aTanguay/Enssemble.io/GM_VOICINGS.md

# SAM2695 GM Voicing Reference
### All 128 General MIDI Programs + MT-32 Bank

Use Program Change (PC) messages to select voices. Send CC 0 = 0 for GM bank, CC 0 = 127 for MT-32 bank, followed by PC message.

---

## Bank 0 — General MIDI

### 🎹 Piano (PC 0–7)
| PC | Name |
|----|---|
| 0 | Acoustic Grand Piano |
| 1 | Bright Acoustic Piano |
| 2 | Electric Grand Piano |
| 3 | Honky-Tonk Piano |
| 4 | Electric Piano 1 |
| 5 | Electric Piano 2 |
| 6 | Harpsichord |
| 7 | Clavi |

### 🔔 Chromatic Percussion (PC 8–15)
| PC | Name |
|----|---|
| 8 | Celesta |
| 9 | Glockenspiel |
| 10 | Music Box |
| 11 | Vibraphone |
| 12 | Marimba |
| 13 | Xylophone |
| 14 | Tubular Bells |
| 15 | Santur |

### 🎹 Organ (PC 16–23)
| PC | Name |
|----|---|
| 16 | Drawbar Organ |
| 17 | Percussive Organ |
| 18 | Rock Organ |
| 19 | Church Organ |
| 20 | Reed Organ |
| 21 | Accordion |
| 22 | Harmonica |
| 23 | Tango Accordion |

### 🎸 Guitar (PC 24–31)
| PC | Name |
|----|---|
| 24 | Nylon Guitar |
| 25 | Steel Guitar |
| 26 | Jazz Guitar |
| 27 | Clean Guitar |
| 28 | Muted Guitar |
| 29 | Overdrive Guitar |
| 30 | Distortion Guitar |
| 31 | Guitar Harmonics |

### 🎸 Bass (PC 32–39)
| PC | Name |
|----|---|
| 32 | Acoustic Bass |
| 33 | Finger Bass |
| 34 | Pick Bass |
| 35 | Fretless Bass |
| 36 | Slap Bass 1 |
| 37 | Slap Bass 2 |
| 38 | Synth Bass 1 |
| 39 | Synth Bass 2 |

### 🎻 Strings (PC 40–47)
| PC | Name |
|----|---|
| 40 | Violin |
| 41 | Viola |
| 42 | Cello |
| 43 | Contrabass |
| 44 | Tremolo Strings |
| 45 | Pizzicato Strings |
| 46 | Orchestral Harp |
| 47 | Timpani |

### 🎻 Ensemble (PC 48–55)
| PC | Name |
|----|---|
| 48 | String Ensemble 1 |
| 49 | String Ensemble 2 |
| 50 | Synth Strings 1 |
| 51 | Synth Strings 2 |
| 52 | Choir Aahs |
| 53 | Voice Oohs |
| 54 | Synth Voice |
| 55 | Orchestra Hit |

### 🎺 Brass (PC 56–63)
| PC | Name |
|----|---|
| 56 | Trumpet |
| 57 | Trombone |
| 58 | Tuba |
| 59 | Muted Trumpet |
| 60 | French Horn |
| 61 | Brass Section |
| 62 | Synth Brass 1 |
| 63 | Synth Brass 2 |

### 🎷 Reed (PC 64–71)
| PC | Name |
|----|---|
| 64 | Soprano Sax |
| 65 | Alto Sax |
| 66 | Tenor Sax |
| 67 | Baritone Sax |
| 68 | Oboe |
| 69 | English Horn |
| 70 | Bassoon |
| 71 | Clarinet |

### 🪈 Pipe (PC 72–79)
| PC | Name |
|----|---|
| 72 | Piccolo |
| 73 | Flute |
| 74 | Recorder |
| 75 | Pan Flute |
| 76 | Blown Bottle |
| 77 | Shakuhachi |
| 78 | Whistle |
| 79 | Ocarina |

### 🎛️ Synth Lead (PC 80–87)
| PC | Name | Character |
|----|---|---|
| 80 | Lead 1 — Square | Hollow, buzzy |
| 81 | Lead 2 — Sawtooth | Bright, cutting |
| 82 | Lead 3 — Calliope | Soft, flute-like |
| 83 | Lead 4 — Chiff | Nasal, reedy |
| 84 | Lead 5 — Charang | Guitar-synth hybrid |
| 85 | Lead 6 — Voice | Vocal formant |
| 86 | Lead 7 — Fifths | Parallel 5ths drone |
| 87 | Lead 8 — Bass + Lead | Fat dual-layer |

### 🌊 Synth Pad (PC 88–95)
| PC | Name | Character |
|----|---|---|
| 88 | Pad 1 — Fantasia | Choir + strings wash |
| 89 | Pad 2 — Warm | Soft, pillowy |
| 90 | Pad 3 — Polysynth | Classic poly synth |
| 91 | Pad 4 — Choir | Choral wash |
| 92 | Pad 5 — Bowed | Glass harmonica |
| 93 | Pad 6 — Metallic | Bright, shimmery |
| 94 | Pad 7 — Halo | Ethereal, airy |
| 95 | Pad 8 — Sweep | Filter sweep swell |

### 🌀 Synth FX (PC 96–103)
| PC | Name | Character |
|----|---|---|
| 96 | FX 1 — Rain | Tinkly, percussive |
| 97 | FX 2 — Soundtrack | Cinematic swell |
| 98 | FX 3 — Crystal | Bell-like, glassy |
| 99 | FX 4 — Atmosphere | Ambient texture |
| 100 | FX 5 — Brightness | Bright shimmer |
| 101 | FX 6 — Goblins | Dark, eerie |
| 102 | FX 7 — Echoes | Delayed, spacey |
| 103 | FX 8 — Sci-fi | Electronic, alien |

### 🌍 Ethnic (PC 104–111)
| PC | Name |
|----|---|
| 104 | Sitar |
| 105 | Banjo |
| 106 | Shamisen |
| 107 | Koto |
| 108 | Kalimba |
| 109 | Bag Pipe |
| 110 | Fiddle |
| 111 | Shanai |

### 🥁 Percussive (PC 112–119)
| PC | Name |
|----|---|
| 112 | Tinkle Bell |
| 113 | Agogo |
| 114 | Steel Drums |
| 115 | Woodblock |
| 116 | Taiko Drum |
| 117 | Melodic Tom |
| 118 | Synth Drum |
| 119 | Reverse Cymbal |

### 🔊 Sound FX (PC 120–127)
| PC | Name |
|----|---|
| 120 | Guitar Fret Noise |
| 121 | Breath Noise |
| 122 | Seashore |
| 123 | Bird Tweet |
| 124 | Telephone Ring |
| 125 | Helicopter |
| 126 | Applause |
| 127 | Gunshot |

---

## Bank 127 — MT-32
*Access via CC 0 = 127, then Program Change*

The MT-32 bank provides Roland MT-32 compatible sounds — a different character
from GM. More vintage, more '80s/'90s electronic. Great for leads and textures.
Notable differences from GM: different piano voicing, distinctive synth leads,
and unique atmospheric pads not in the GM set.

*Note: Program numbers map to the same slots 0–127 but with different timbres.*

---

## Suggested Presets Per Band Role

### 🎹 Keys / Piano *(spare voicings — no dedicated member in the current roster)*
```
PC 0   Acoustic Grand Piano   ← default
PC 4   Electric Piano 1
PC 5   Electric Piano 2
PC 6   Harpsichord
PC 16  Drawbar Organ
PC 18  Rock Organ
PC 19  Church Organ
PC 88  Pad 1 Fantasia
```

### ⚡ Prynz — Lead Synth
```
PC 80  Lead 1 Square          ← default
PC 81  Lead 2 Sawtooth
PC 82  Lead 3 Calliope
PC 84  Lead 5 Charang
PC 85  Lead 6 Voice
PC 86  Lead 7 Fifths
PC 64  Soprano Sax
PC 73  Flute
```

### 🎸 Botsee — Bass
```
PC 32  Acoustic Bass          ← default
PC 33  Finger Bass
PC 35  Fretless Bass
PC 36  Slap Bass 1
PC 38  Synth Bass 1
PC 39  Synth Bass 2
PC 43  Contrabass
PC 34  Pick Bass
```

### 🌊 Eenoo — Pads / Atmosphere
```
PC 88  Pad 1 Fantasia         ← default
PC 89  Pad 2 Warm
PC 90  Pad 3 Polysynth
PC 91  Pad 4 Choir
PC 94  Pad 7 Halo
PC 95  Pad 8 Sweep
PC 99  FX 4 Atmosphere
PC 102 FX 7 Echoes
```

### 🎻 Strings / Ensemble *(spare voicings — no dedicated member in the current roster)*
```
PC 48  String Ensemble 1      ← default
PC 49  String Ensemble 2
PC 40  Violin
PC 44  Tremolo Strings
PC 45  Pizzicato Strings
PC 50  Synth Strings 1
PC 52  Choir Aahs
PC 55  Orchestra Hit
```

---

## Drums — MIDI Channel 10

Per GM spec, **channel 10 is always drums** on the SAM2695.
Note numbers map to individual drum sounds — no program change needed.

| Note | Sound | | Note | Sound |
|---|---|-|---|---|
| 35 | Acoustic Bass Drum | | 51 | Ride Cymbal 1 |
| 36 | Bass Drum 1 | | 52 | Chinese Cymbal |
| 37 | Side Stick | | 53 | Ride Bell |
| 38 | Acoustic Snare | | 54 | Tambourine |
| 39 | Hand Clap | | 55 | Splash Cymbal |
| 40 | Electric Snare | | 56 | Cowbell |
| 41 | Low Floor Tom | | 57 | Crash Cymbal 2 |
| 42 | Closed Hi-Hat | | 58 | Vibraslap |
| 43 | High Floor Tom | | 59 | Ride Cymbal 2 |
| 44 | Pedal Hi-Hat | | 60 | High Bongo |
| 45 | Low Tom | | 61 | Low Bongo |
| 46 | Open Hi-Hat | | 62 | Mute Hi Conga |
| 47 | Low-Mid Tom | | 63 | Open Hi Conga |
| 48 | Hi-Mid Tom | | 64 | Low Conga |
| 49 | Crash Cymbal 1 | | 65 | High Timbale |
| 50 | High Tom | | 66 | Low Timbale |

---

## Quick Reference — Button Navigation

```
[0] short  →  Next curated preset for this unit's role
[1] short  →  Previous curated preset
[2] short  →  Next GM instrument (+1 fine)
[3] short  →  Previous GM instrument (-1 fine)
[0] long   →  Next GM category (+8 jump)
[1] long   →  Previous GM category (-8 jump)
[2] long   →  Volume up
[3] long   →  Volume down
```

*Changing voice plays a short audition note so you always know what you're hearing.*
