aTanguay/Enssemble.io/Docs/AmyBoard/amy-main/docs/3d-envelopes.png

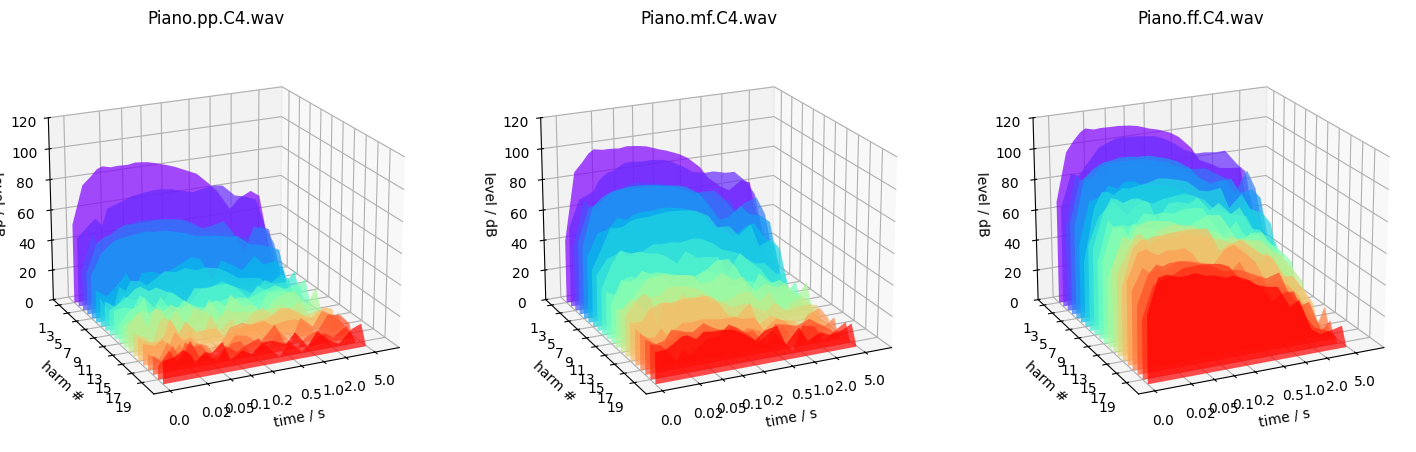
Docs/AmyBoard/amy-main/docs/3d-envelopes.png
