aTanguay/Enssemble.io/Docs/AmyBoard/amy-main/docs/AMY-Arduino-ESP32S3_bb.png

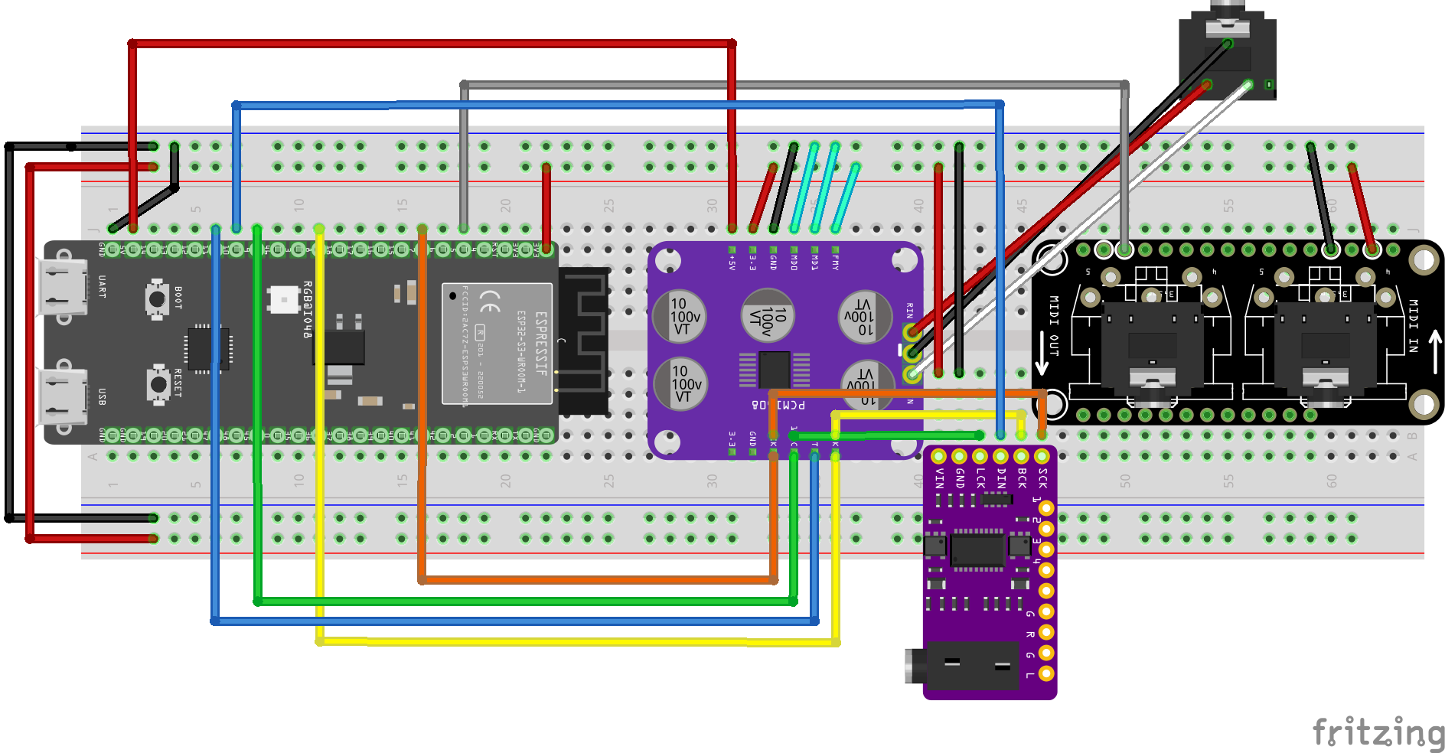
Docs/AmyBoard/amy-main/docs/AMY-Arduino-ESP32S3_bb.png
