aTanguay/Enssemble.io/Docs/AmyBoard/amy-main/docs/amy_dark.png

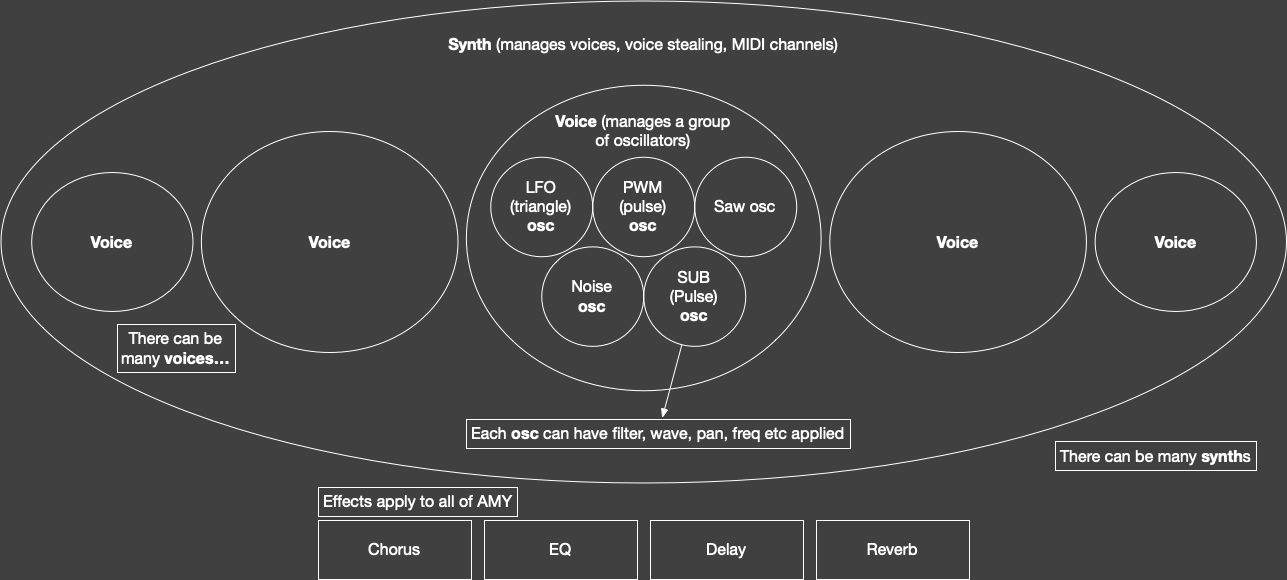
Docs/AmyBoard/amy-main/docs/amy_dark.png
