aTanguay/Enssemble.io/Docs/AmyBoard/amy-main/docs/amy_light.png

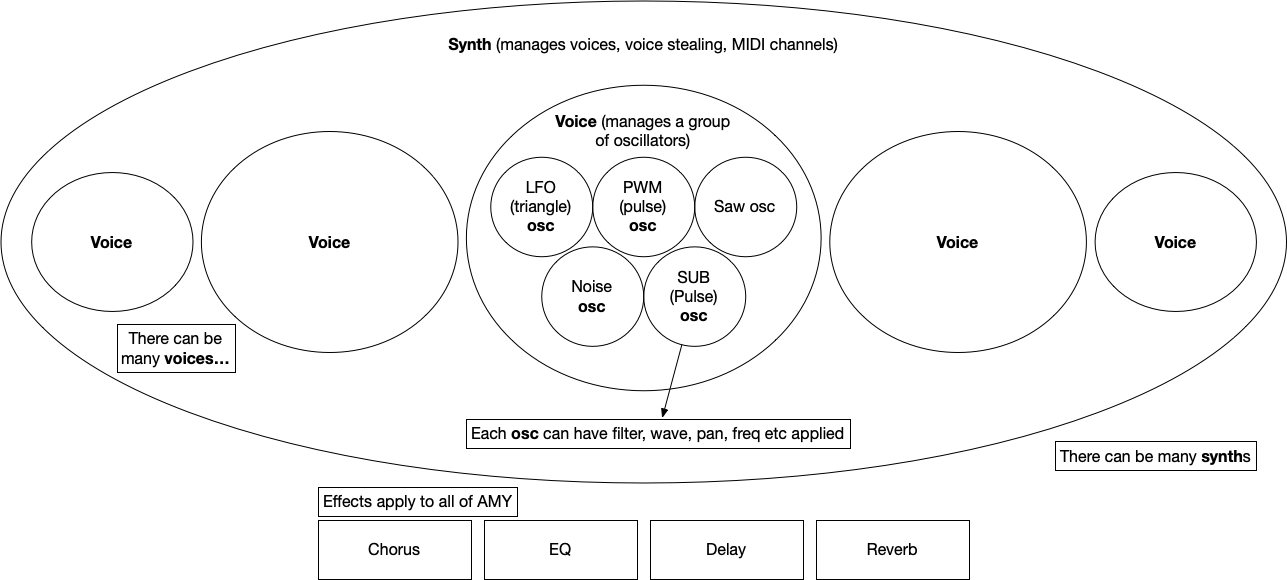
Docs/AmyBoard/amy-main/docs/amy_light.png
