aTanguay/Enssemble.io/Docs/AmyBoard/amy-main/docs/arduino1.png

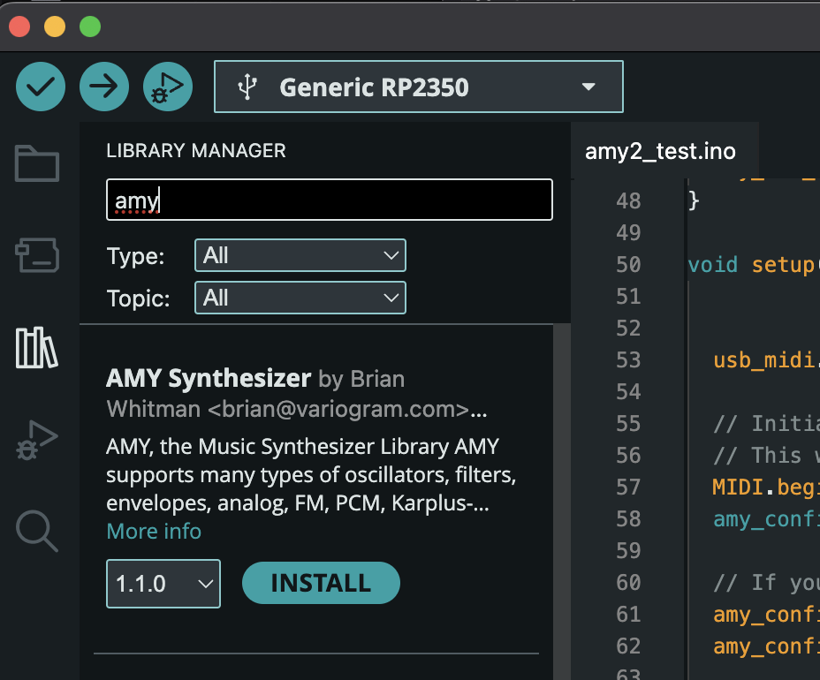
Docs/AmyBoard/amy-main/docs/arduino1.png
