aTanguay/Enssemble.io/Docs/AmyBoard/amy-main/docs/d4ff.png

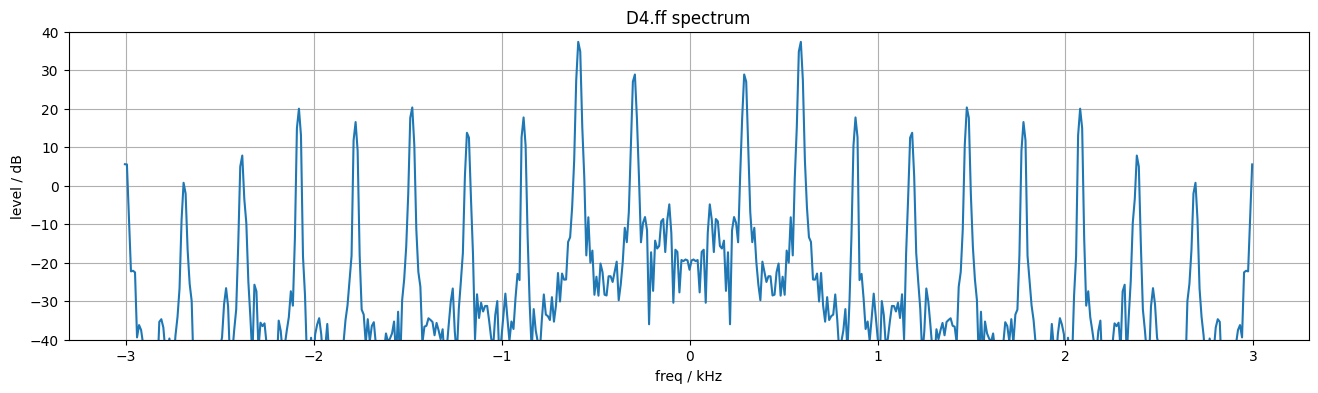
Docs/AmyBoard/amy-main/docs/d4ff.png
