aTanguay/Enssemble.io/Docs/AmyBoard/amy-main/docs/d4harm.png

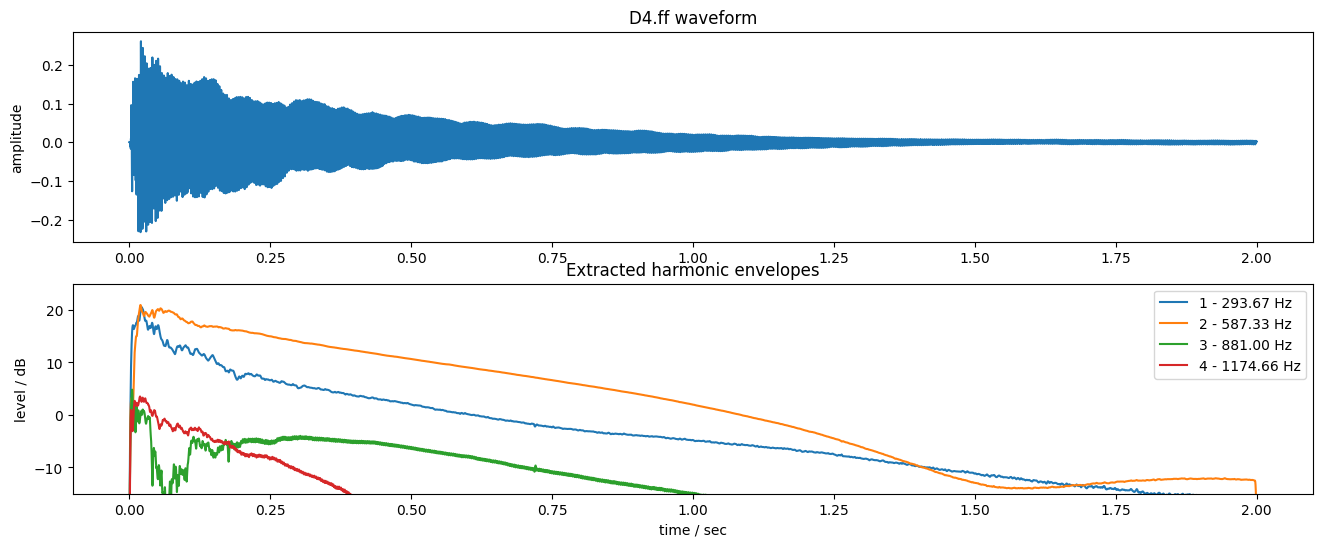
Docs/AmyBoard/amy-main/docs/d4harm.png
