aTanguay/Enssemble.io/Docs/AmyBoard/amy-main/docs/drum.png

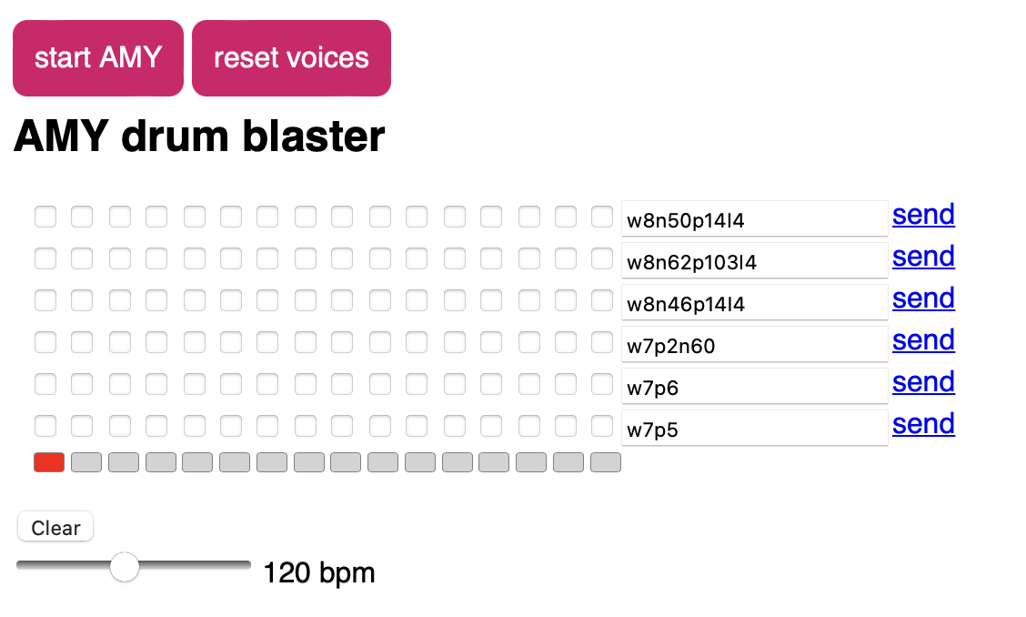
Docs/AmyBoard/amy-main/docs/drum.png
