aTanguay/Enssemble.io/Docs/AmyBoard/amy-main/docs/dx7.png

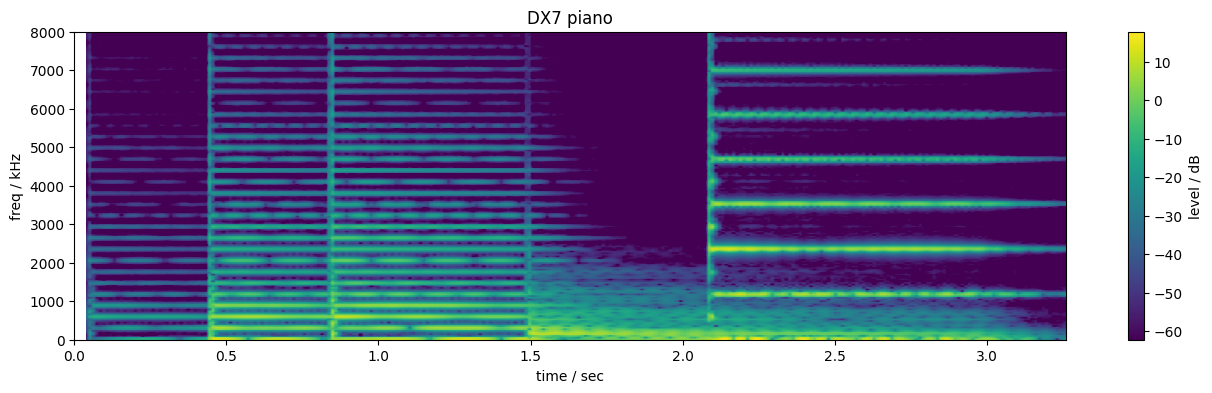
Docs/AmyBoard/amy-main/docs/dx7.png
