aTanguay/Enssemble.io/Docs/AmyBoard/amy-main/docs/env1.gif

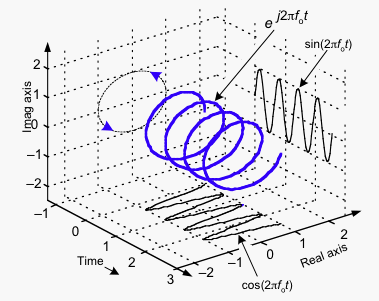
Docs/AmyBoard/amy-main/docs/env1.gif
