aTanguay/Enssemble.io/Docs/AmyBoard/amy-main/docs/envelope.png

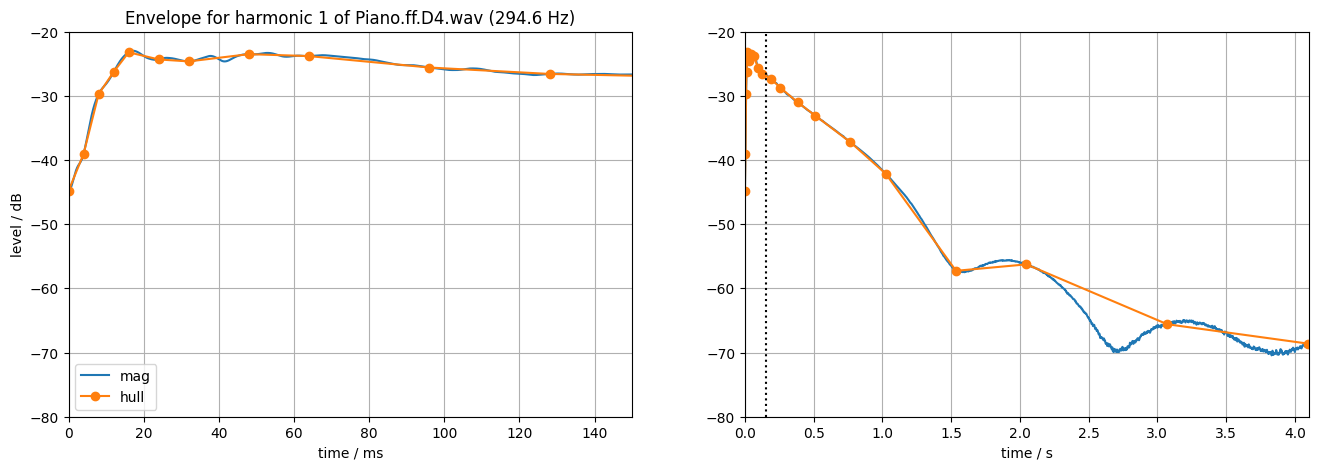
Docs/AmyBoard/amy-main/docs/envelope.png
