aTanguay/Enssemble.io/Docs/AmyBoard/amy-main/docs/fixed.png

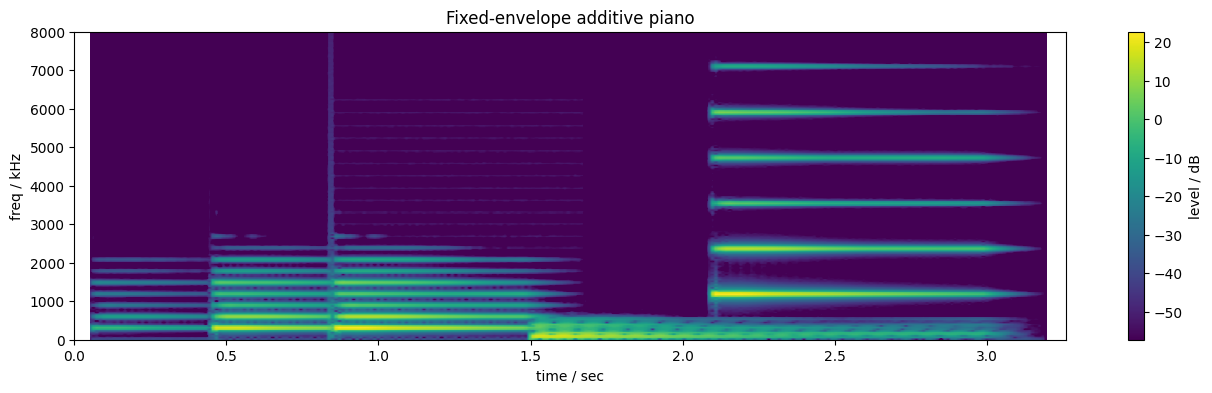
Docs/AmyBoard/amy-main/docs/fixed.png
