aTanguay/Enssemble.io/Docs/AmyBoard/amy-main/docs/fundamental.png

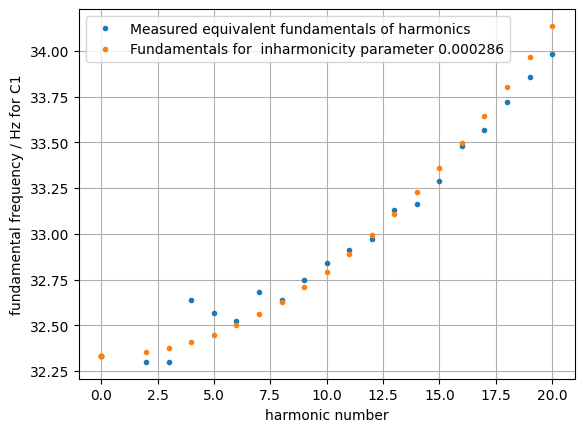
Docs/AmyBoard/amy-main/docs/fundamental.png
