aTanguay/Enssemble.io/Docs/AmyBoard/amy-main/docs/sh101.png

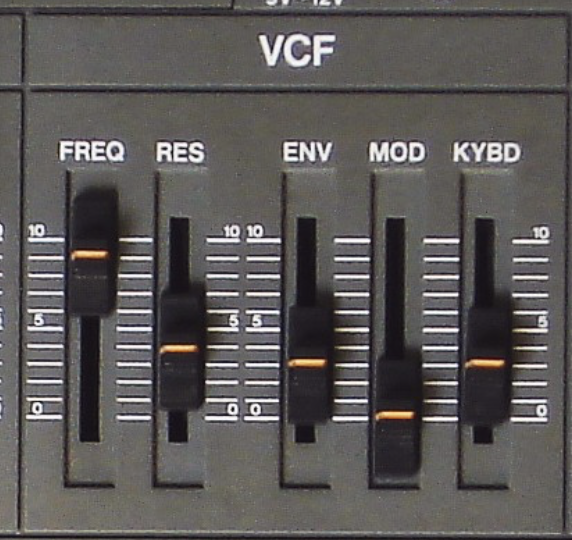
Docs/AmyBoard/amy-main/docs/sh101.png
