aTanguay/Enssemble.io/Docs/Amyboard/Arduino_Modulino-main/docs/images/modulino-buttons.jpeg

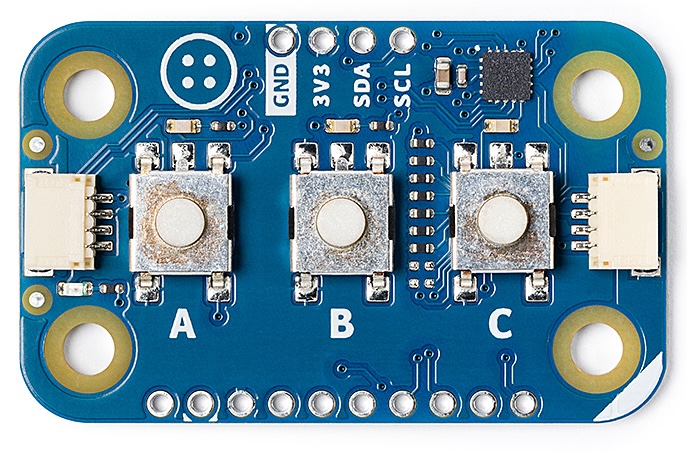
Docs/Amyboard/Arduino_Modulino-main/docs/images/modulino-buttons.jpeg
