aTanguay/Enssemble.io/Docs/Amyboard/Arduino_Modulino-main/docs/images/modulino-buzzer.jpg

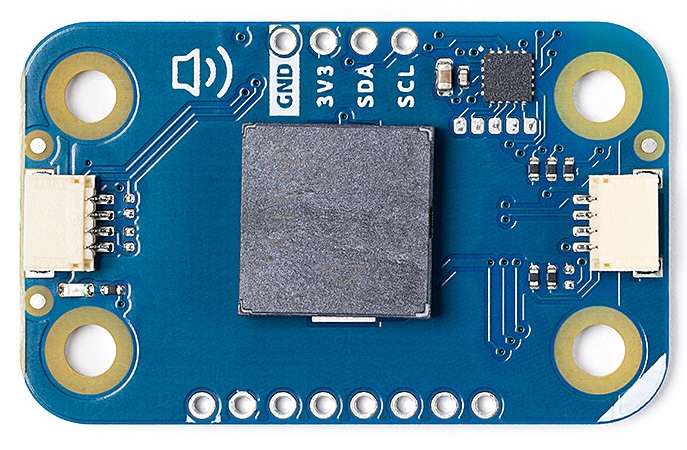
Docs/Amyboard/Arduino_Modulino-main/docs/images/modulino-buzzer.jpg
