aTanguay/Enssemble.io/Docs/Amyboard/Arduino_Modulino-main/docs/images/modulino-distance.jpg

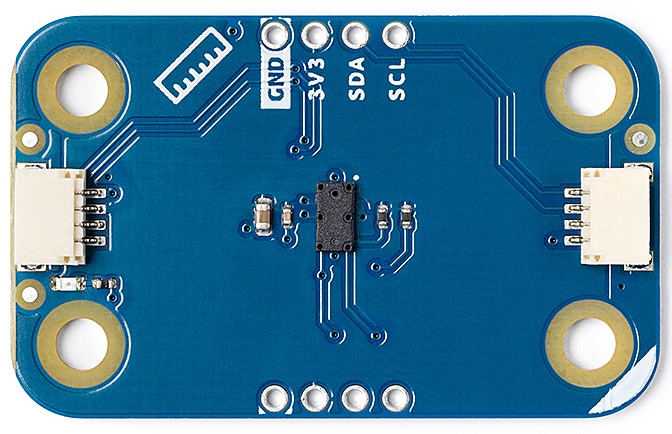
Docs/Amyboard/Arduino_Modulino-main/docs/images/modulino-distance.jpg
