aTanguay/Enssemble.io/Docs/Amyboard/Arduino_Modulino-main/docs/images/modulino-joystick.jpg

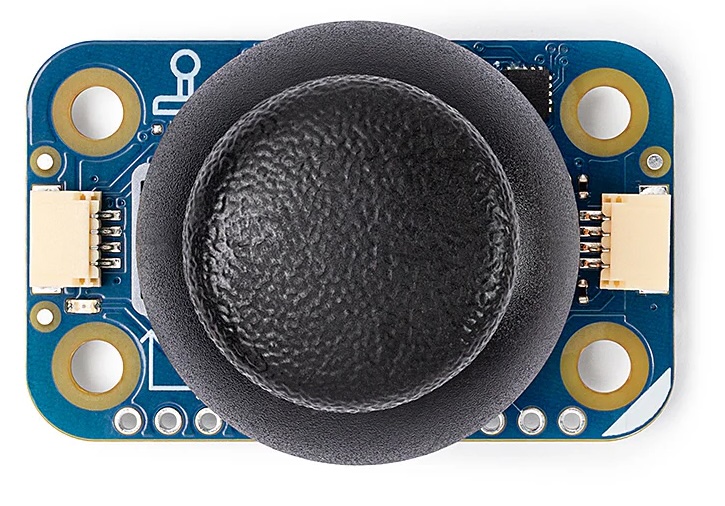
Docs/Amyboard/Arduino_Modulino-main/docs/images/modulino-joystick.jpg
