aTanguay/Enssemble.io/Docs/Amyboard/Arduino_Modulino-main/docs/images/modulino-knob.jpg

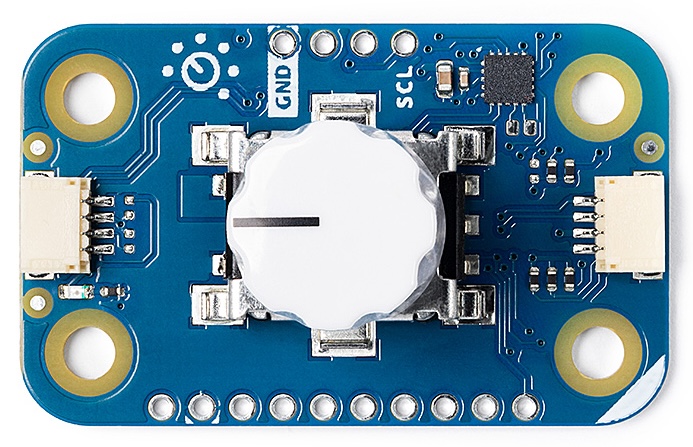
Docs/Amyboard/Arduino_Modulino-main/docs/images/modulino-knob.jpg
