aTanguay/Enssemble.io/Docs/Amyboard/Arduino_Modulino-main/docs/images/modulino-latch-relay.jpg

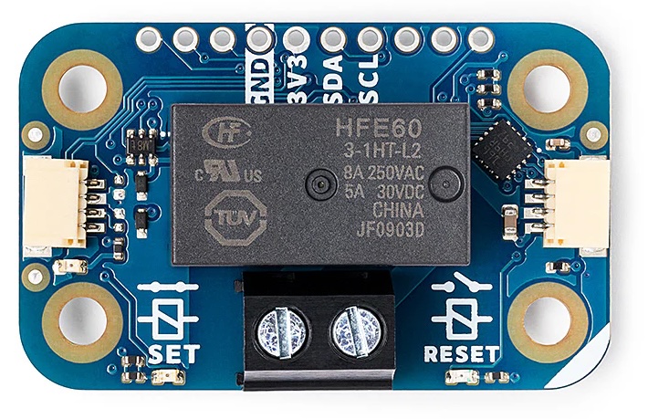
Docs/Amyboard/Arduino_Modulino-main/docs/images/modulino-latch-relay.jpg
