aTanguay/Enssemble.io/Docs/Amyboard/Arduino_Modulino-main/docs/images/modulino-led-matrix.jpg

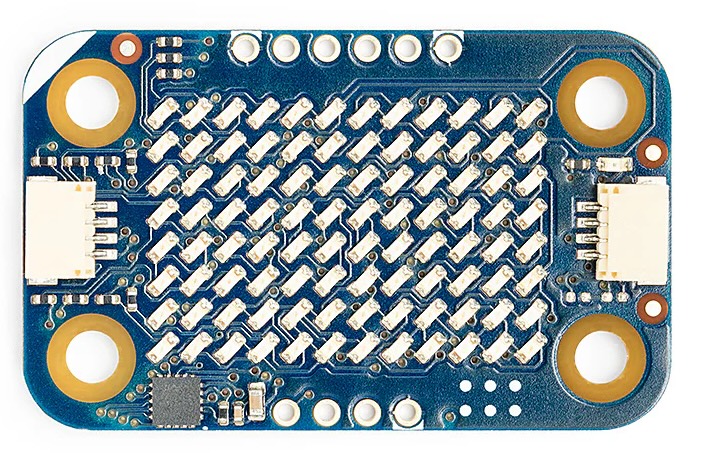
Docs/Amyboard/Arduino_Modulino-main/docs/images/modulino-led-matrix.jpg
