aTanguay/Enssemble.io/Docs/Amyboard/Arduino_Modulino-main/docs/images/modulino-light.jpg

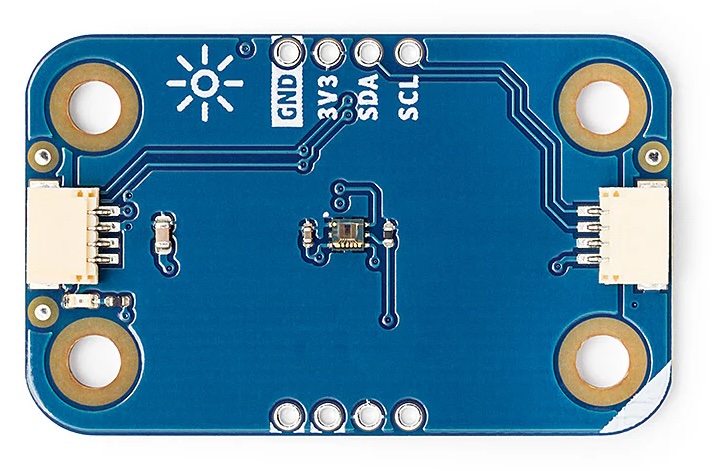
Docs/Amyboard/Arduino_Modulino-main/docs/images/modulino-light.jpg
