aTanguay/Enssemble.io/Docs/Amyboard/Arduino_Modulino-main/docs/images/modulino-pixels.jpg

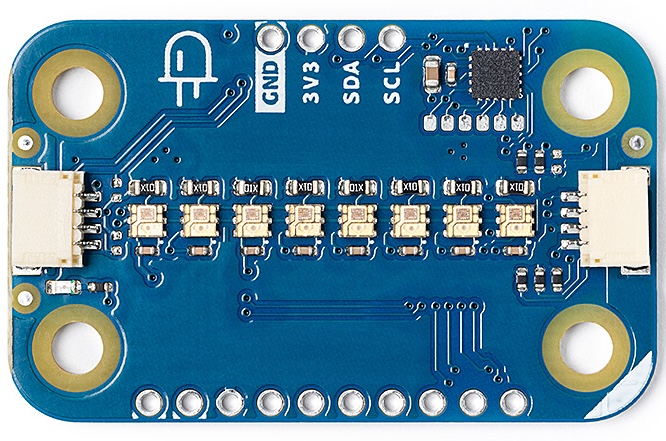
Docs/Amyboard/Arduino_Modulino-main/docs/images/modulino-pixels.jpg
