aTanguay/Enssemble.io/Docs/Amyboard/Arduino_Modulino-main/docs/images/modulino-thermo.jpg

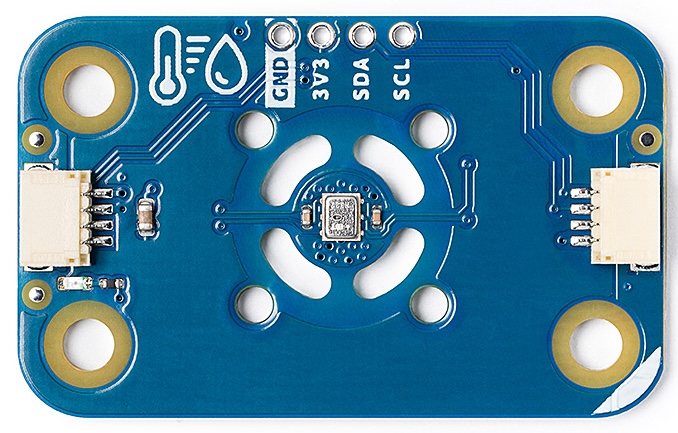
Docs/Amyboard/Arduino_Modulino-main/docs/images/modulino-thermo.jpg
