aTanguay/Enssemble.io/Docs/Amyboard/Arduino_Modulino-main/docs/images/modulino-vibro.jpg

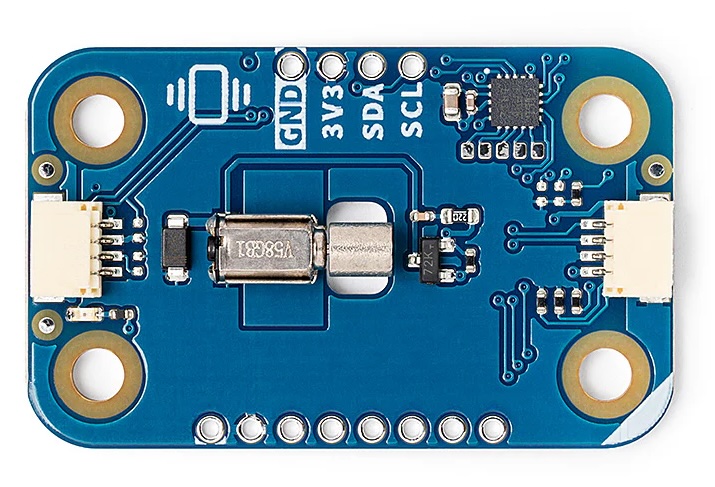
Docs/Amyboard/Arduino_Modulino-main/docs/images/modulino-vibro.jpg
