aTanguay/Enssemble.io/Docs/Amyboard/tulipcc-main/assets/img/amyboard-1.jpg

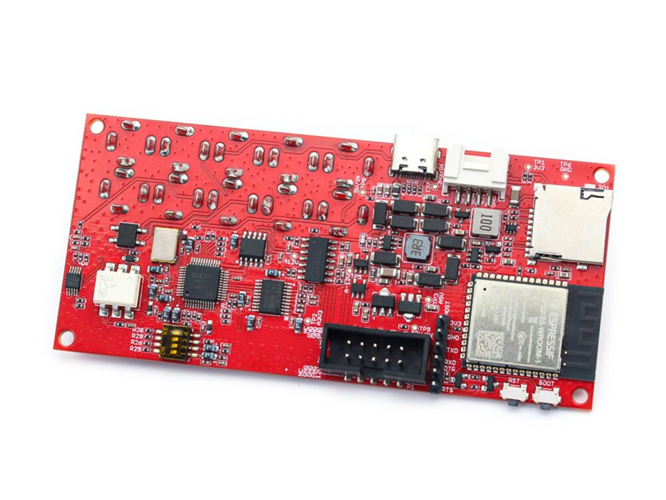
Docs/Amyboard/tulipcc-main/assets/img/amyboard-1.jpg
