aTanguay/Enssemble.io/Docs/Amyboard/tulipcc-main/assets/img/amyboard-2.jpg

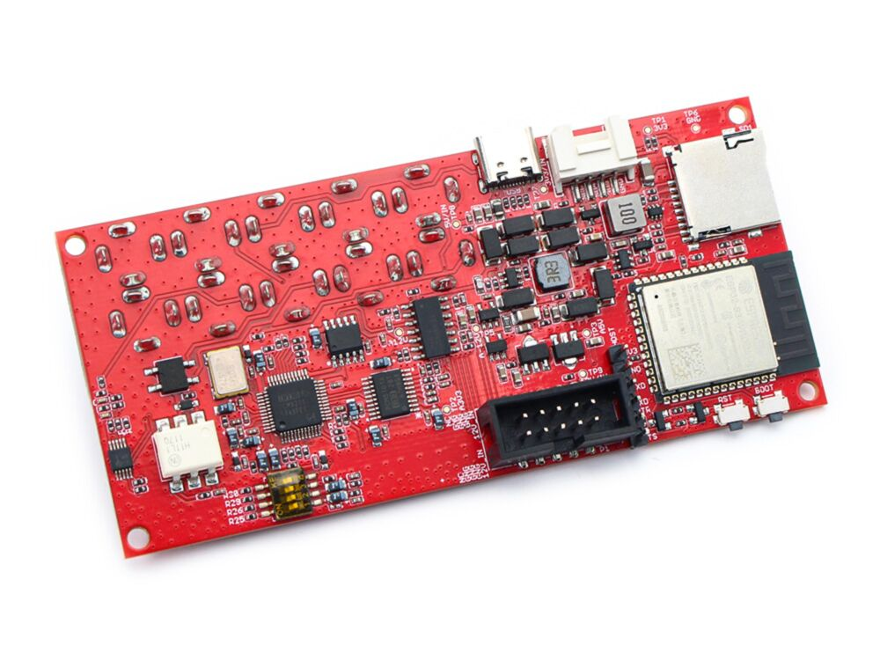
Docs/Amyboard/tulipcc-main/assets/img/amyboard-2.jpg
