aTanguay/Enssemble.io/Docs/Amyboard/tulipcc-main/assets/img/amyboard-3.jpg

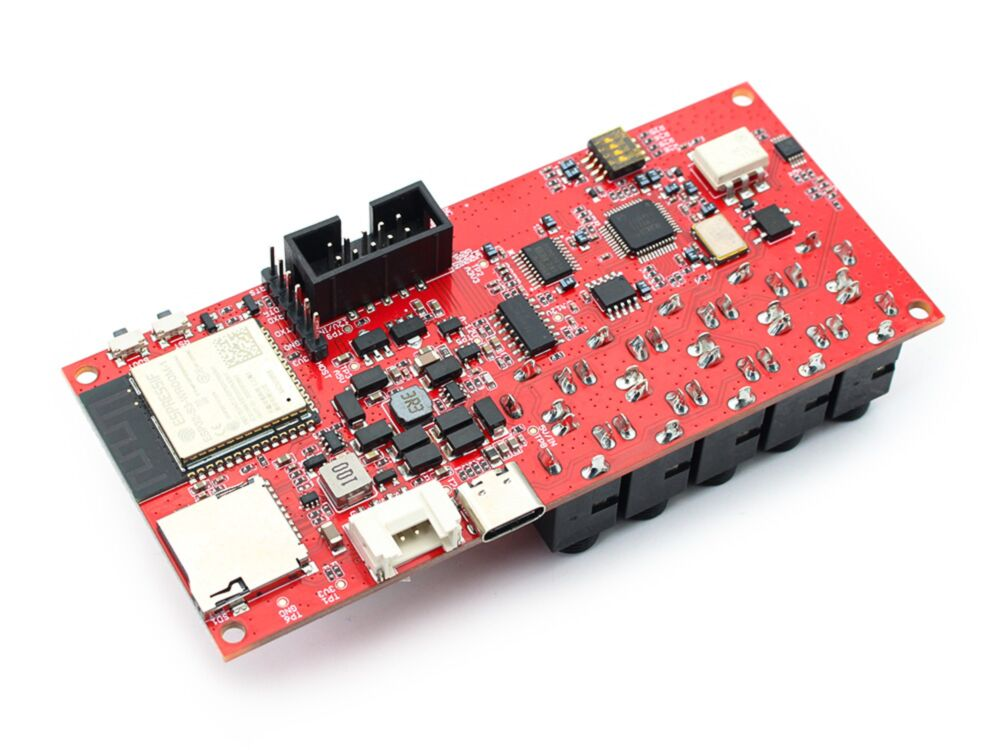
Docs/Amyboard/tulipcc-main/assets/img/amyboard-3.jpg
