aTanguay/Enssemble.io/Docs/Amyboard/tulipcc-main/assets/img/amyboard-5.jpg

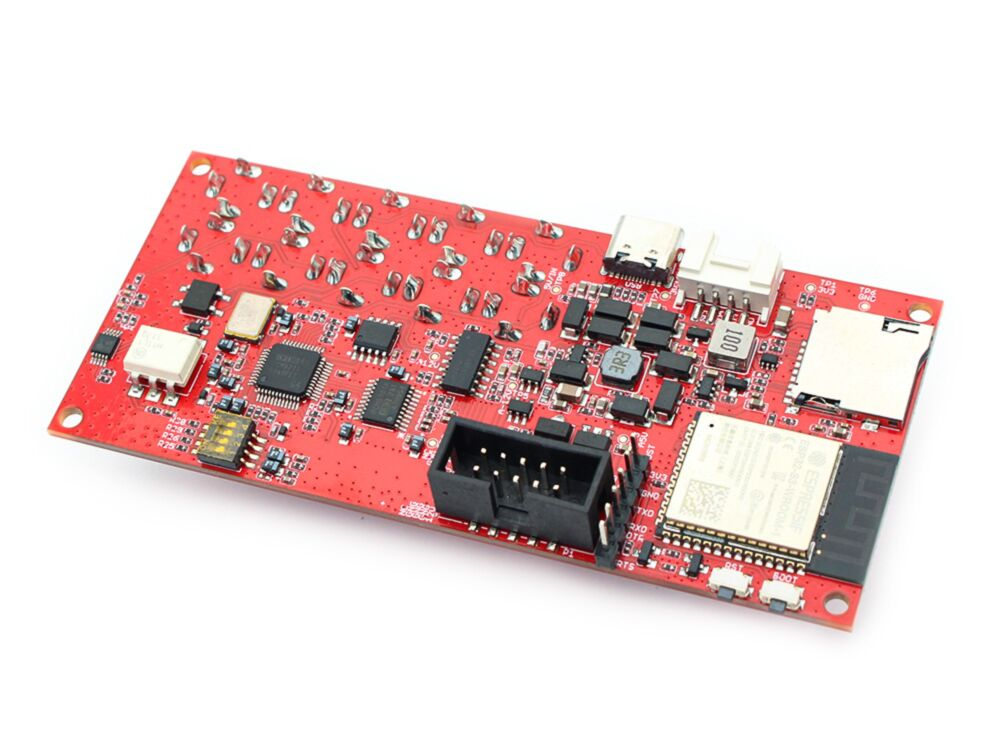
Docs/Amyboard/tulipcc-main/assets/img/amyboard-5.jpg
