aTanguay/Enssemble.io/Docs/Amyboard/tulipcc-main/assets/img/amyboard-8.jpg

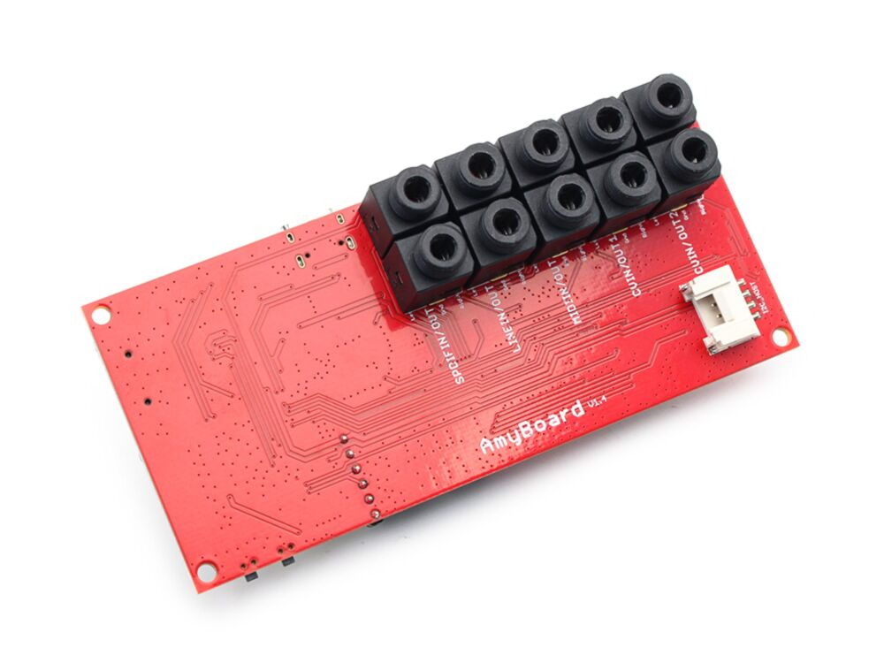
Docs/Amyboard/tulipcc-main/assets/img/amyboard-8.jpg
