aTanguay/Enssemble.io/Docs/Amyboard/tulipcc-main/assets/img/amyboard-9.jpg

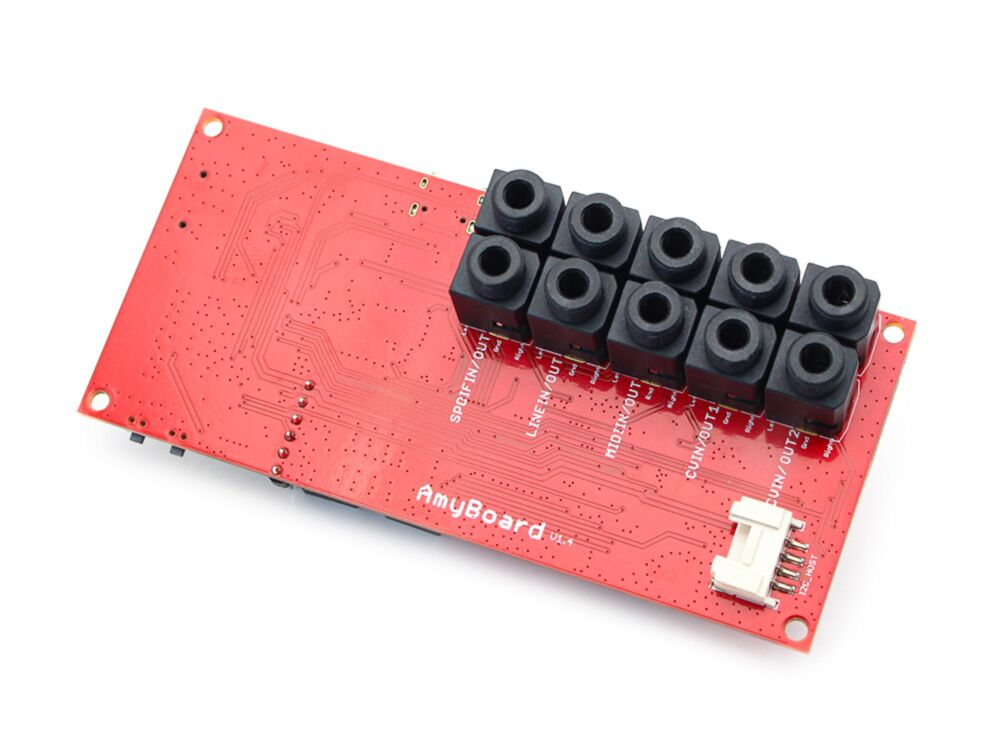
Docs/Amyboard/tulipcc-main/assets/img/amyboard-9.jpg
