aTanguay/Enssemble.io/Docs/Amyboard/tulipcc-main/assets/img/amyboard.jpg

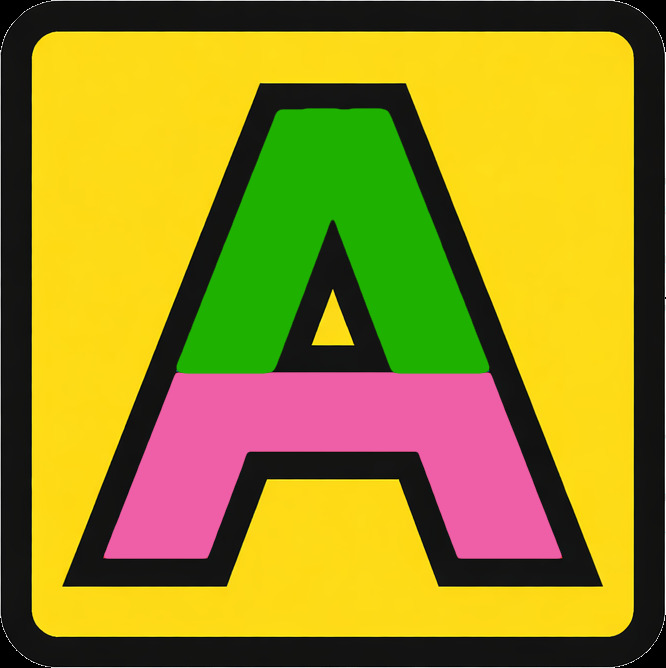
Docs/Amyboard/tulipcc-main/assets/img/amyboard.jpg
