aTanguay/Enssemble.io/Docs/Amyboard/tulipcc-main/assets/img/amyboard.png

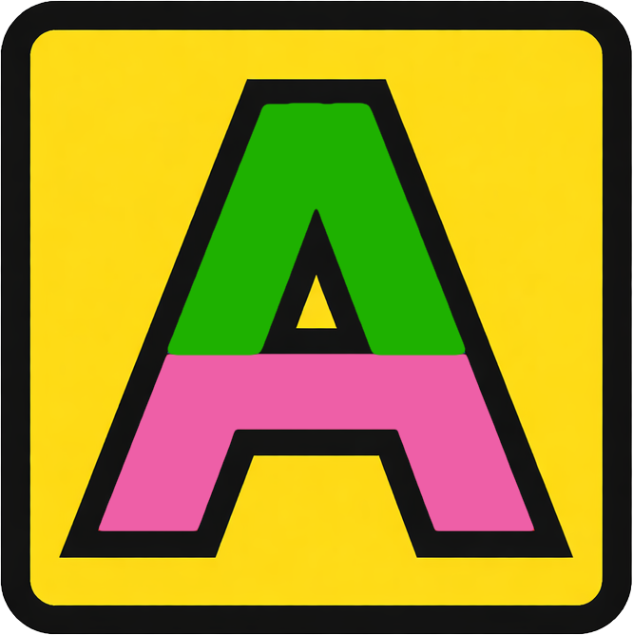
Docs/Amyboard/tulipcc-main/assets/img/amyboard.png
