aTanguay/Enssemble.io/Docs/Amyboard/tulipcc-main/assets/img/amyboard_accessories_back.jpg

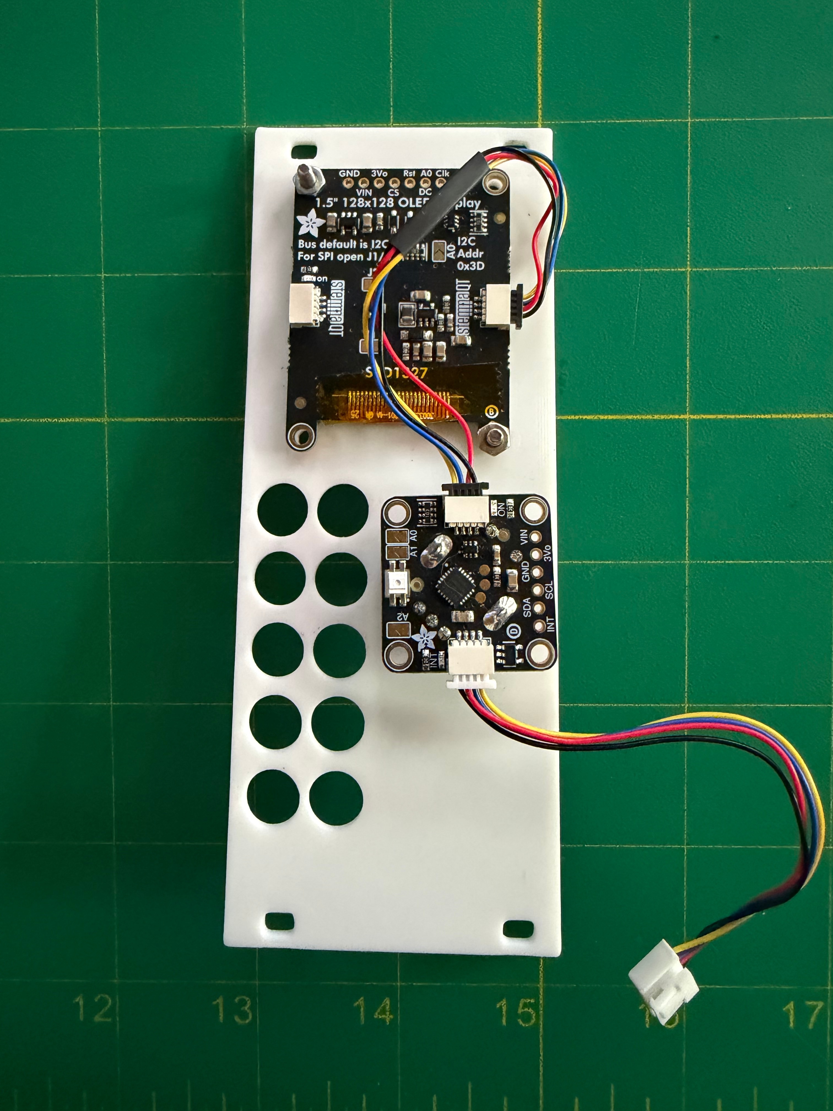
Docs/Amyboard/tulipcc-main/assets/img/amyboard_accessories_back.jpg
