aTanguay/Enssemble.io/Docs/Amyboard/tulipcc-main/assets/img/amyboard_back_desk.jpg

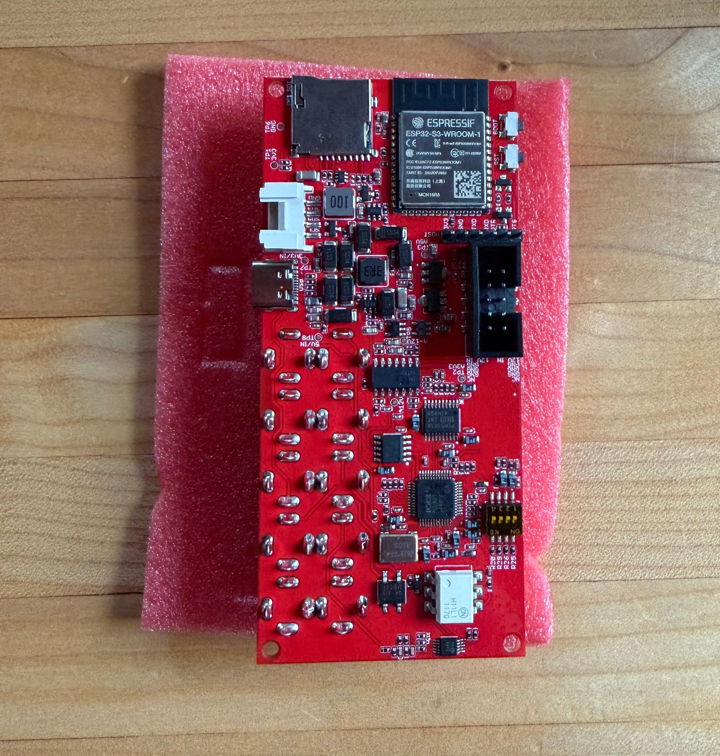
Docs/Amyboard/tulipcc-main/assets/img/amyboard_back_desk.jpg
