aTanguay/Enssemble.io/Docs/Amyboard/tulipcc-main/assets/img/amyboard_back_moss.jpg

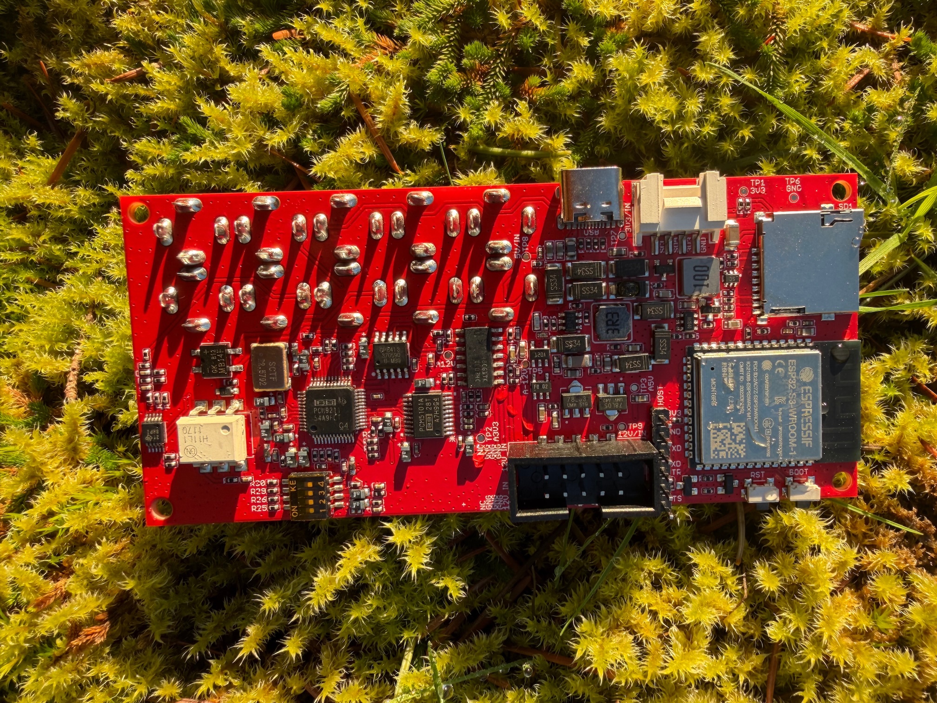
Docs/Amyboard/tulipcc-main/assets/img/amyboard_back_moss.jpg
