aTanguay/Enssemble.io/Docs/Amyboard/tulipcc-main/assets/img/amyboard_back_panel_annotated.jpg

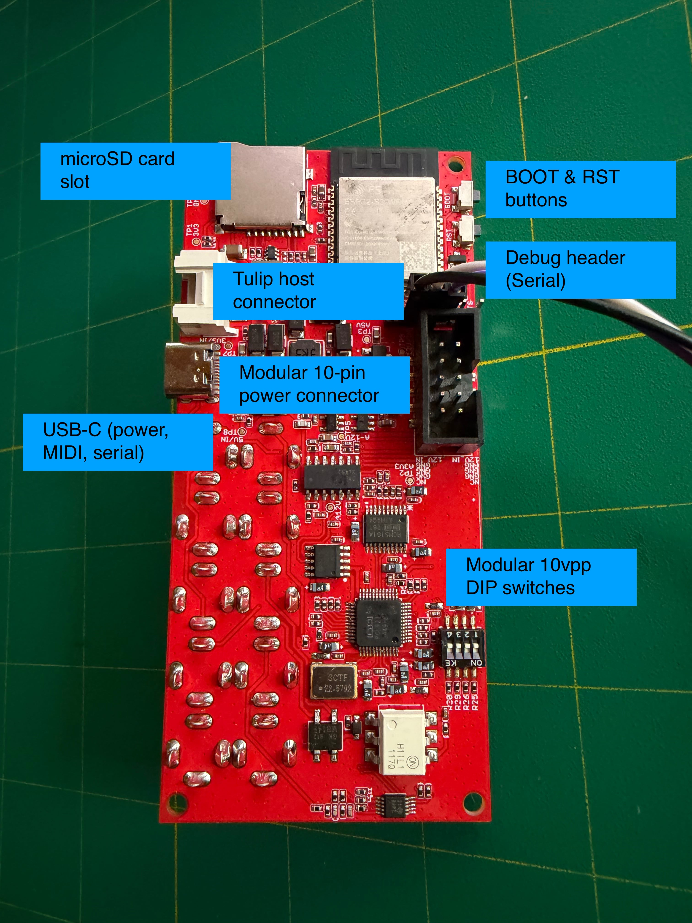
Docs/Amyboard/tulipcc-main/assets/img/amyboard_back_panel_annotated.jpg
