aTanguay/Enssemble.io/Docs/Amyboard/tulipcc-main/assets/img/amyboard_bambu.png

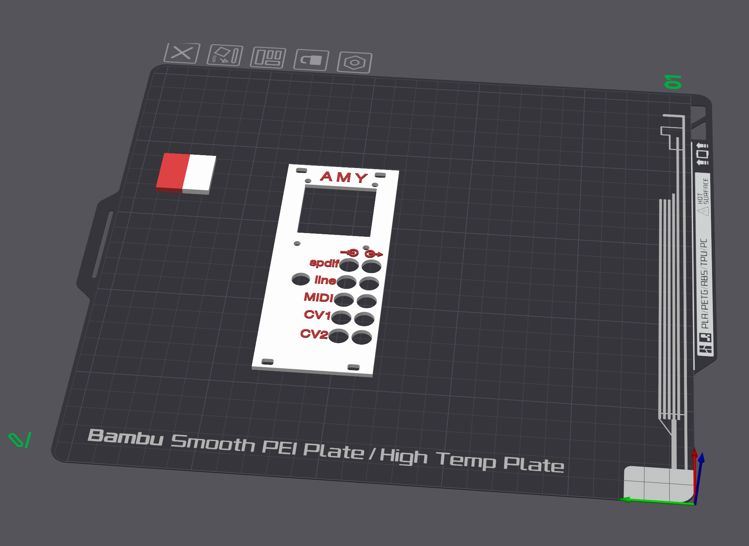
Docs/Amyboard/tulipcc-main/assets/img/amyboard_bambu.png
