aTanguay/Enssemble.io/Docs/Amyboard/tulipcc-main/assets/img/amyboard_box.jpg

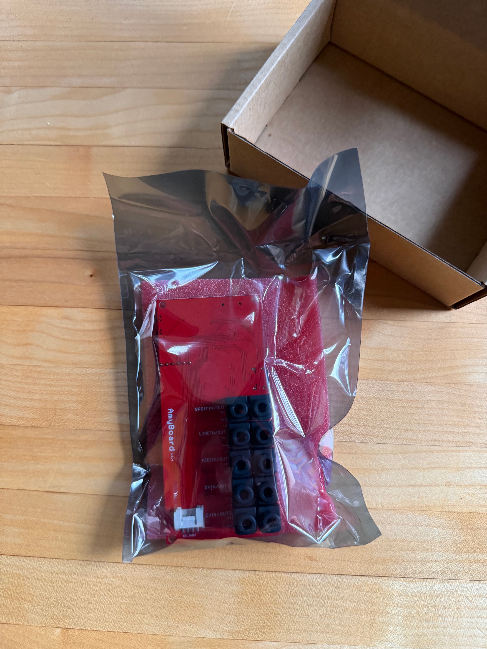
Docs/Amyboard/tulipcc-main/assets/img/amyboard_box.jpg
