aTanguay/Enssemble.io/Docs/Amyboard/tulipcc-main/assets/img/amyboard_editor_preview.png

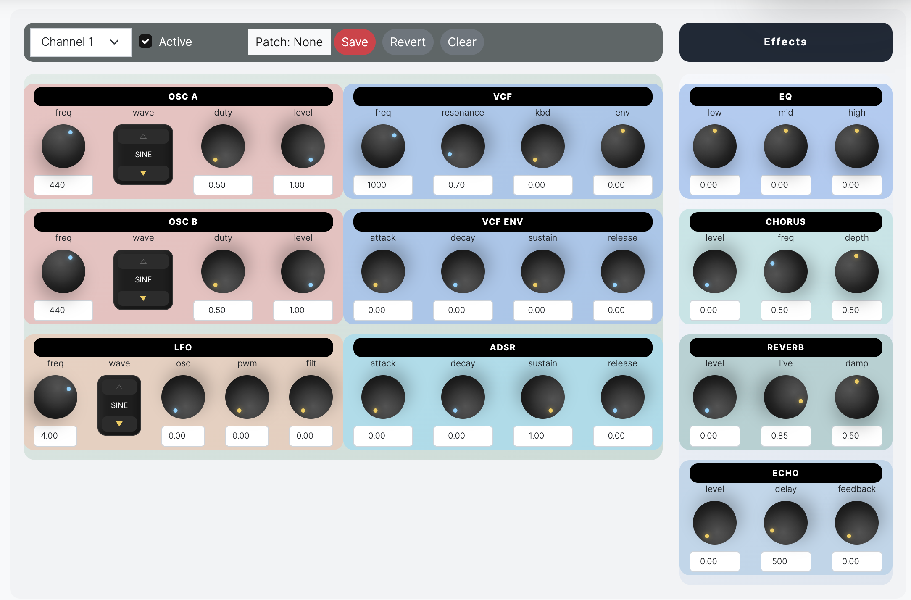
Docs/Amyboard/tulipcc-main/assets/img/amyboard_editor_preview.png
