aTanguay/Enssemble.io/Docs/Amyboard/tulipcc-main/assets/img/amyboard_front_desk.jpg

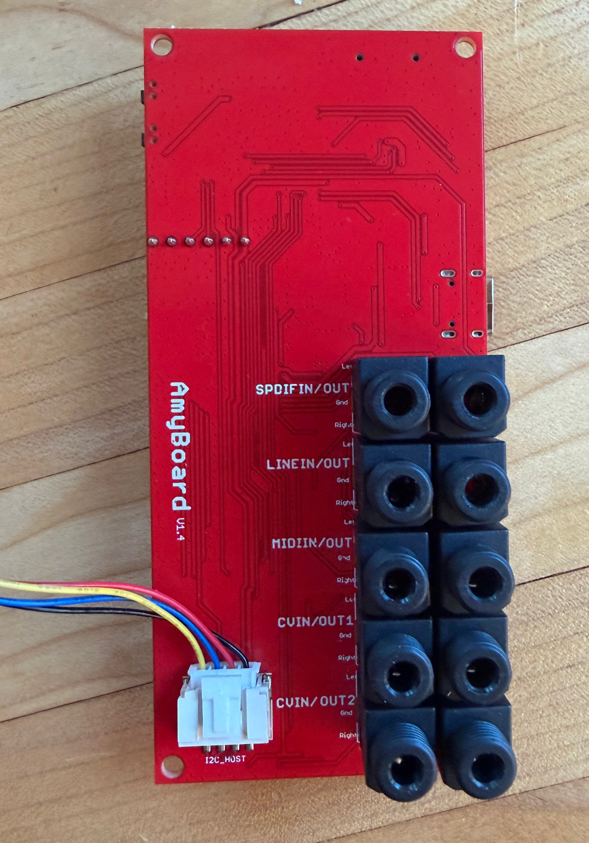
Docs/Amyboard/tulipcc-main/assets/img/amyboard_front_desk.jpg
