aTanguay/Enssemble.io/Docs/Amyboard/tulipcc-main/assets/img/amyboard_front_moss.jpg

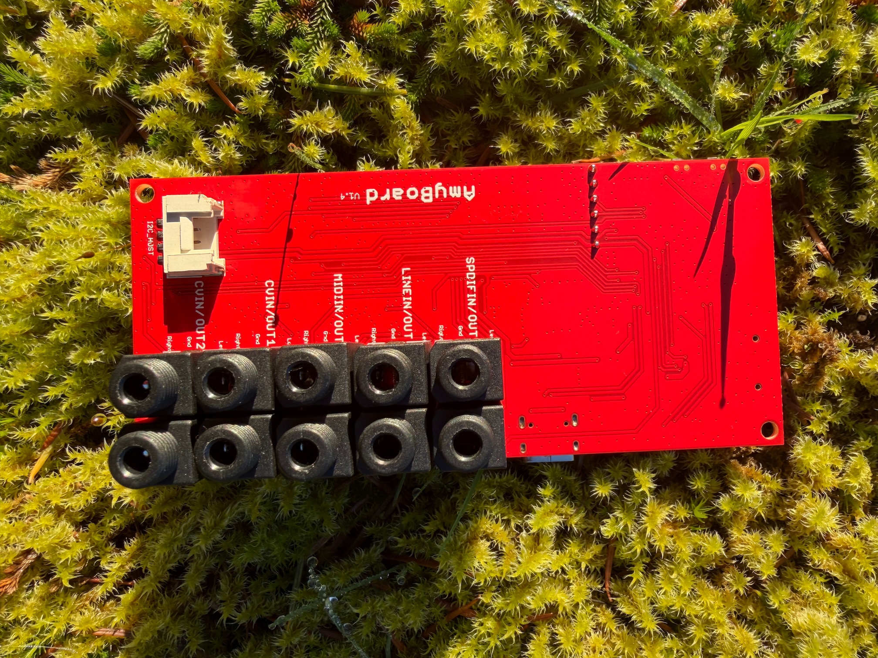
Docs/Amyboard/tulipcc-main/assets/img/amyboard_front_moss.jpg
