aTanguay/Enssemble.io/Docs/Amyboard/tulipcc-main/assets/img/amyboard_hero.png

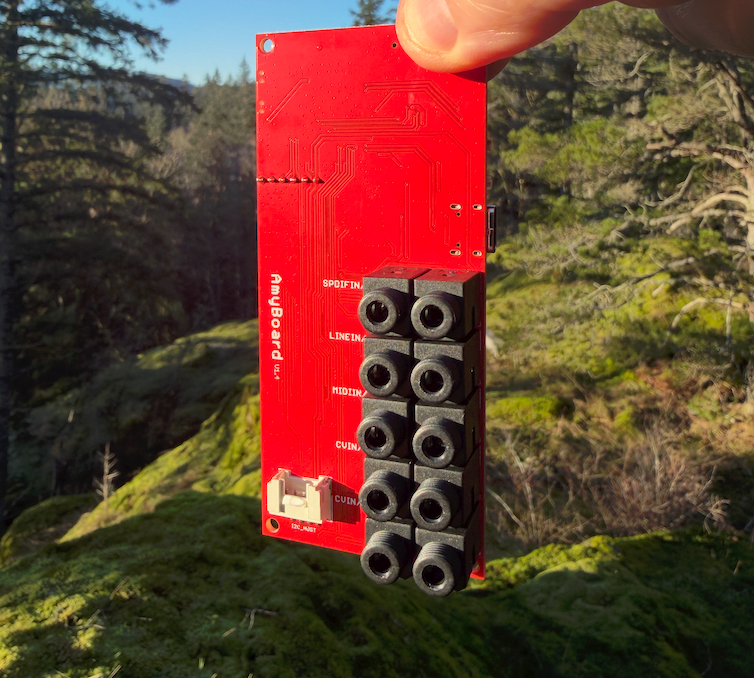
Docs/Amyboard/tulipcc-main/assets/img/amyboard_hero.png
