aTanguay/Enssemble.io/Docs/Amyboard/tulipcc-main/assets/img/amyboard_modular.jpg

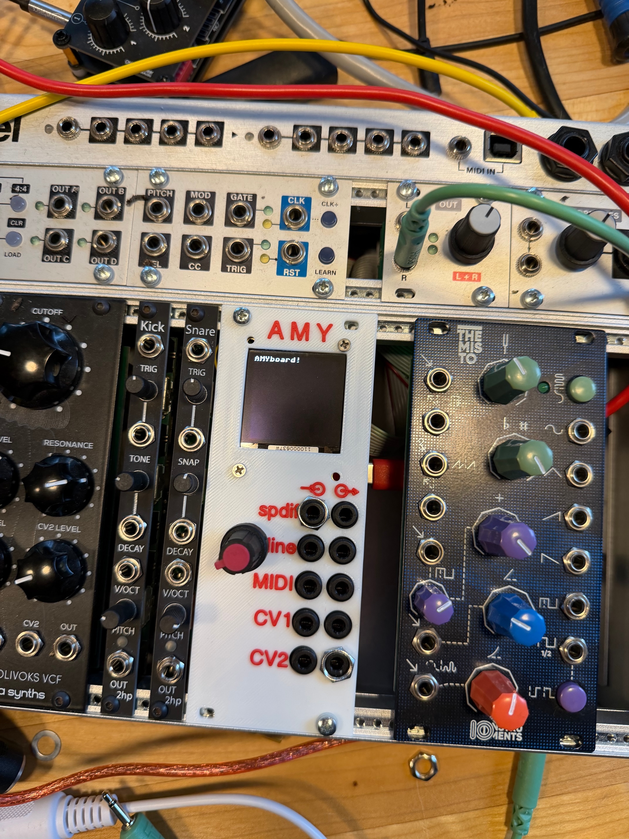
Docs/Amyboard/tulipcc-main/assets/img/amyboard_modular.jpg
