aTanguay/Enssemble.io/Docs/Amyboard/tulipcc-main/assets/img/amyboard_moss.jpg

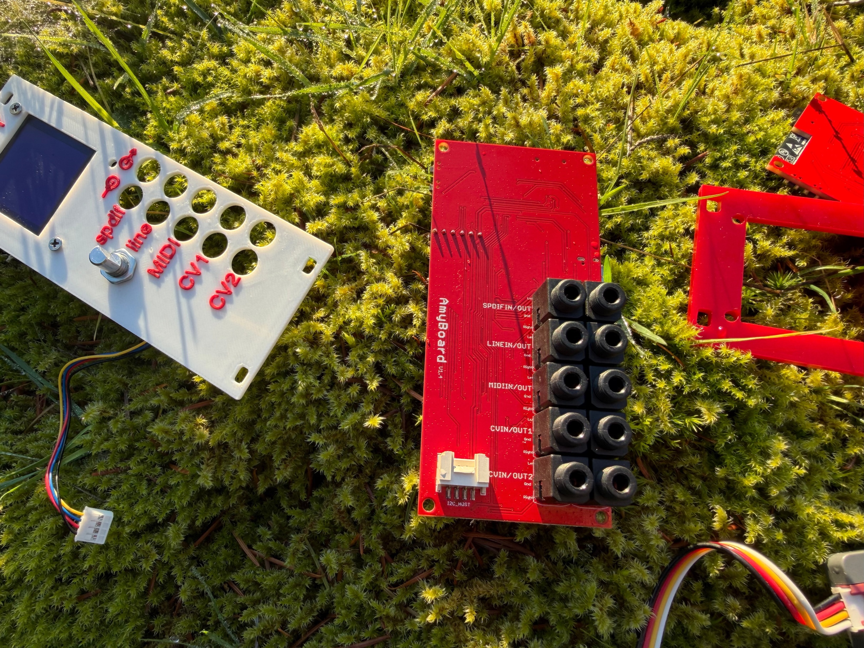
Docs/Amyboard/tulipcc-main/assets/img/amyboard_moss.jpg
