aTanguay/Enssemble.io/Docs/Amyboard/tulipcc-main/assets/img/amyboard_online.png

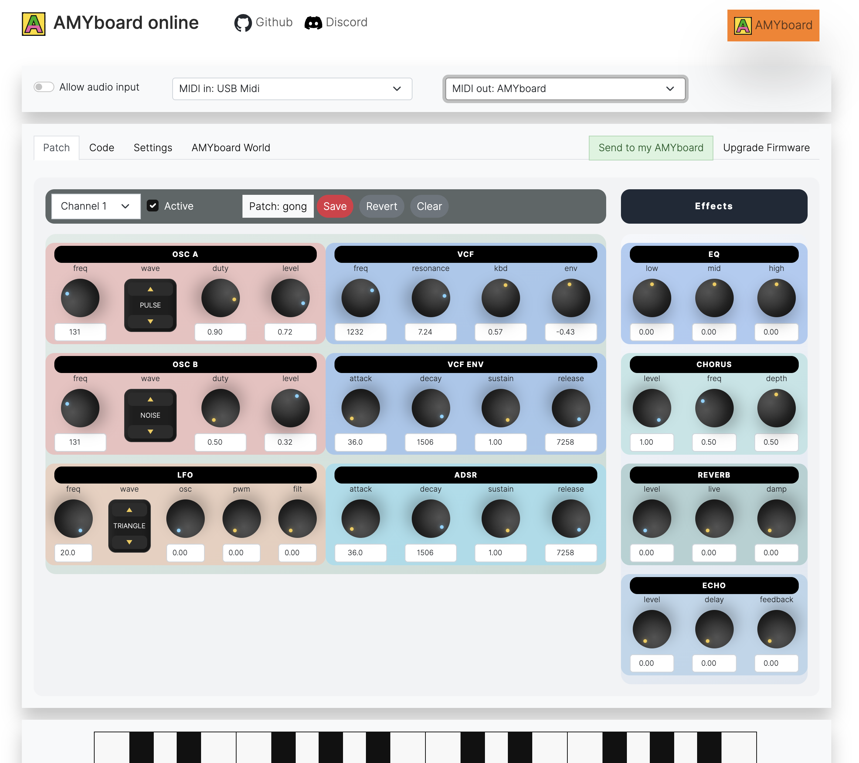
Docs/Amyboard/tulipcc-main/assets/img/amyboard_online.png
