aTanguay/Enssemble.io/Docs/Amyboard/tulipcc-main/assets/img/amyboard_online_code.png

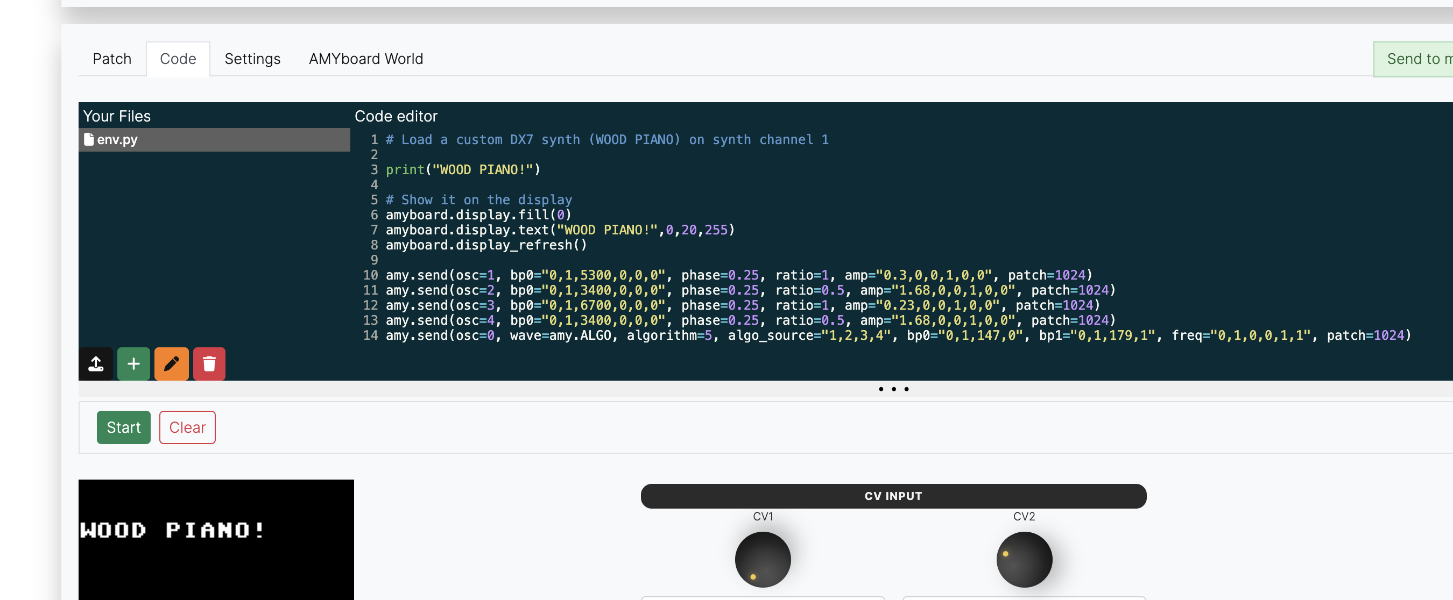
Docs/Amyboard/tulipcc-main/assets/img/amyboard_online_code.png
