aTanguay/Enssemble.io/Docs/Amyboard/tulipcc-main/assets/img/amyboard_outside.jpg

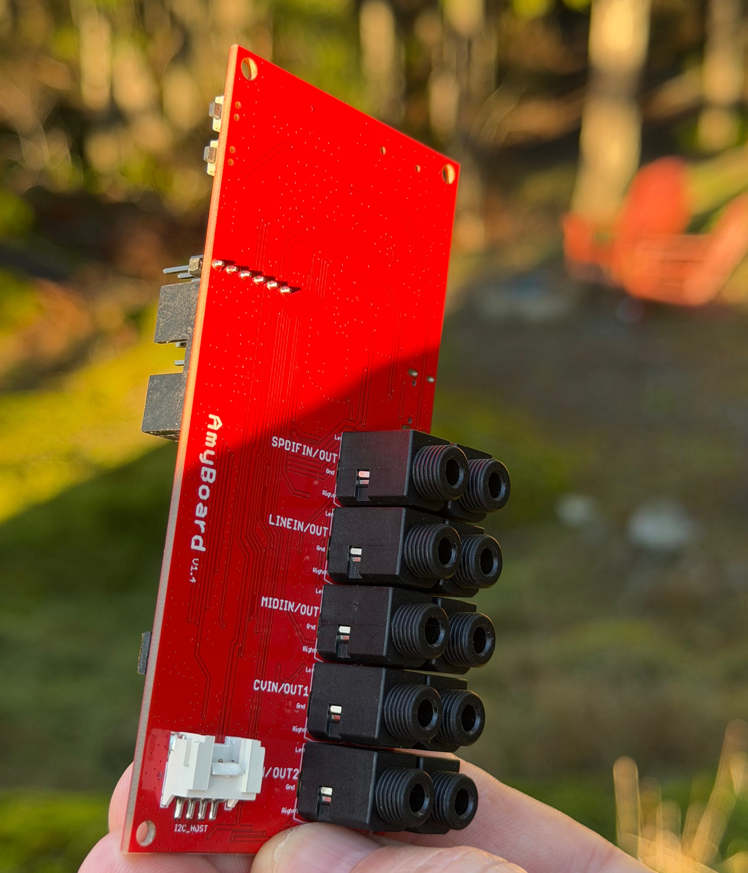
Docs/Amyboard/tulipcc-main/assets/img/amyboard_outside.jpg
