aTanguay/Enssemble.io/Docs/Amyboard/tulipcc-main/assets/img/amyboard_panels.jpg

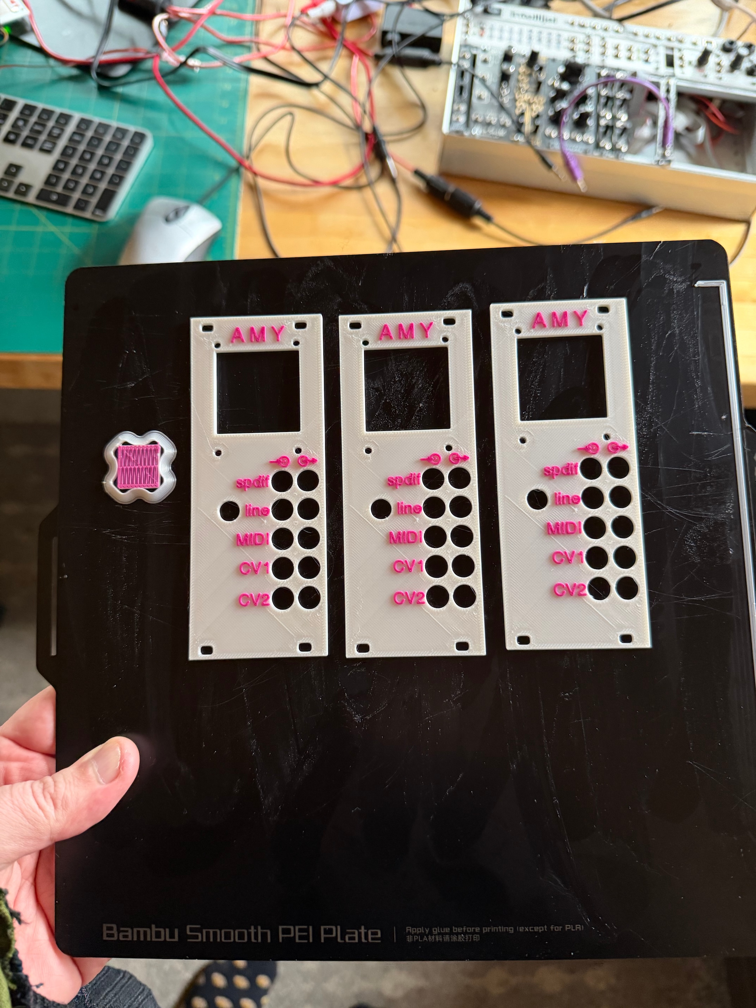
Docs/Amyboard/tulipcc-main/assets/img/amyboard_panels.jpg
