aTanguay/Enssemble.io/Docs/Amyboard/tulipcc-main/assets/img/amyboard_plexi.jpeg

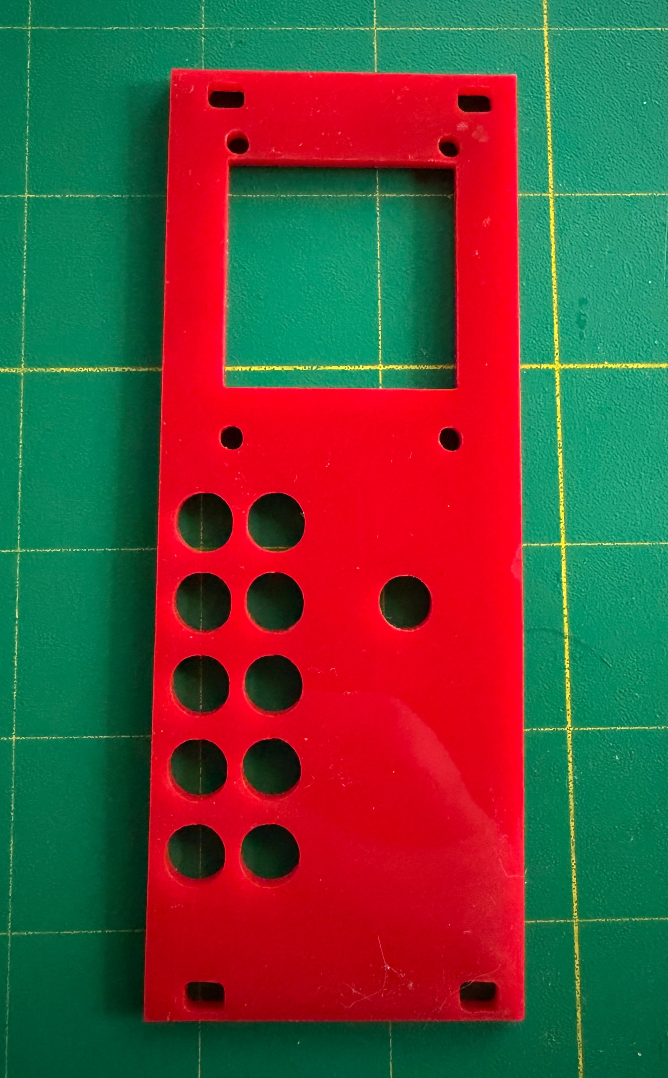
Docs/Amyboard/tulipcc-main/assets/img/amyboard_plexi.jpeg
