aTanguay/Enssemble.io/Docs/Amyboard/tulipcc-main/assets/img/amyboard_preview.jpg

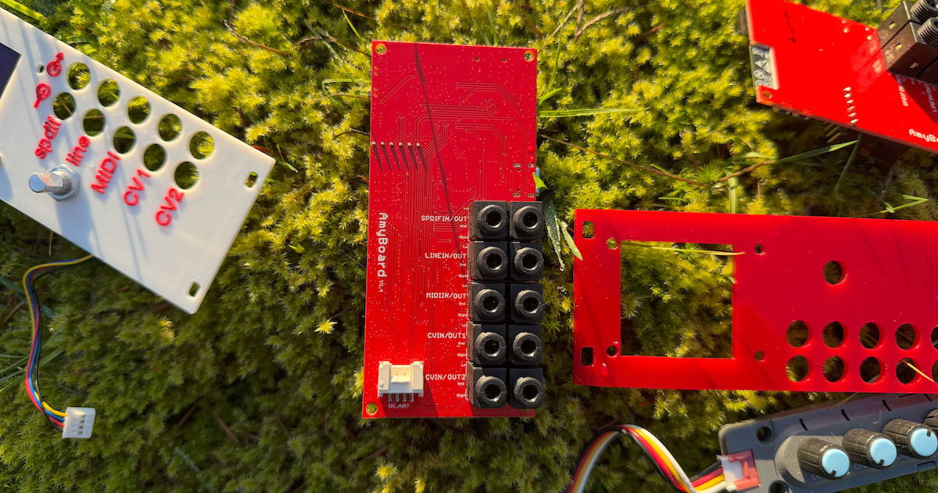
Docs/Amyboard/tulipcc-main/assets/img/amyboard_preview.jpg
