aTanguay/Enssemble.io/Docs/Amyboard/tulipcc-main/assets/img/boot_rst.jpg

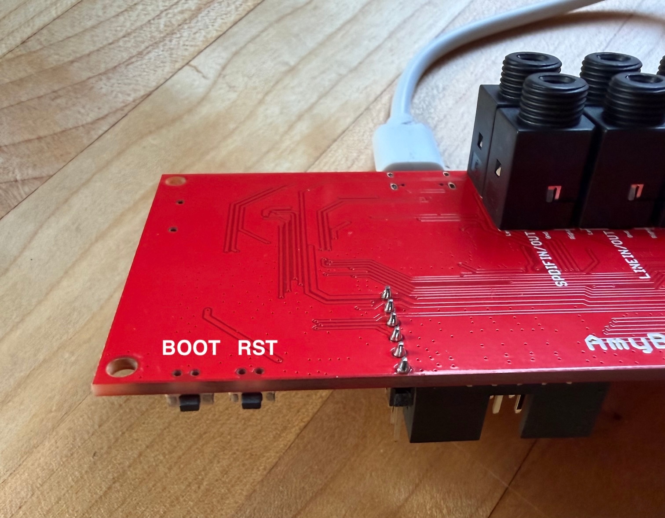
Docs/Amyboard/tulipcc-main/assets/img/boot_rst.jpg
