aTanguay/Enssemble.io/Docs/Amyboard/tulipcc-main/assets/img/dip_switches.png

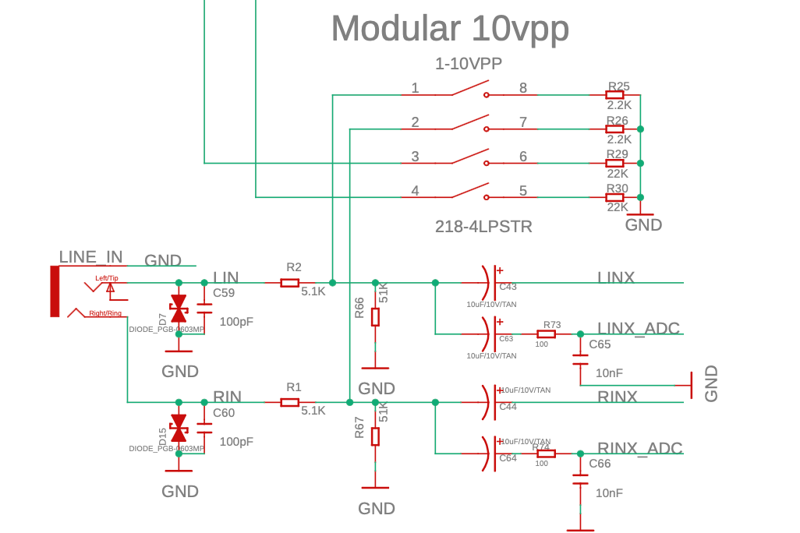
Docs/Amyboard/tulipcc-main/assets/img/dip_switches.png
