aTanguay/Enssemble.io/Docs/Amyboard/tulipcc-main/assets/img/mabee-dac.jpg

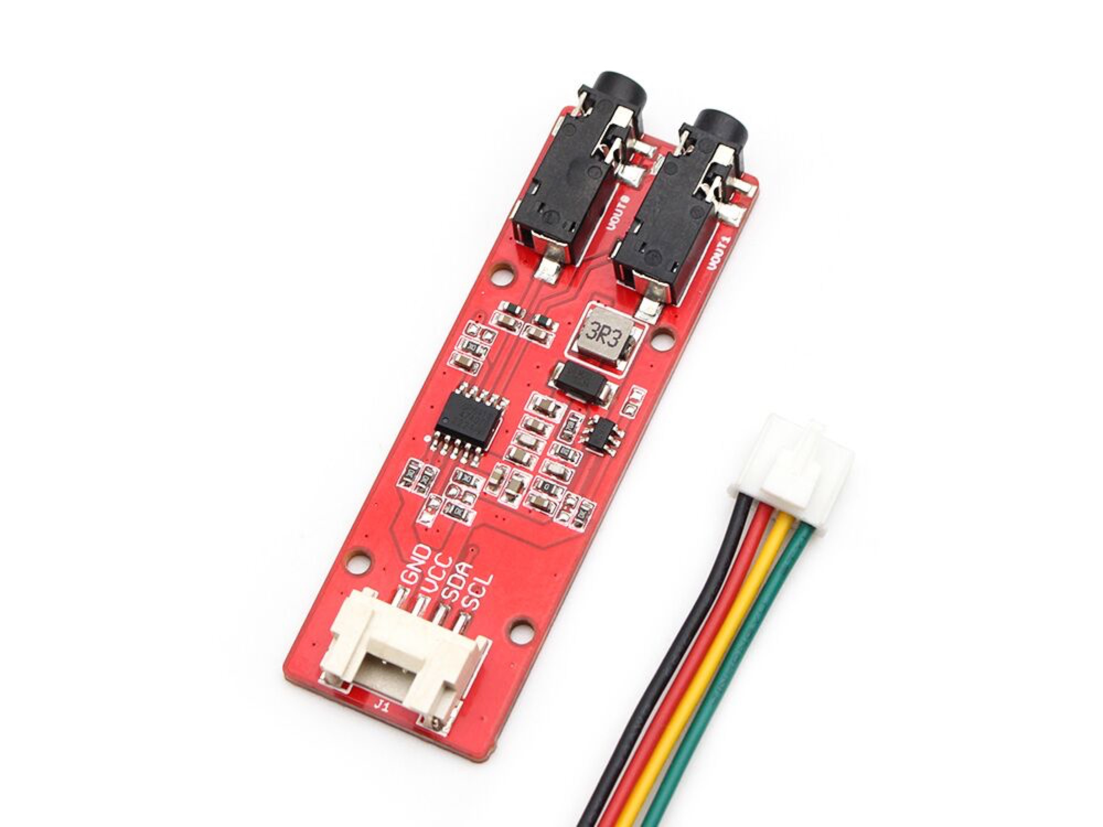
Docs/Amyboard/tulipcc-main/assets/img/mabee-dac.jpg
