aTanguay/Enssemble.io/Docs/Amyboard/tulipcc-main/assets/img/tulip-shop-1.jpg

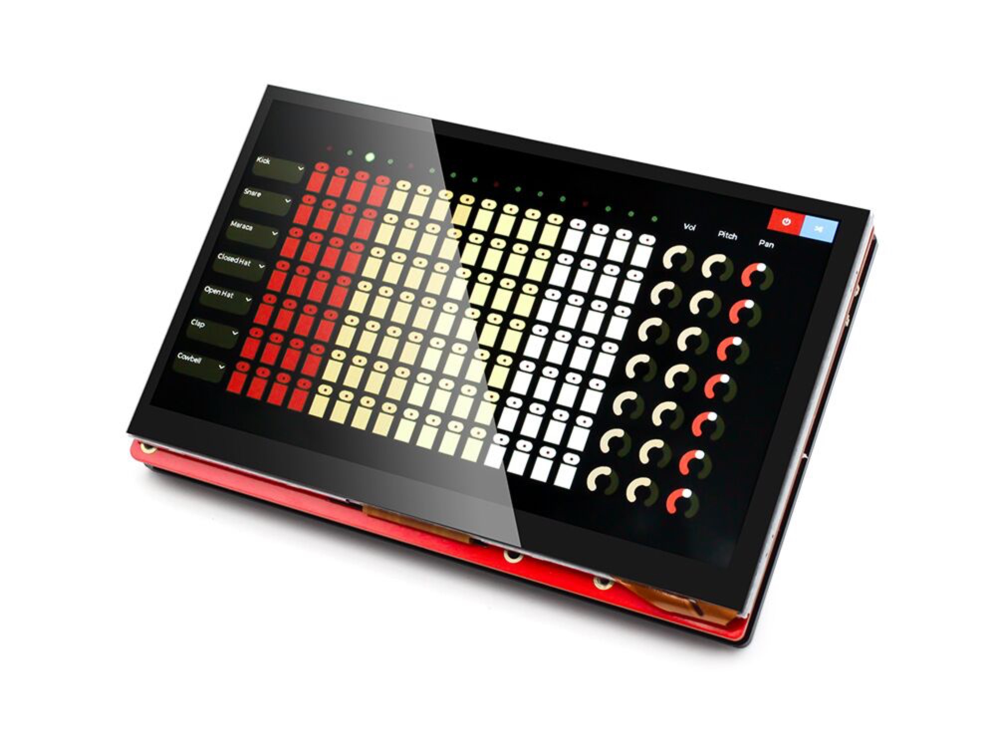
Docs/Amyboard/tulipcc-main/assets/img/tulip-shop-1.jpg
