aTanguay/Enssemble.io/Docs/Amyboard/tulipcc-main/assets/img/tulip-shop-2.jpg

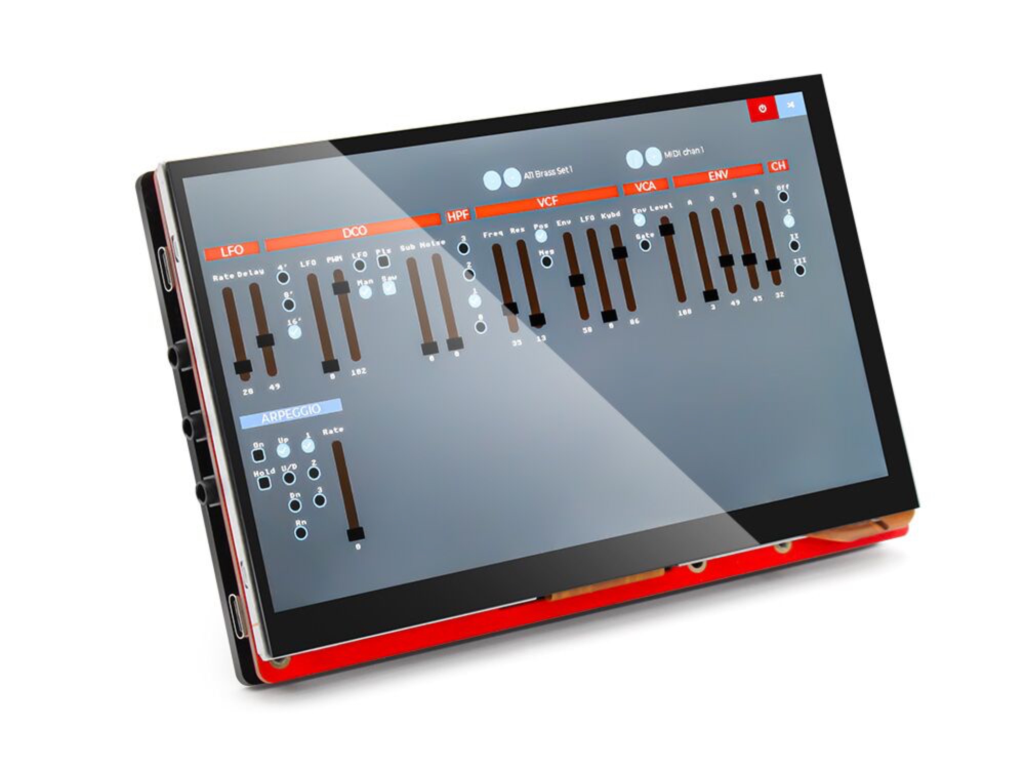
Docs/Amyboard/tulipcc-main/assets/img/tulip-shop-2.jpg
