aTanguay/Enssemble.io/Docs/Amyboard/tulipcc-main/assets/img/tulip-shop-3.jpg

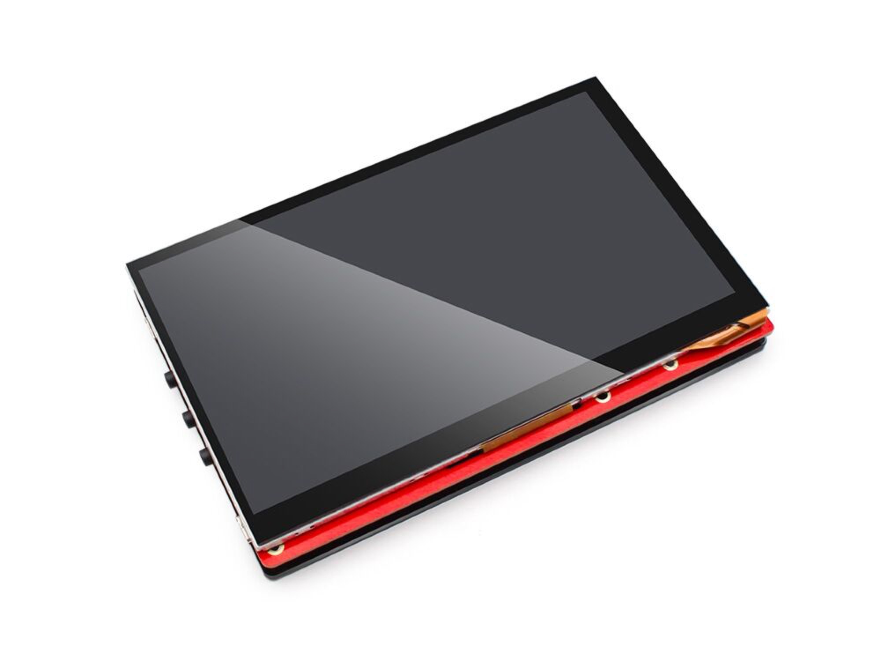
Docs/Amyboard/tulipcc-main/assets/img/tulip-shop-3.jpg
