aTanguay/Enssemble.io/Docs/Amyboard/tulipcc-main/assets/img/tulip-shop-4.jpg

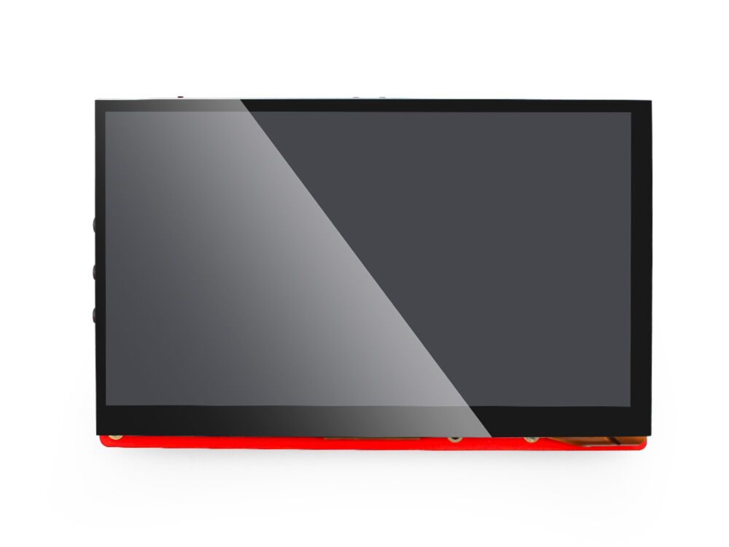
Docs/Amyboard/tulipcc-main/assets/img/tulip-shop-4.jpg
