aTanguay/Enssemble.io/Docs/Amyboard/tulipcc-main/assets/img/tulip-shop-5.jpg

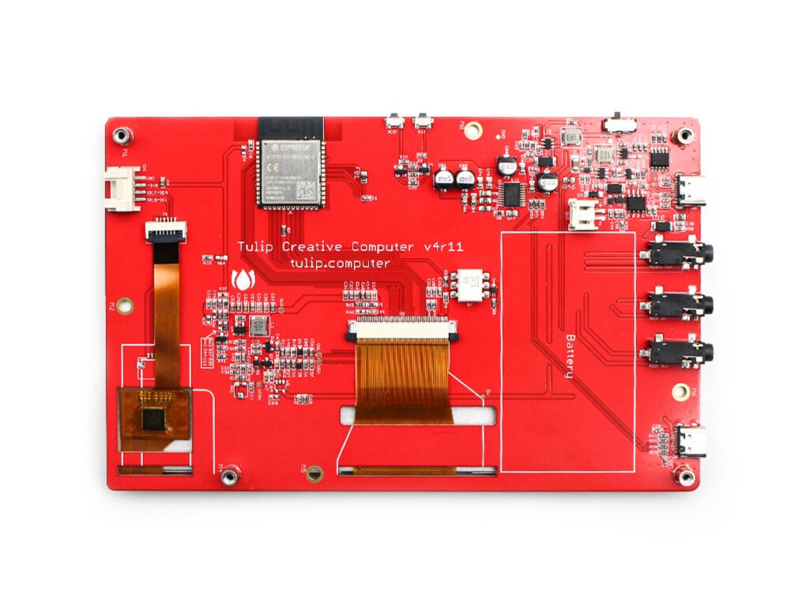
Docs/Amyboard/tulipcc-main/assets/img/tulip-shop-5.jpg
