aTanguay/Enssemble.io/Docs/Amyboard/tulipcc-main/assets/img/tulip-shop-6.jpg

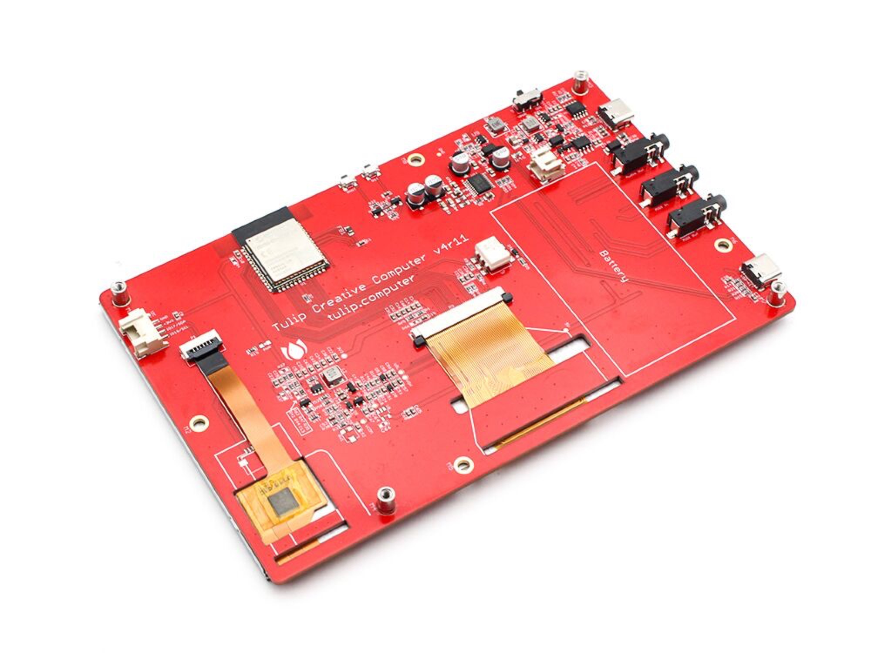
Docs/Amyboard/tulipcc-main/assets/img/tulip-shop-6.jpg
