aTanguay/Enssemble.io/Docs/Amyboard/tulipcc-main/assets/img/tulip_amyboard.jpg

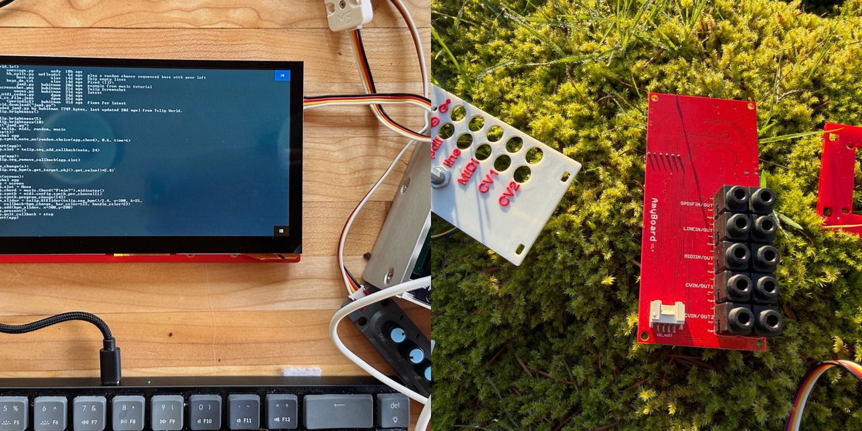
Docs/Amyboard/tulipcc-main/assets/img/tulip_amyboard.jpg
