aTanguay/Enssemble.io/Docs/Amyboard/tulipcc-main/assets/img/tulip_hero.jpg

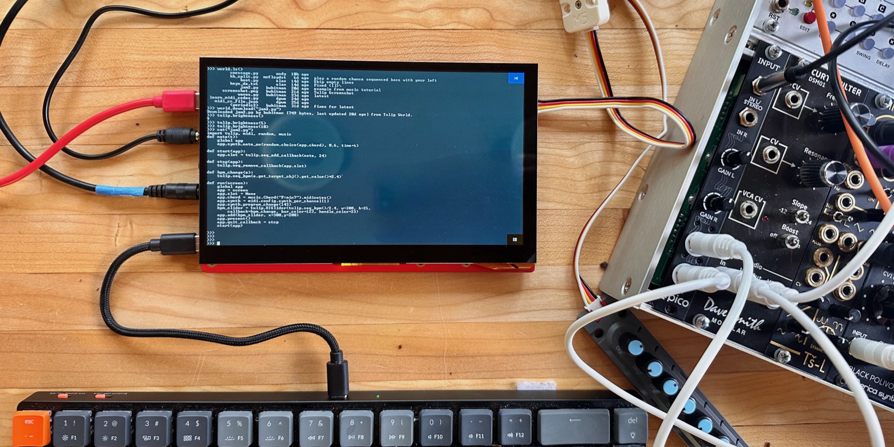
Docs/Amyboard/tulipcc-main/assets/img/tulip_hero.jpg
