aTanguay/Enssemble.io/Docs/Amyboard/tulipcc-main/assets/img/tulipcc-boards.jpeg

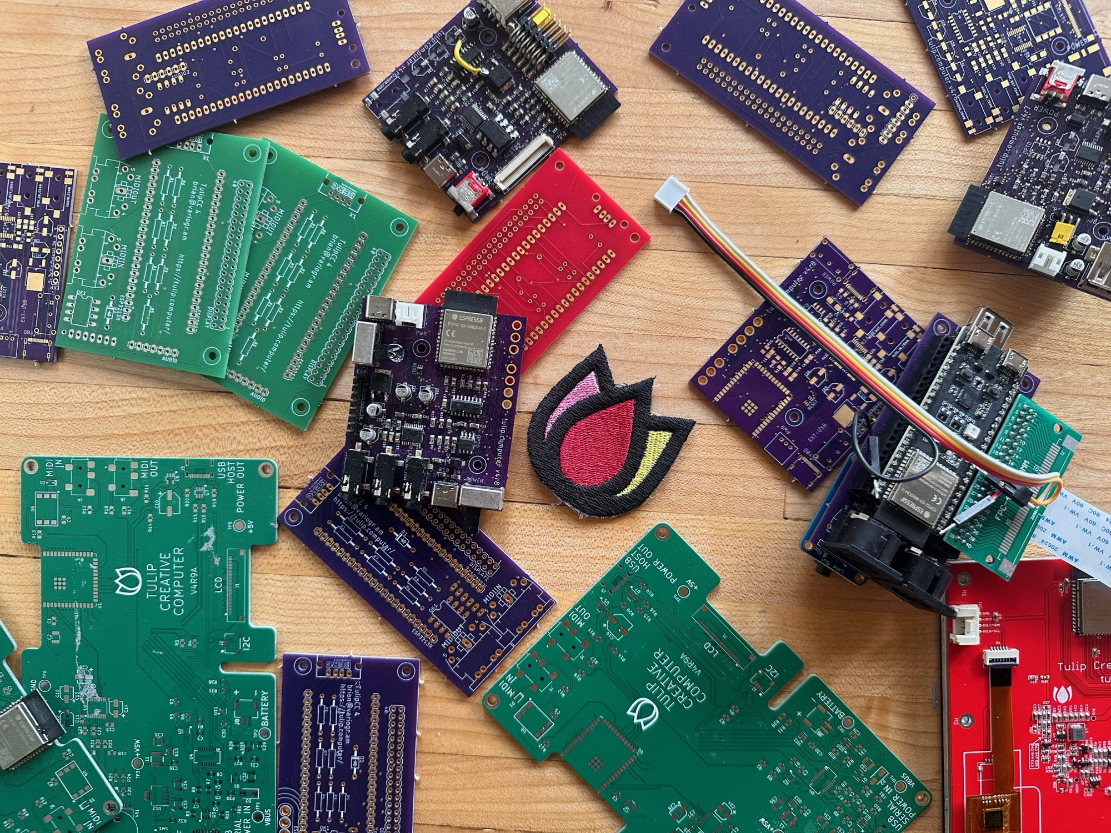
Docs/Amyboard/tulipcc-main/assets/img/tulipcc-boards.jpeg
