aTanguay/Enssemble.io/Docs/Amyboard/tulipcc-main/assets/img/tulipcc-digitakt.jpeg

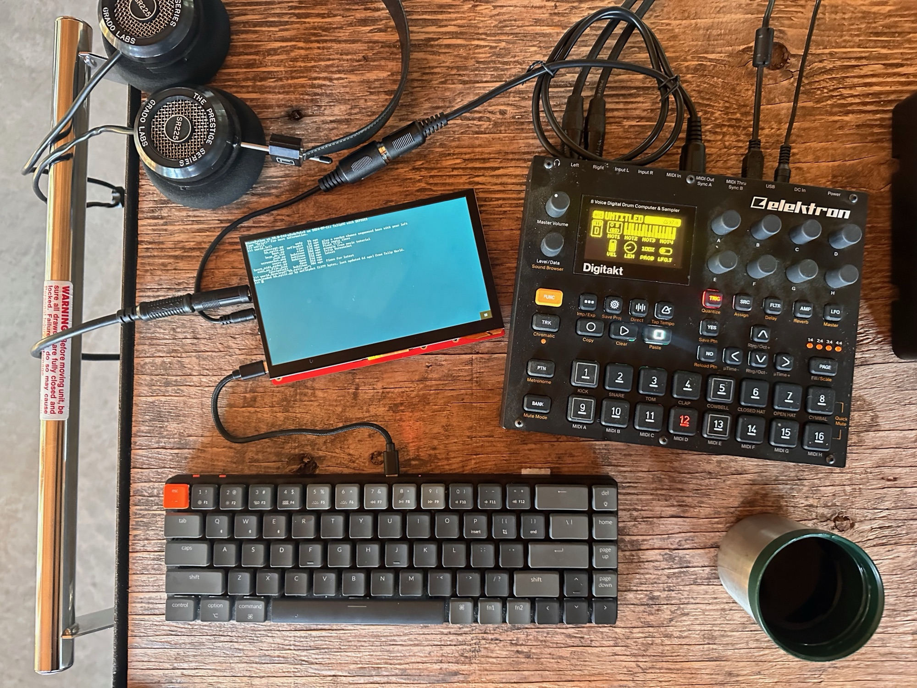
Docs/Amyboard/tulipcc-main/assets/img/tulipcc-digitakt.jpeg
