aTanguay/Enssemble.io/Docs/Amyboard/tulipcc-main/assets/img/tulipcc-editor.jpeg

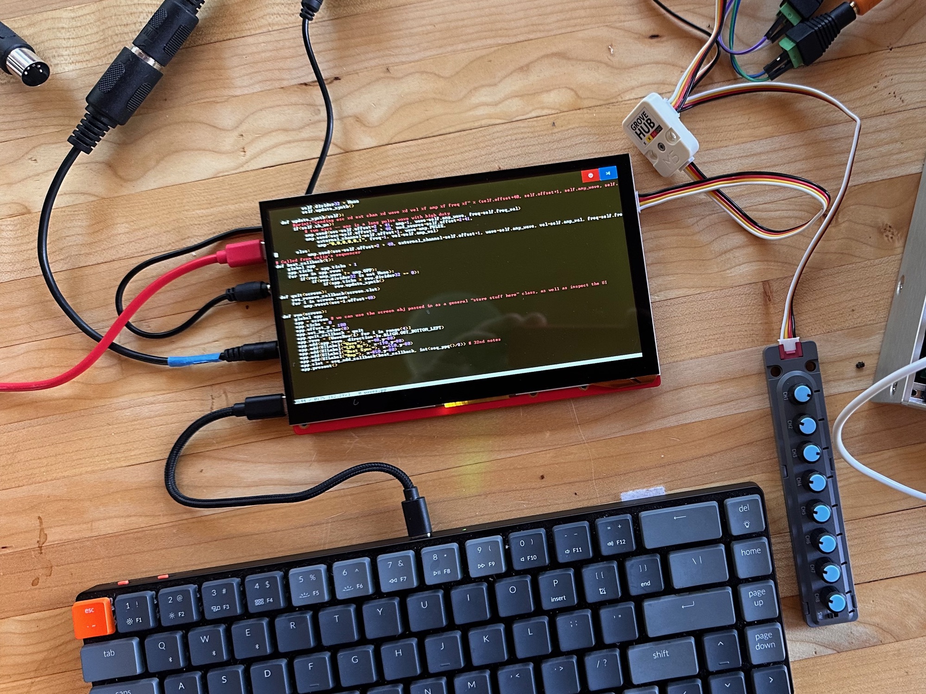
Docs/Amyboard/tulipcc-main/assets/img/tulipcc-editor.jpeg
