aTanguay/Enssemble.io/Docs/Amyboard/tulipcc-main/assets/img/tulipcc-generations.jpeg

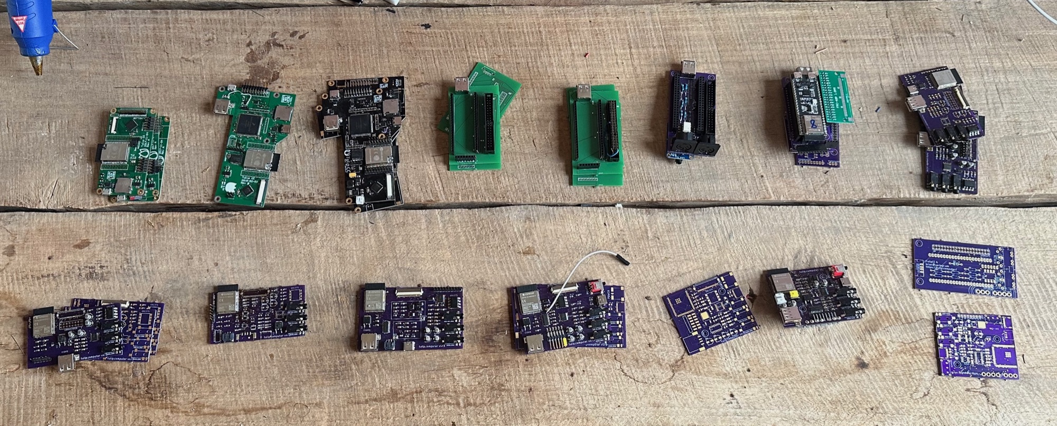
Docs/Amyboard/tulipcc-main/assets/img/tulipcc-generations.jpeg
