aTanguay/Enssemble.io/Docs/Amyboard/tulipcc-main/assets/img/tulipcc-repl.jpeg

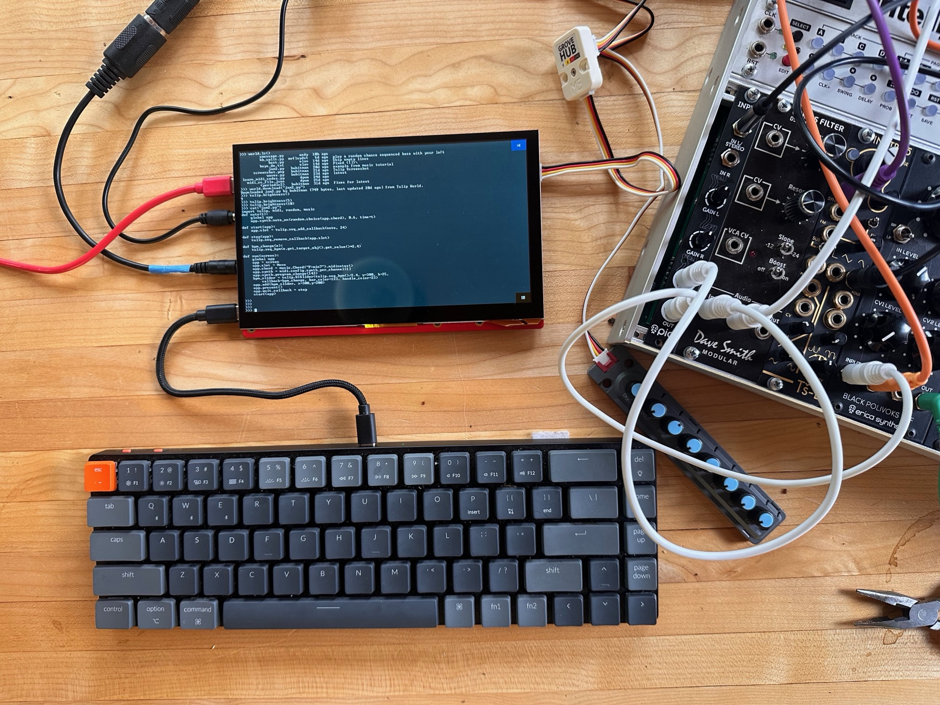
Docs/Amyboard/tulipcc-main/assets/img/tulipcc-repl.jpeg
