aTanguay/Enssemble.io/Docs/Amyboard/tulipcc-main/assets/img/tulipcc-voices.jpeg

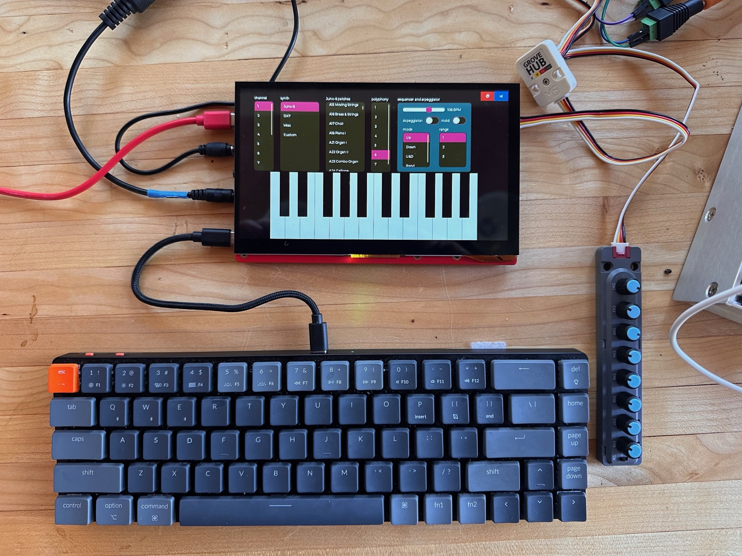
Docs/Amyboard/tulipcc-main/assets/img/tulipcc-voices.jpeg
