aTanguay/Enssemble.io/Docs/Amyboard/tulipcc-main/assets/img/tulipcc-writing.jpeg

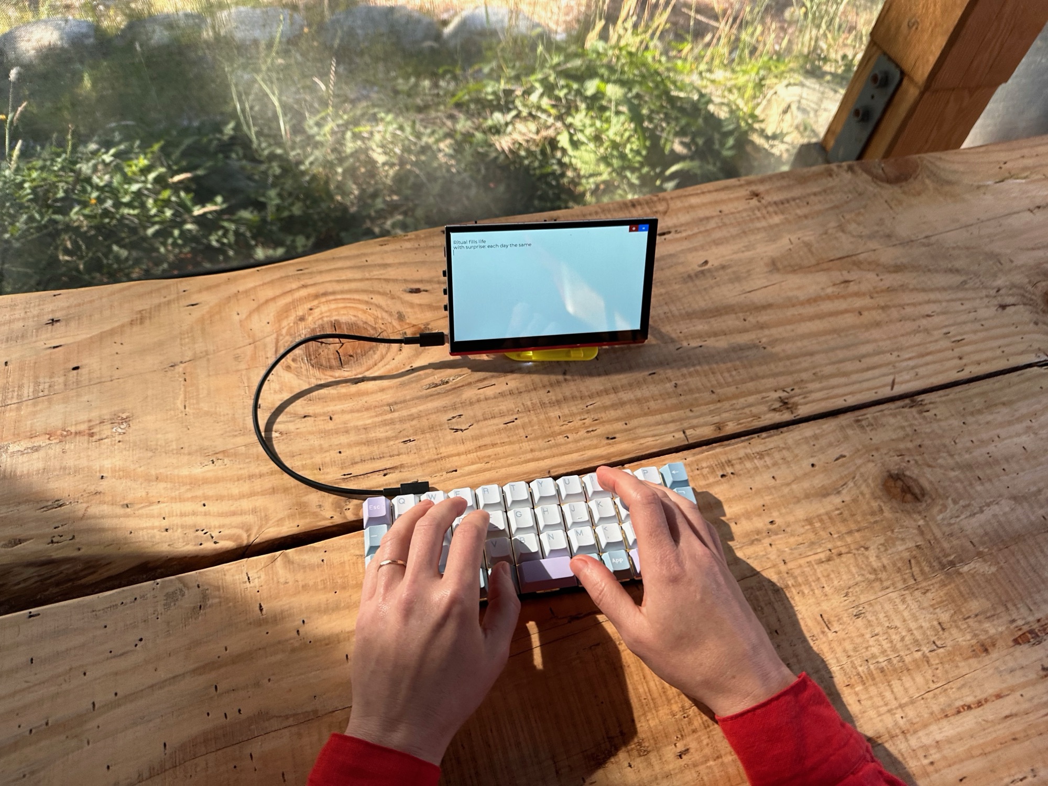
Docs/Amyboard/tulipcc-main/assets/img/tulipcc-writing.jpeg
