aTanguay/Enssemble.io/Docs/Amyboard/tulipcc-main/assets/img/two_amyboards.jpg

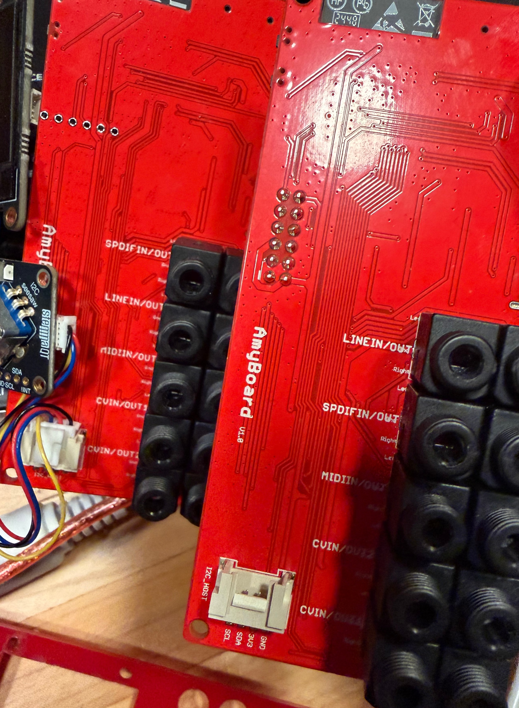
Docs/Amyboard/tulipcc-main/assets/img/two_amyboards.jpg
