aTanguay/Enssemble.io/Docs/Amyboard/tulipcc-main/docs/amyboard/img/accessory_adafruit_oled.jpg

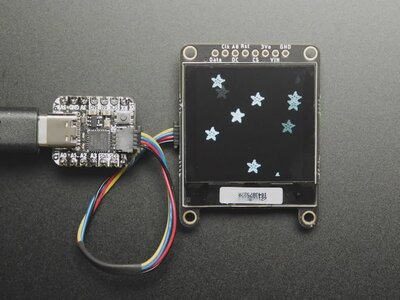
Docs/Amyboard/tulipcc-main/docs/amyboard/img/accessory_adafruit_oled.jpg
