aTanguay/Enssemble.io/Docs/Amyboard/tulipcc-main/docs/amyboard/img/accessory_m5_8angle.jpg

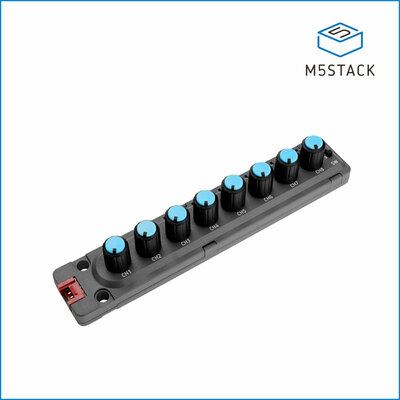
Docs/Amyboard/tulipcc-main/docs/amyboard/img/accessory_m5_8angle.jpg
