aTanguay/Enssemble.io/Docs/Amyboard/tulipcc-main/docs/amyboard/img/accessory_m5_dac.jpg

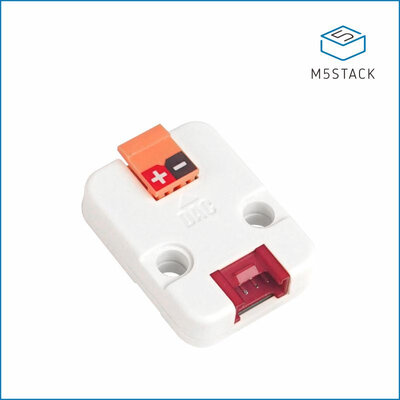
Docs/Amyboard/tulipcc-main/docs/amyboard/img/accessory_m5_dac.jpg
