aTanguay/Enssemble.io/Docs/Amyboard/tulipcc-main/docs/amyboard/img/accessory_m5_extend.jpg

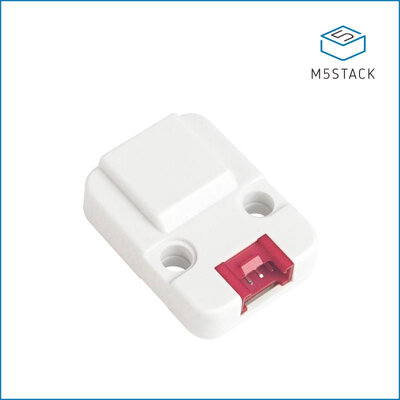
Docs/Amyboard/tulipcc-main/docs/amyboard/img/accessory_m5_extend.jpg
