aTanguay/Enssemble.io/Docs/Amyboard/tulipcc-main/docs/amyboard/img/accessory_mabee_dac.jpg

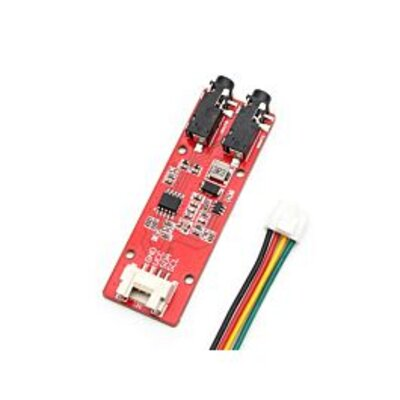
Docs/Amyboard/tulipcc-main/docs/amyboard/img/accessory_mabee_dac.jpg
