aTanguay/Enssemble.io/Docs/Amyboard/tulipcc-main/docs/amyboard/img/amyboard_world_environments.png

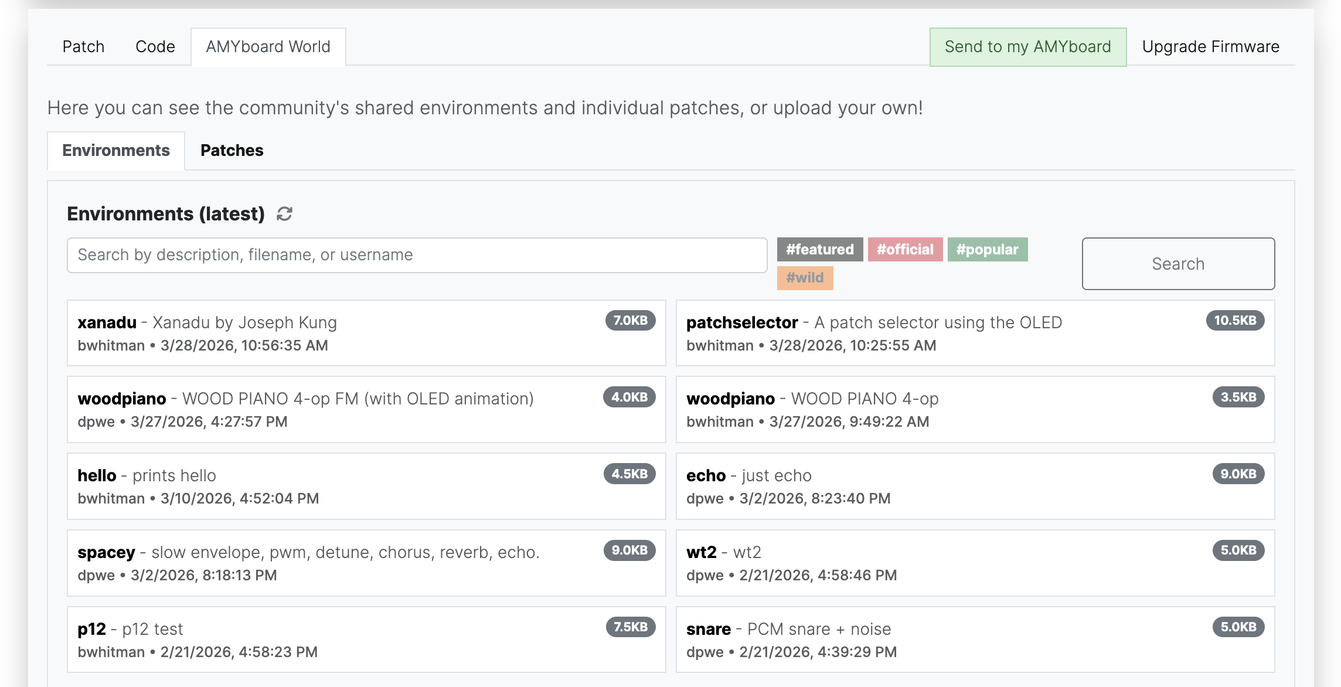
Docs/Amyboard/tulipcc-main/docs/amyboard/img/amyboard_world_environments.png
