aTanguay/Enssemble.io/Docs/Amyboard/tulipcc-main/docs/amyboard/img/amyboard_world_patches.png

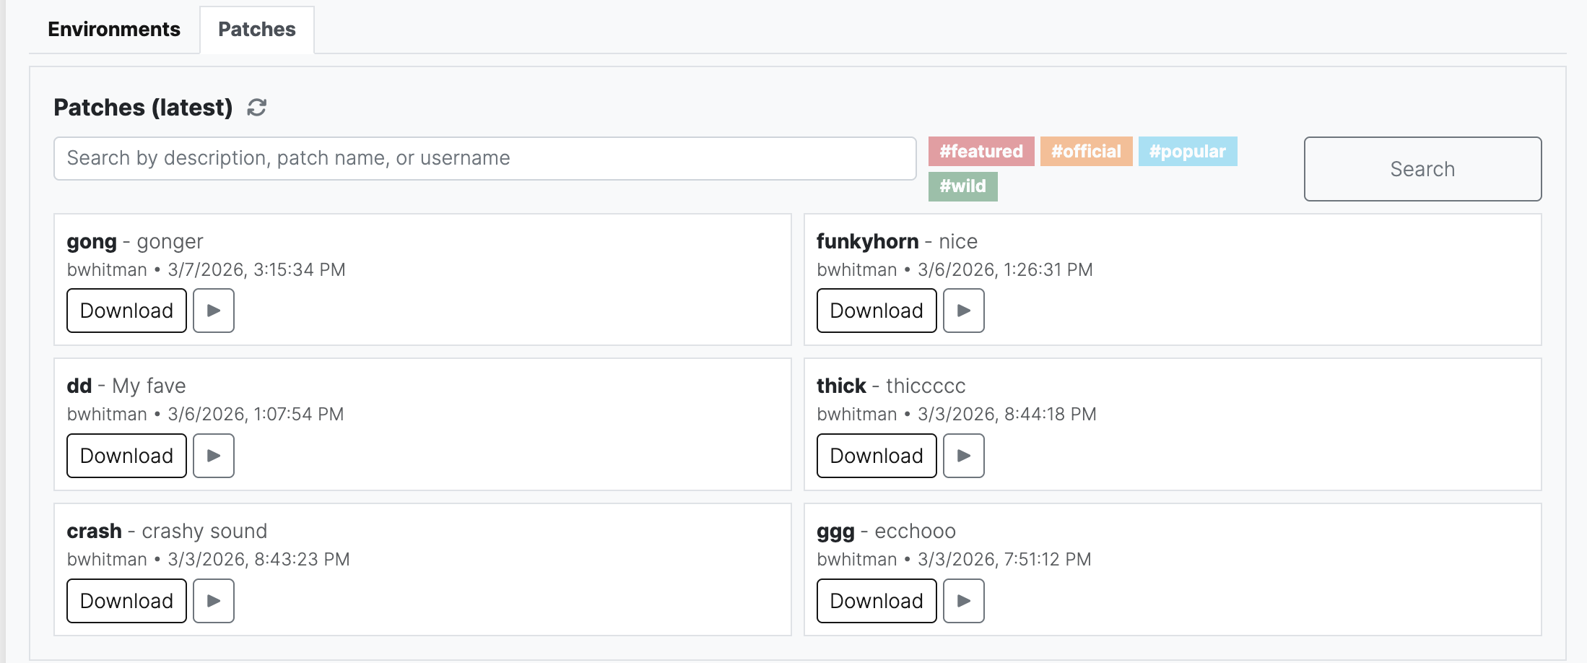
Docs/Amyboard/tulipcc-main/docs/amyboard/img/amyboard_world_patches.png
