aTanguay/Enssemble.io/Docs/Amyboard/tulipcc-main/docs/amyboard/img/choose_serial_port.png

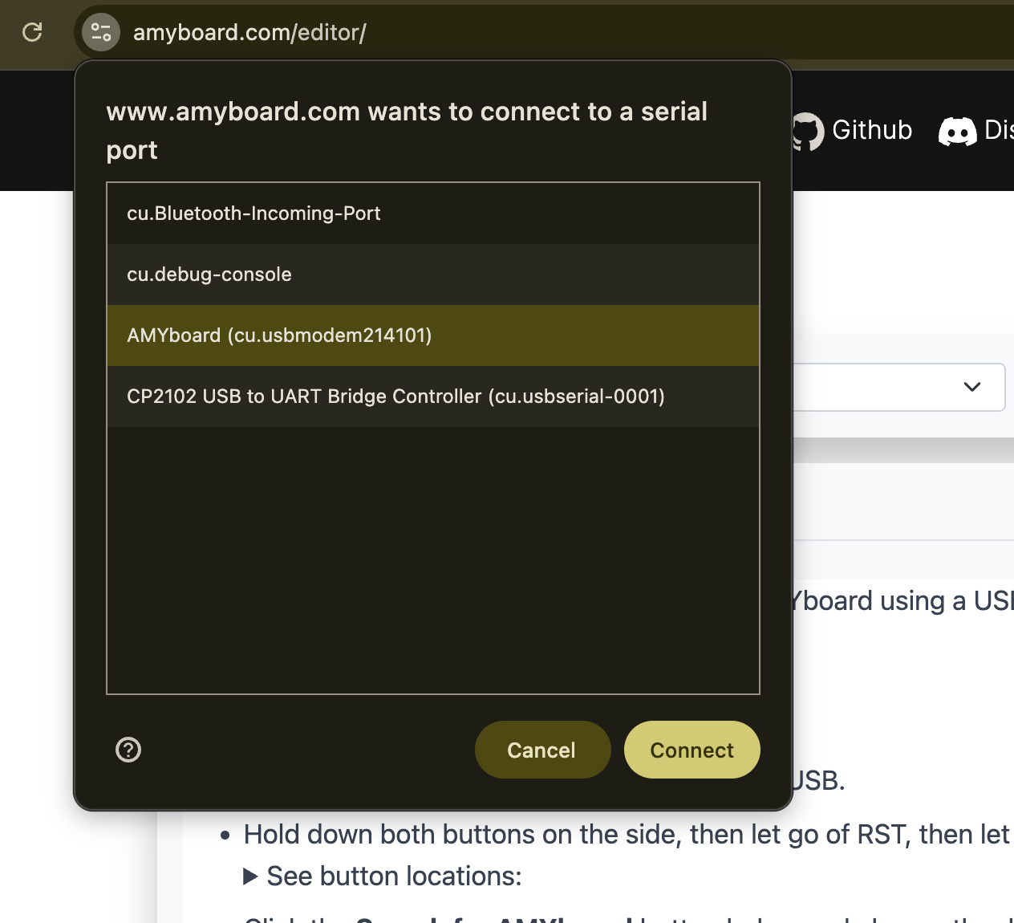
Docs/Amyboard/tulipcc-main/docs/amyboard/img/choose_serial_port.png
