aTanguay/Enssemble.io/Docs/Amyboard/tulipcc-main/docs/amyboard/img/code.png

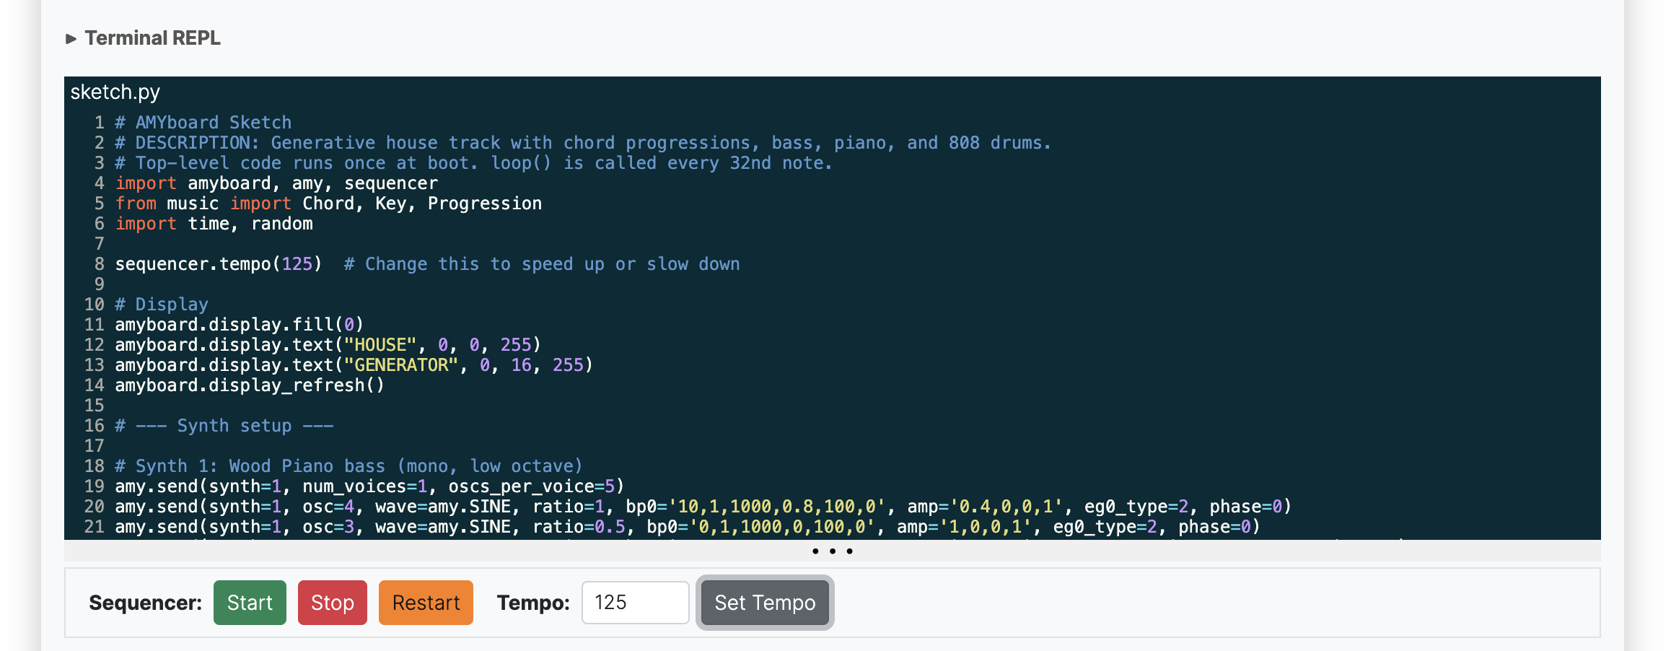
Docs/Amyboard/tulipcc-main/docs/amyboard/img/code.png
