aTanguay/Enssemble.io/Docs/Amyboard/tulipcc-main/docs/amyboard/img/code_editor.png

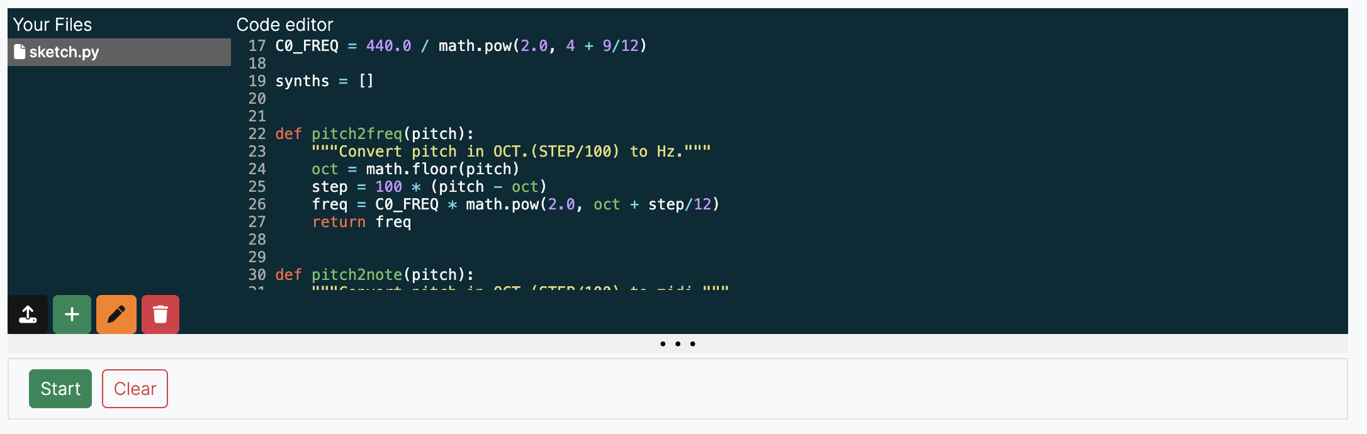
Docs/Amyboard/tulipcc-main/docs/amyboard/img/code_editor.png
