aTanguay/Enssemble.io/Docs/Amyboard/tulipcc-main/docs/amyboard/img/control.png

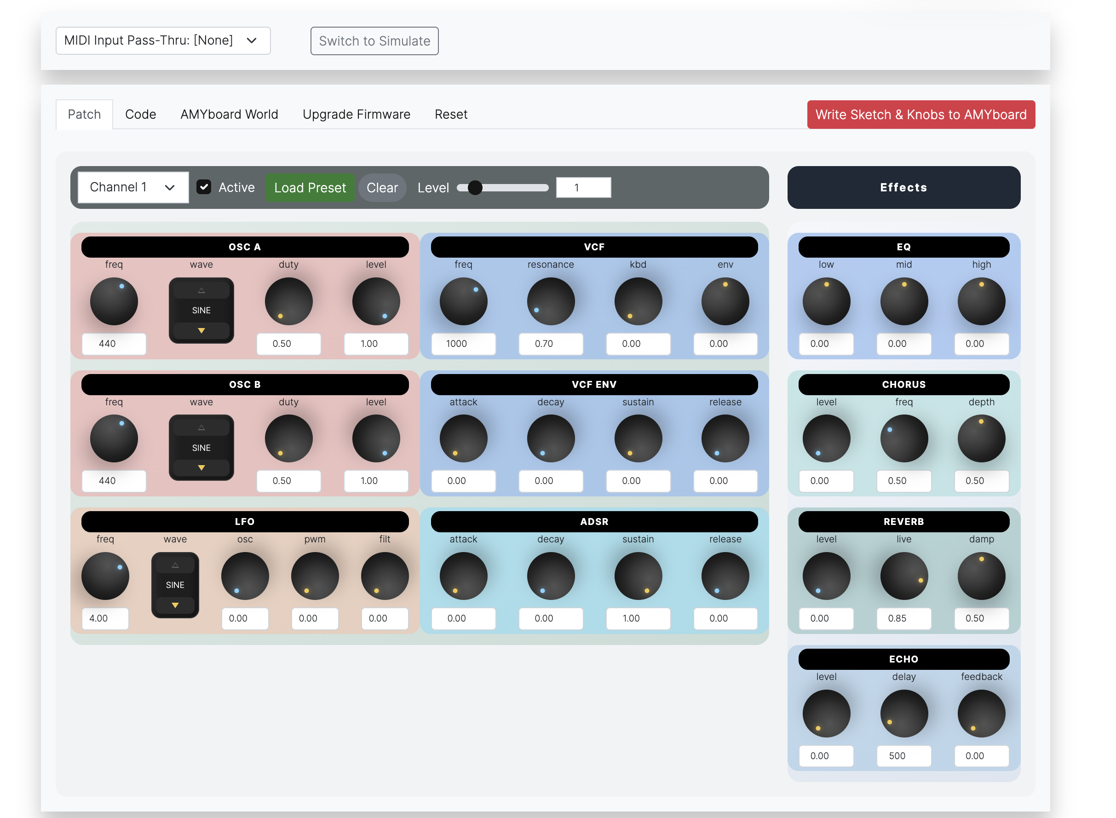
Docs/Amyboard/tulipcc-main/docs/amyboard/img/control.png
