aTanguay/Enssemble.io/Docs/Amyboard/tulipcc-main/docs/amyboard/img/control_top.png

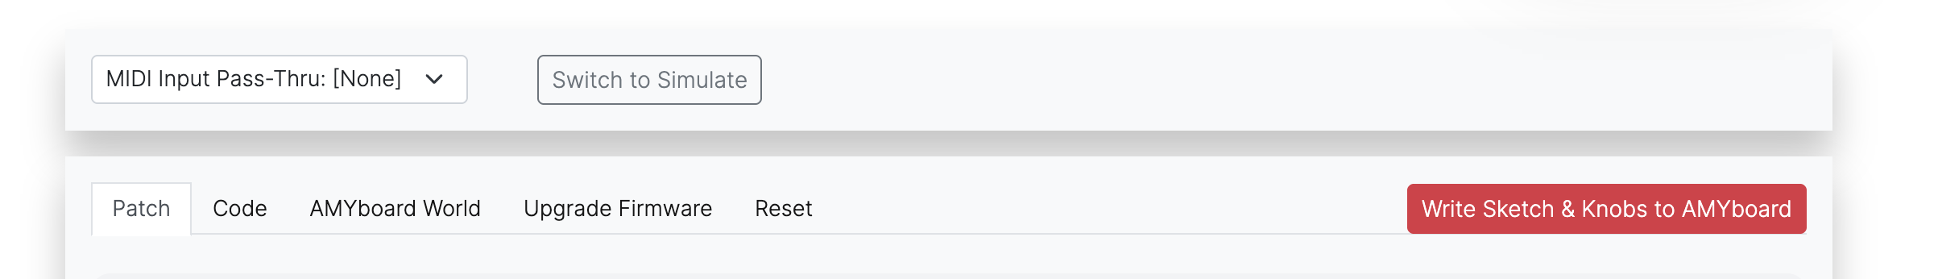
Docs/Amyboard/tulipcc-main/docs/amyboard/img/control_top.png
