aTanguay/Enssemble.io/Docs/Amyboard/tulipcc-main/docs/amyboard/img/knob_modal.png

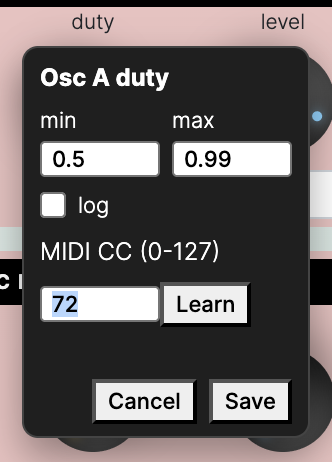
Docs/Amyboard/tulipcc-main/docs/amyboard/img/knob_modal.png
