aTanguay/Enssemble.io/Docs/Amyboard/tulipcc-main/docs/amyboard/img/oled_rotary_cv.png

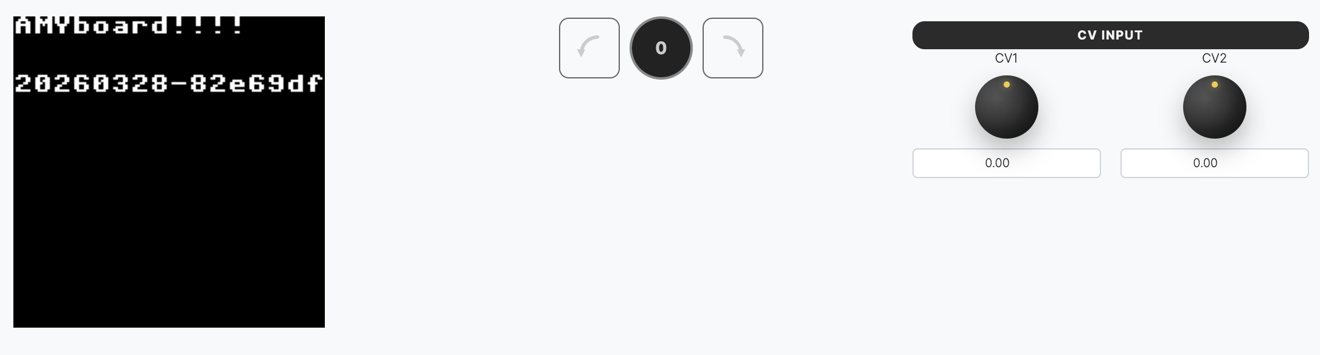
Docs/Amyboard/tulipcc-main/docs/amyboard/img/oled_rotary_cv.png
