aTanguay/Enssemble.io/Docs/Amyboard/tulipcc-main/docs/amyboard/img/patch_knobs.png

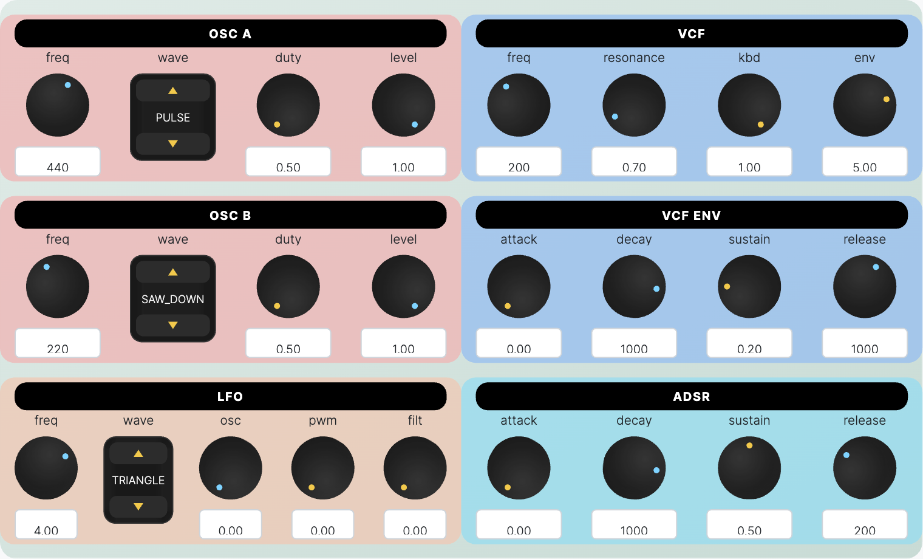
Docs/Amyboard/tulipcc-main/docs/amyboard/img/patch_knobs.png
