aTanguay/Enssemble.io/Docs/Amyboard/tulipcc-main/docs/amyboard/img/presets.png

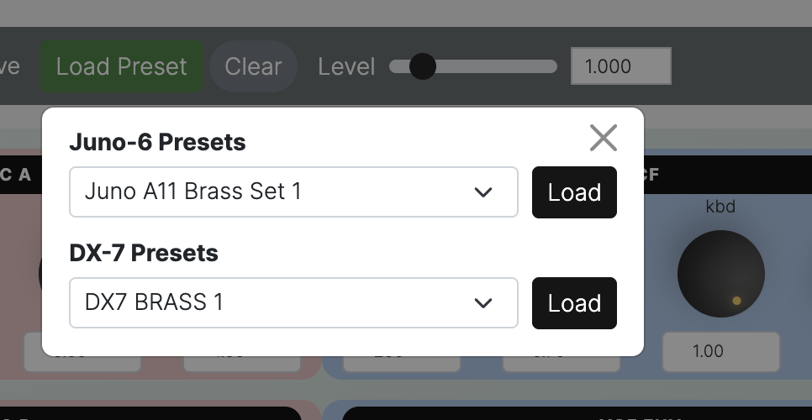
Docs/Amyboard/tulipcc-main/docs/amyboard/img/presets.png
