aTanguay/Enssemble.io/Docs/Amyboard/tulipcc-main/docs/amyboard/img/pulling.png

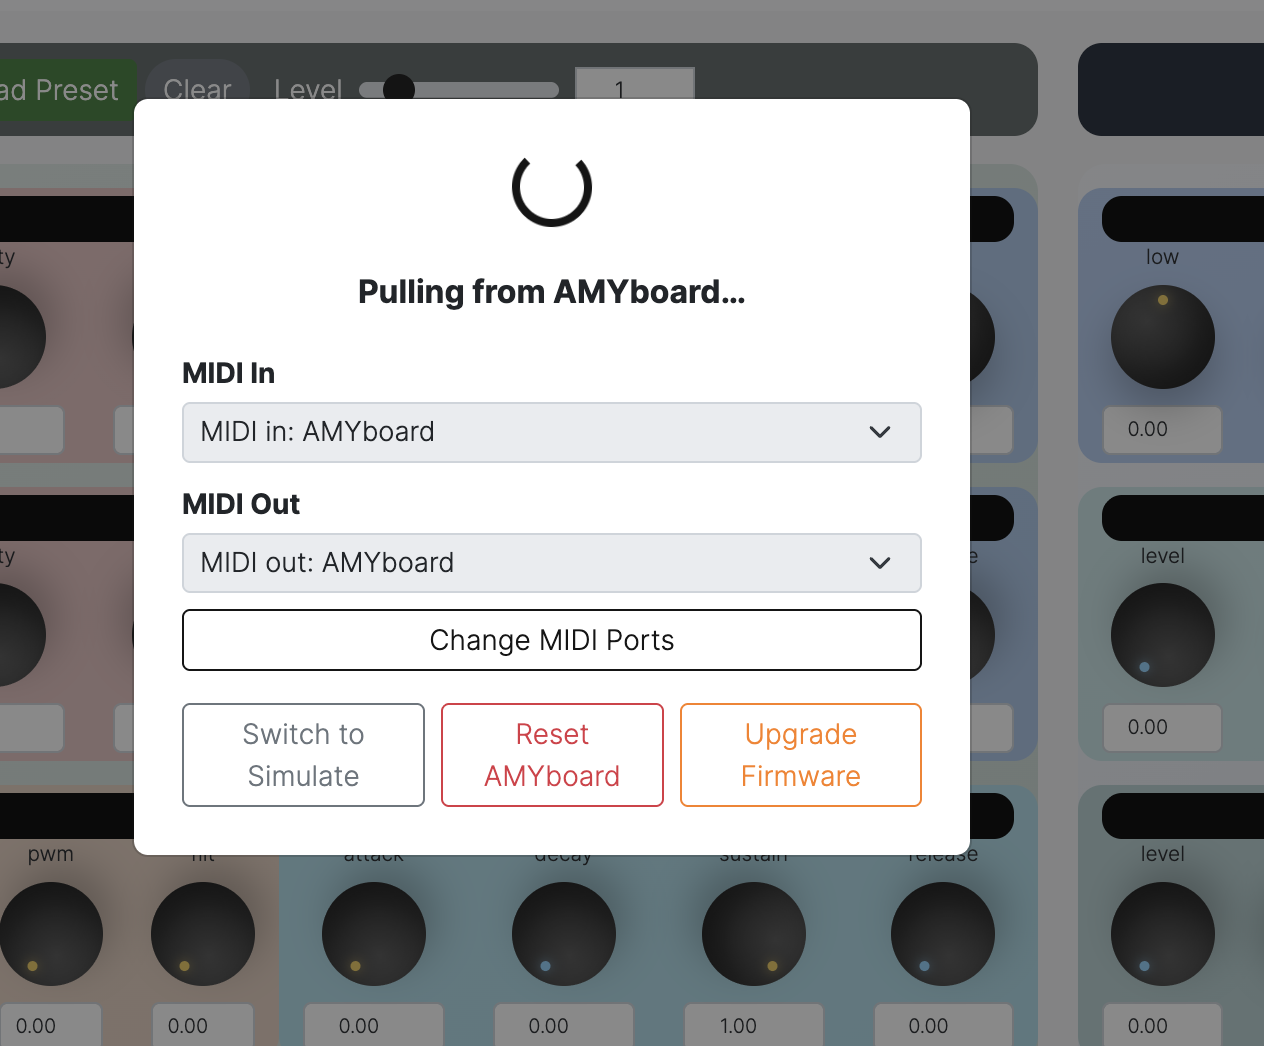
Docs/Amyboard/tulipcc-main/docs/amyboard/img/pulling.png
