aTanguay/Enssemble.io/Docs/Amyboard/tulipcc-main/docs/amyboard/img/reset.png

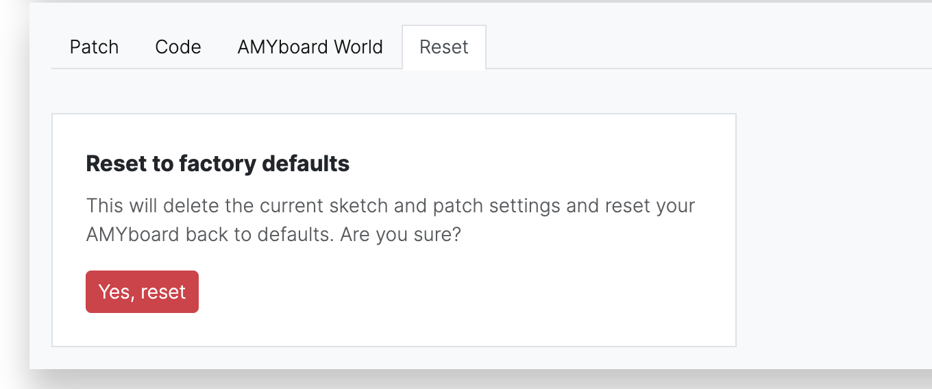
Docs/Amyboard/tulipcc-main/docs/amyboard/img/reset.png
