aTanguay/Enssemble.io/Docs/Amyboard/tulipcc-main/docs/amyboard/img/send_to_amyboard.png

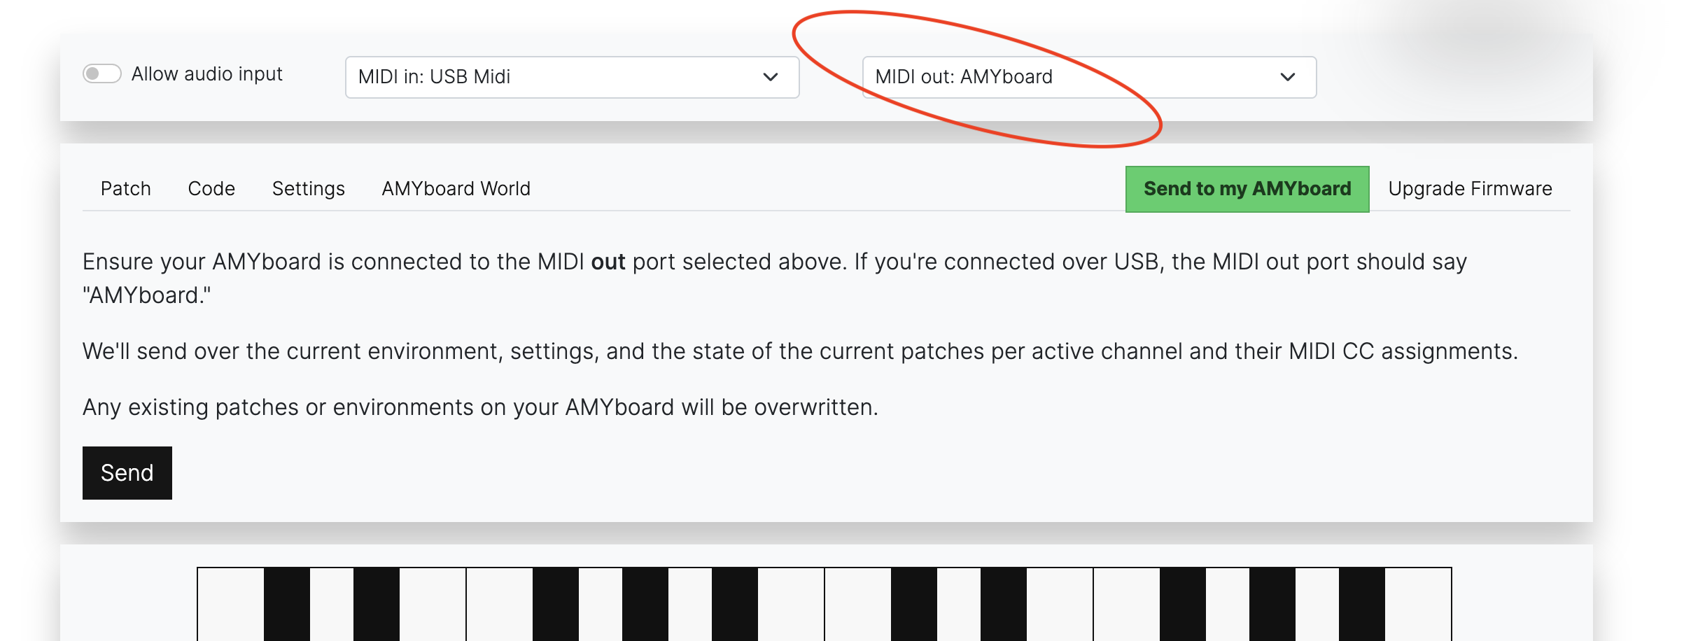
Docs/Amyboard/tulipcc-main/docs/amyboard/img/send_to_amyboard.png
