aTanguay/Enssemble.io/Docs/Amyboard/tulipcc-main/docs/amyboard/img/serial_ports.png

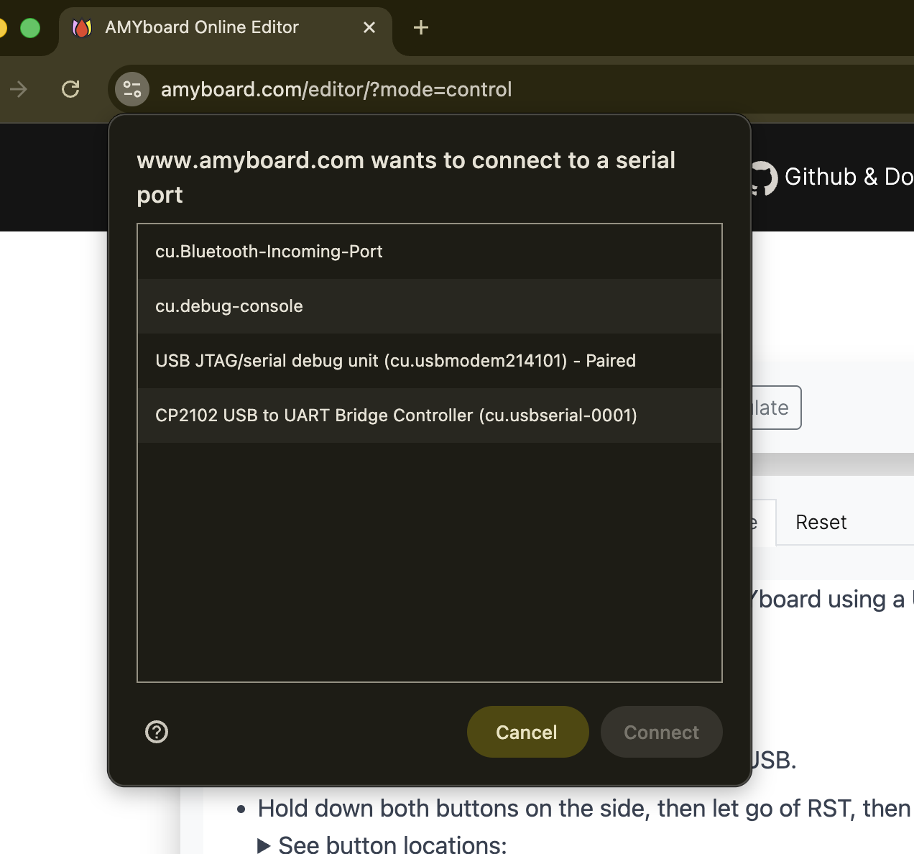
Docs/Amyboard/tulipcc-main/docs/amyboard/img/serial_ports.png
