aTanguay/Enssemble.io/Docs/Amyboard/tulipcc-main/docs/amyboard/img/sketch.png

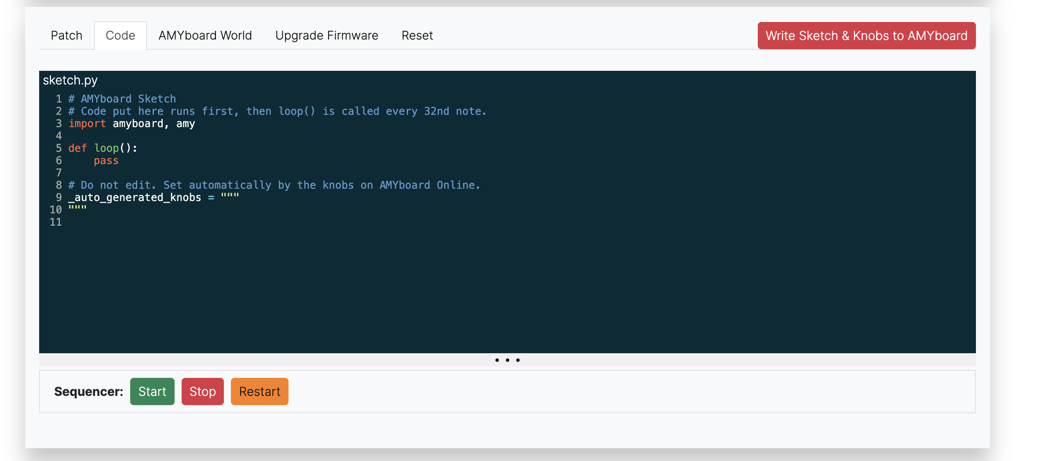
Docs/Amyboard/tulipcc-main/docs/amyboard/img/sketch.png
