aTanguay/Enssemble.io/Docs/Amyboard/tulipcc-main/docs/amyboard/img/synth_knobs.png

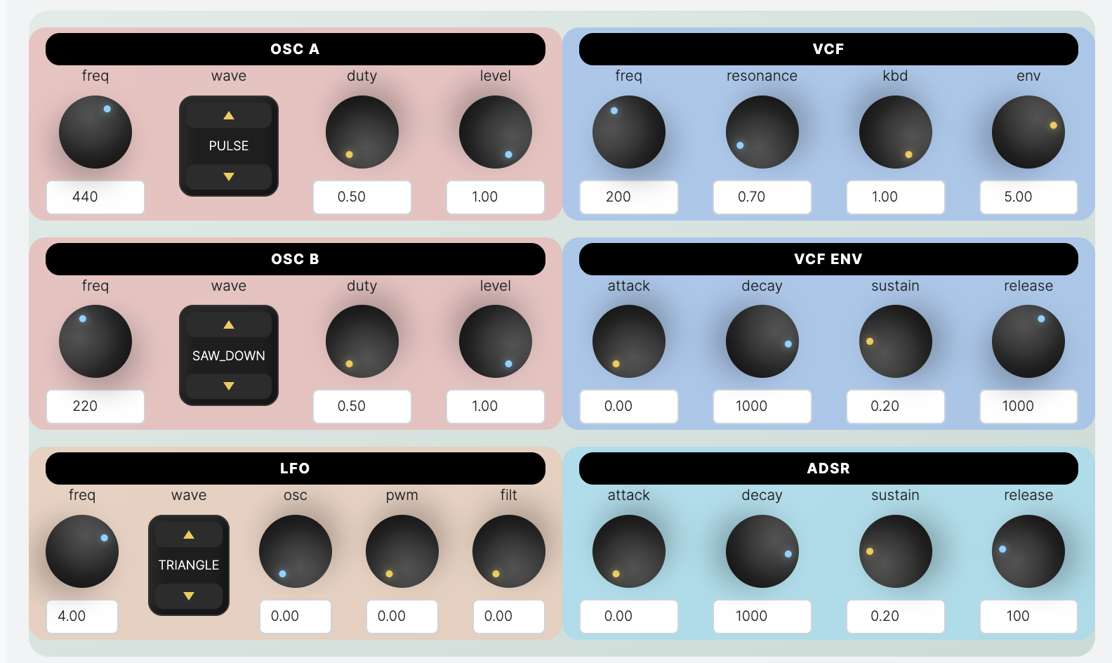
Docs/Amyboard/tulipcc-main/docs/amyboard/img/synth_knobs.png
