aTanguay/Enssemble.io/Docs/Amyboard/tulipcc-main/docs/amyboard/img/terminal_repl.png

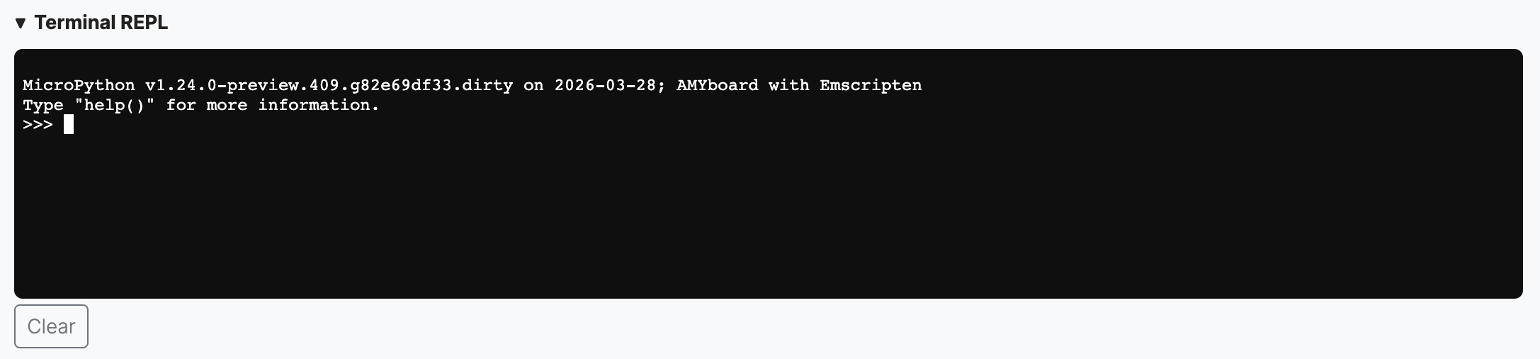
Docs/Amyboard/tulipcc-main/docs/amyboard/img/terminal_repl.png
