aTanguay/Enssemble.io/Docs/Amyboard/tulipcc-main/docs/amyboard/img/upgrade_firmware.png

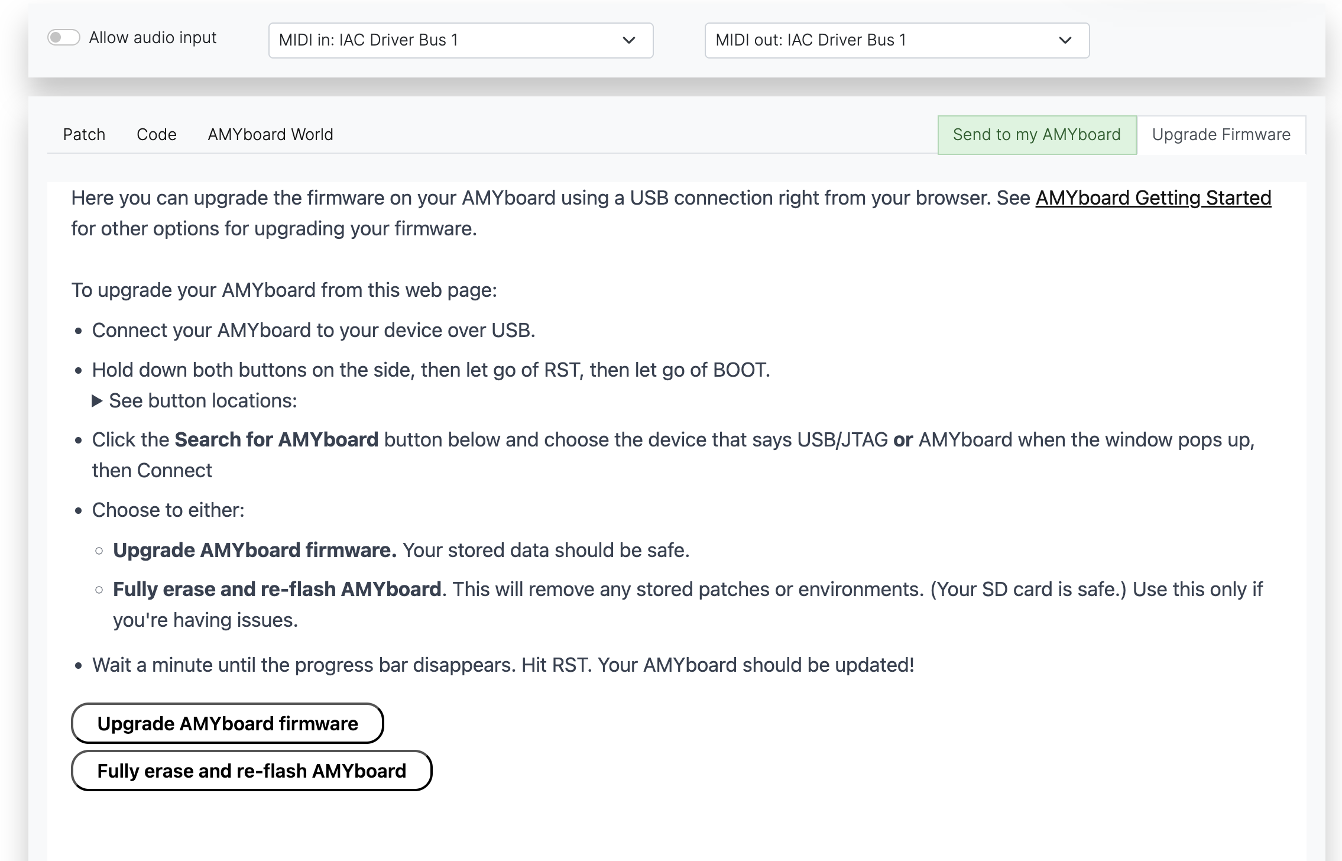
Docs/Amyboard/tulipcc-main/docs/amyboard/img/upgrade_firmware.png
