aTanguay/Enssemble.io/Docs/Amyboard/tulipcc-main/docs/amyboard/img/wavetable_presets.png

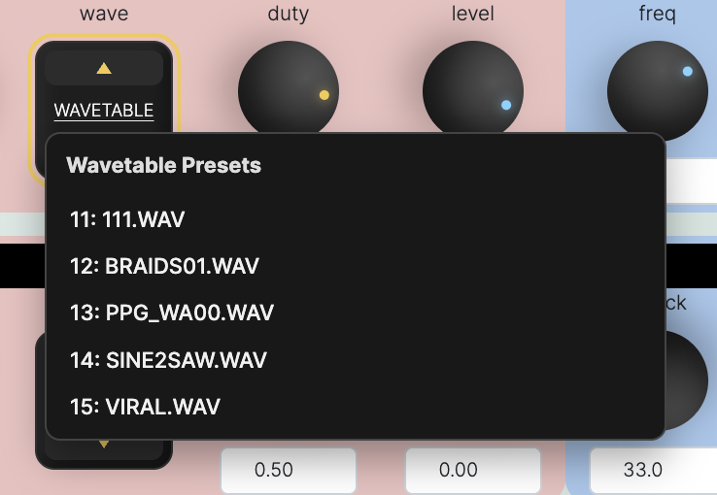
Docs/Amyboard/tulipcc-main/docs/amyboard/img/wavetable_presets.png
