aTanguay/Enssemble.io/Docs/Amyboard/tulipcc-main/docs/pics/board_r7.png

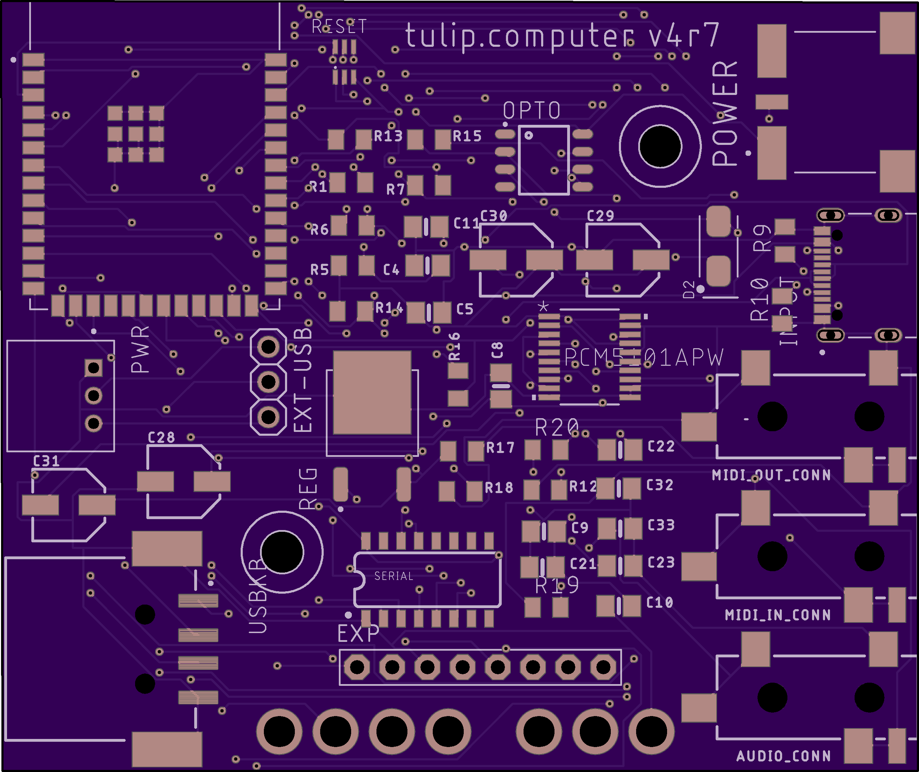
Docs/Amyboard/tulipcc-main/docs/pics/board_r7.png
