aTanguay/Enssemble.io/Docs/Amyboard/tulipcc-main/docs/pics/breadboard_close.jpg

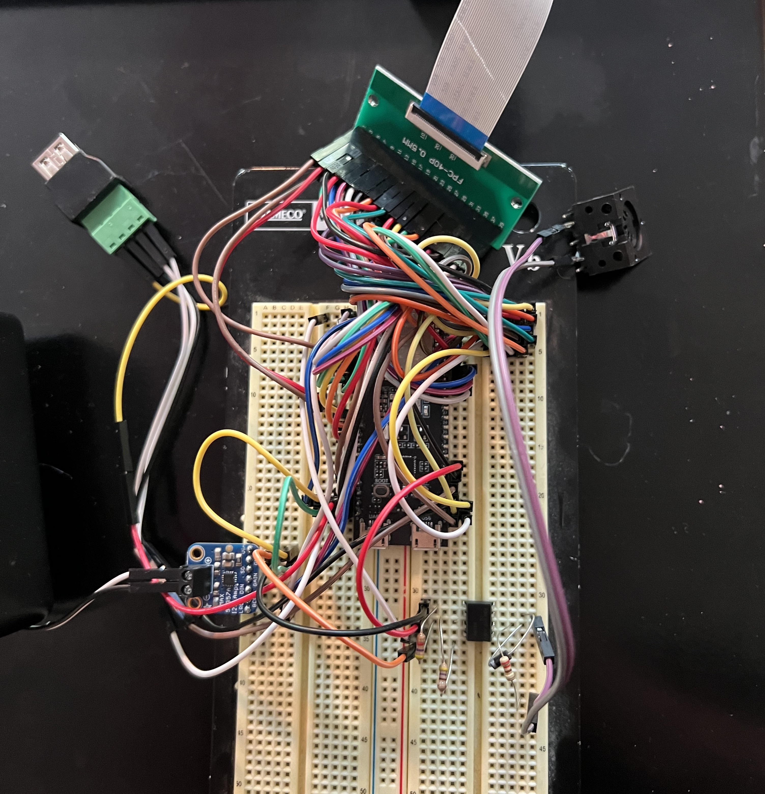
Docs/Amyboard/tulipcc-main/docs/pics/breadboard_close.jpg
