aTanguay/Enssemble.io/Docs/Amyboard/tulipcc-main/docs/pics/breadboard_display.jpg

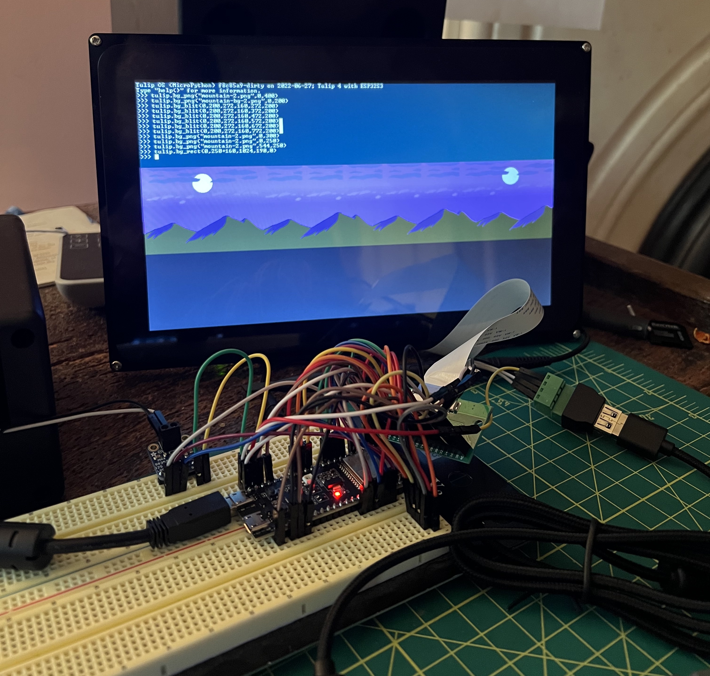
Docs/Amyboard/tulipcc-main/docs/pics/breadboard_display.jpg
