aTanguay/Enssemble.io/Docs/Amyboard/tulipcc-main/docs/pics/breakout.jpg

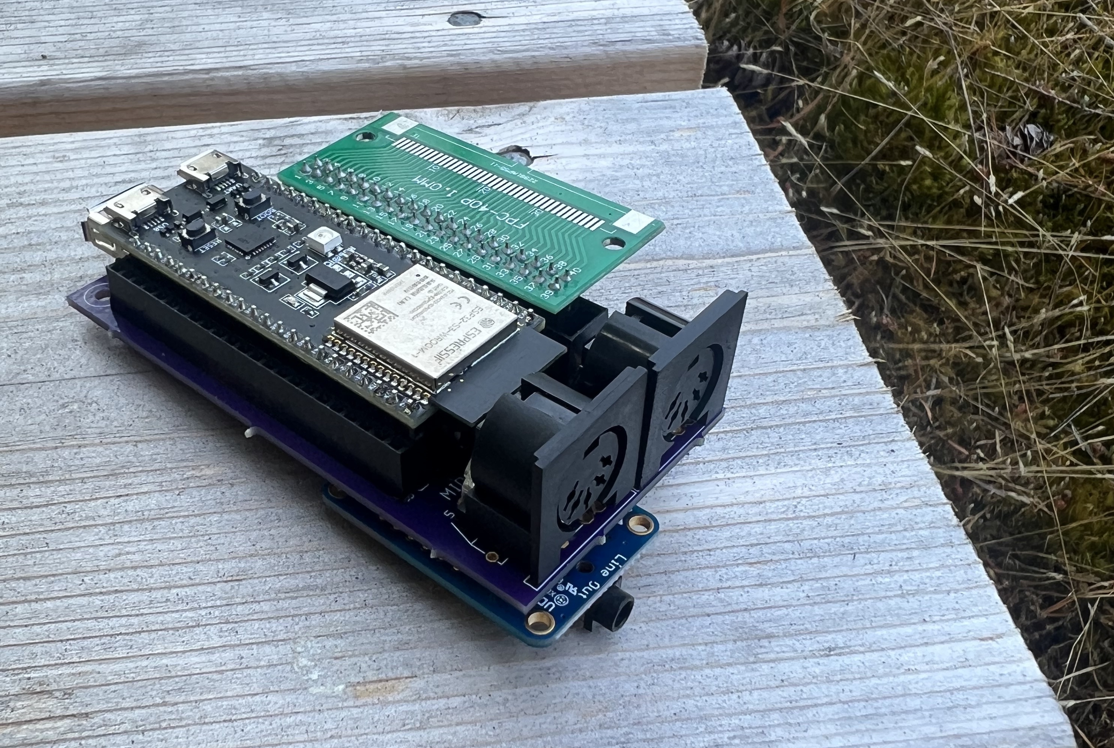
Docs/Amyboard/tulipcc-main/docs/pics/breakout.jpg
