aTanguay/Enssemble.io/Docs/Amyboard/tulipcc-main/docs/pics/breakout_bare.png

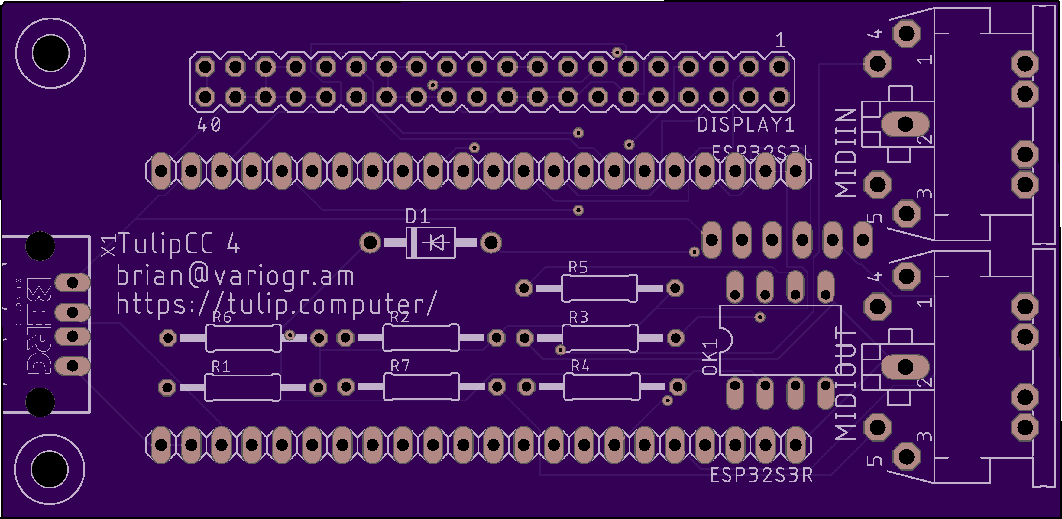
Docs/Amyboard/tulipcc-main/docs/pics/breakout_bare.png
