aTanguay/Enssemble.io/Docs/Amyboard/tulipcc-main/docs/pics/desktop.png

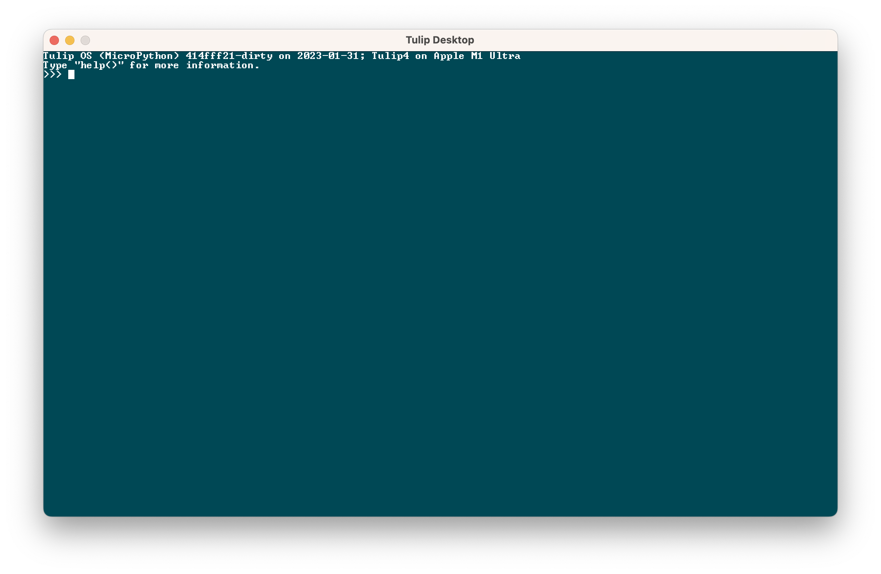
Docs/Amyboard/tulipcc-main/docs/pics/desktop.png
