aTanguay/Enssemble.io/Docs/Amyboard/tulipcc-main/docs/pics/flat_tiles.jpg

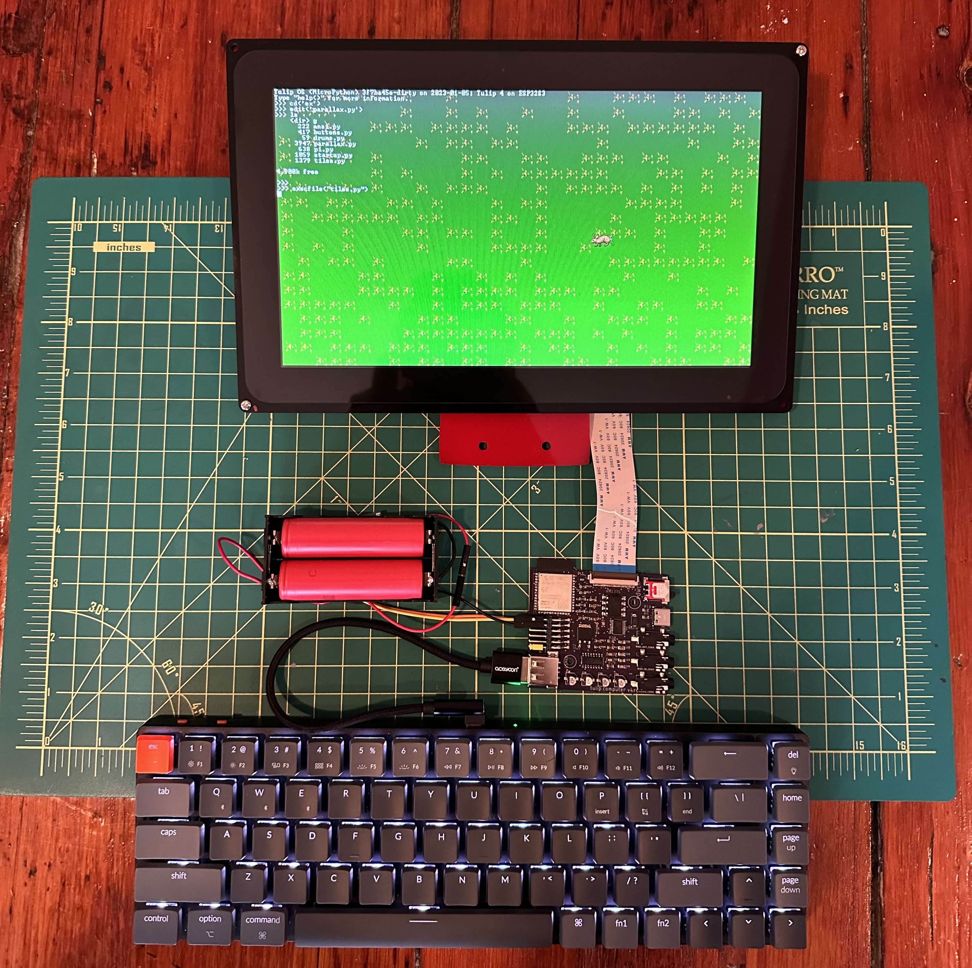
Docs/Amyboard/tulipcc-main/docs/pics/flat_tiles.jpg
