aTanguay/Enssemble.io/Docs/Amyboard/tulipcc-main/docs/pics/ios_1.png

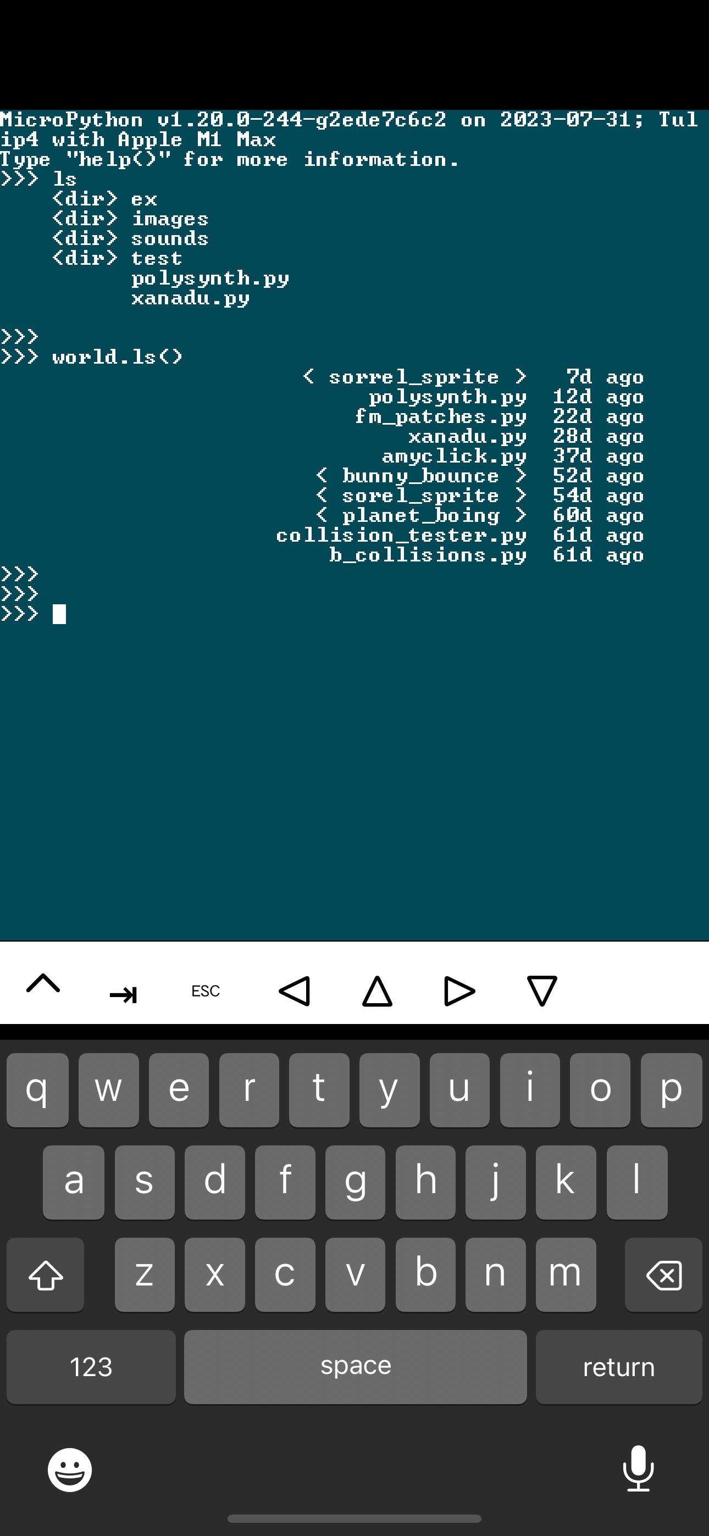
Docs/Amyboard/tulipcc-main/docs/pics/ios_1.png
