aTanguay/Enssemble.io/Docs/Amyboard/tulipcc-main/docs/pics/ios_2.png

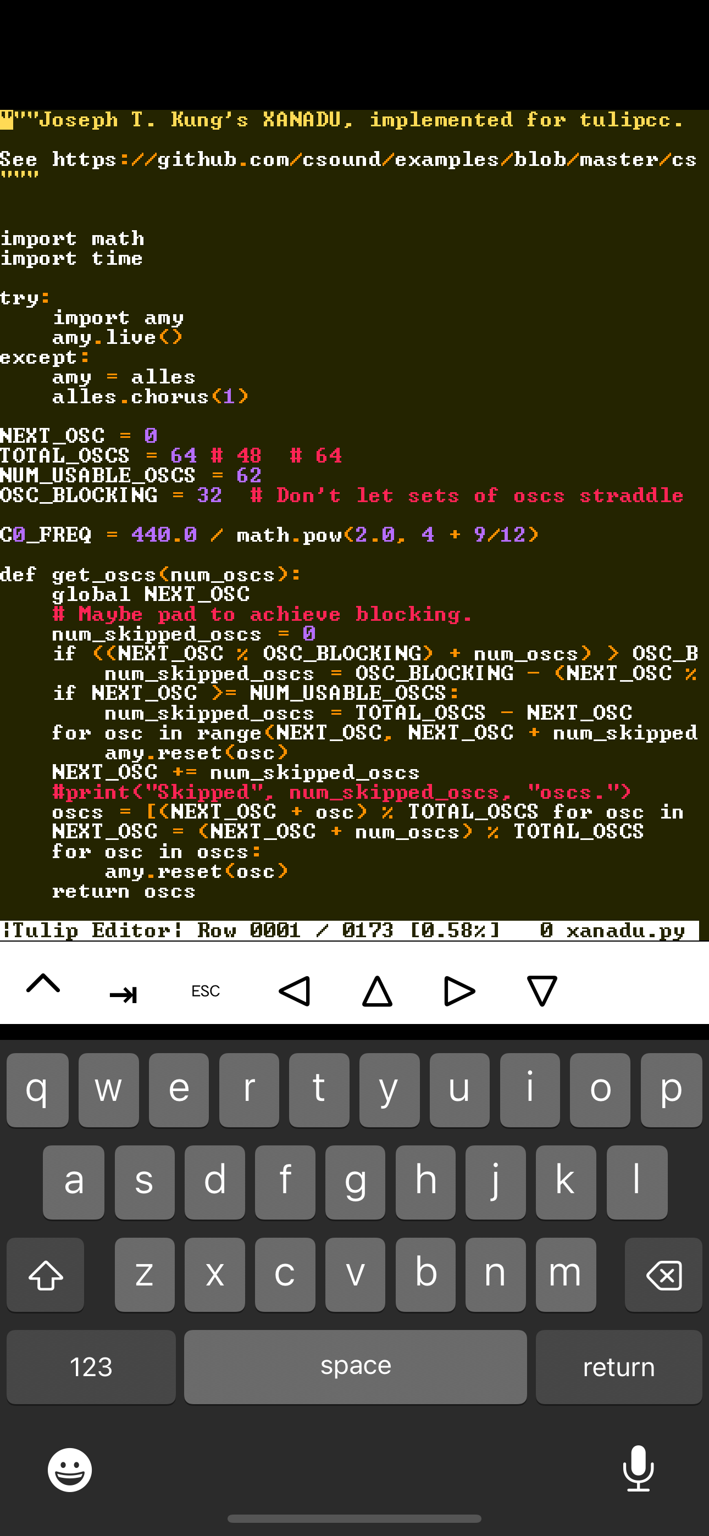
Docs/Amyboard/tulipcc-main/docs/pics/ios_2.png
