aTanguay/Enssemble.io/Docs/Amyboard/tulipcc-main/docs/pics/jampy.png

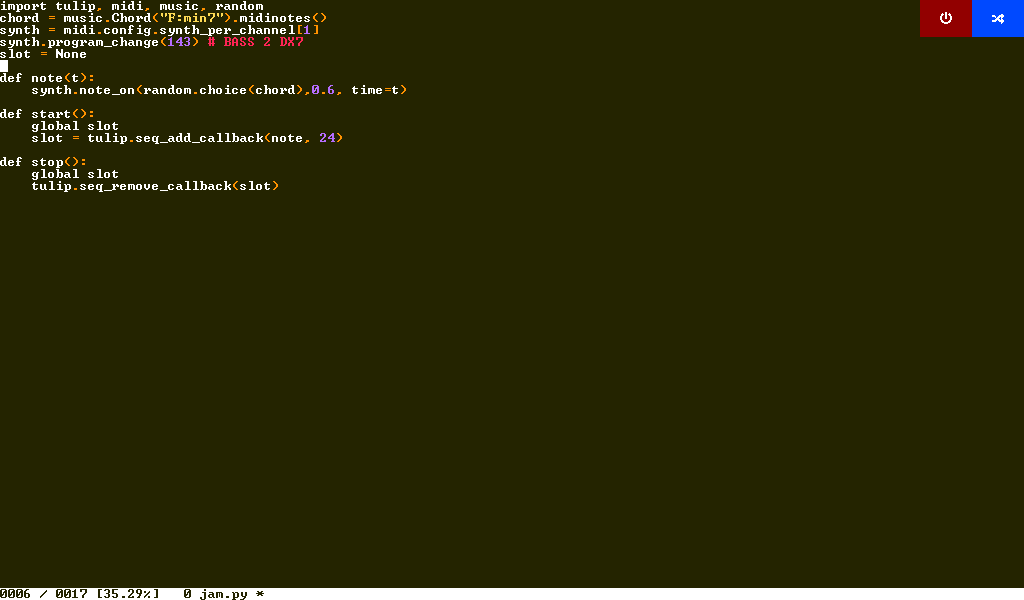
Docs/Amyboard/tulipcc-main/docs/pics/jampy.png
