aTanguay/Enssemble.io/Docs/Amyboard/tulipcc-main/docs/pics/keyboard.png

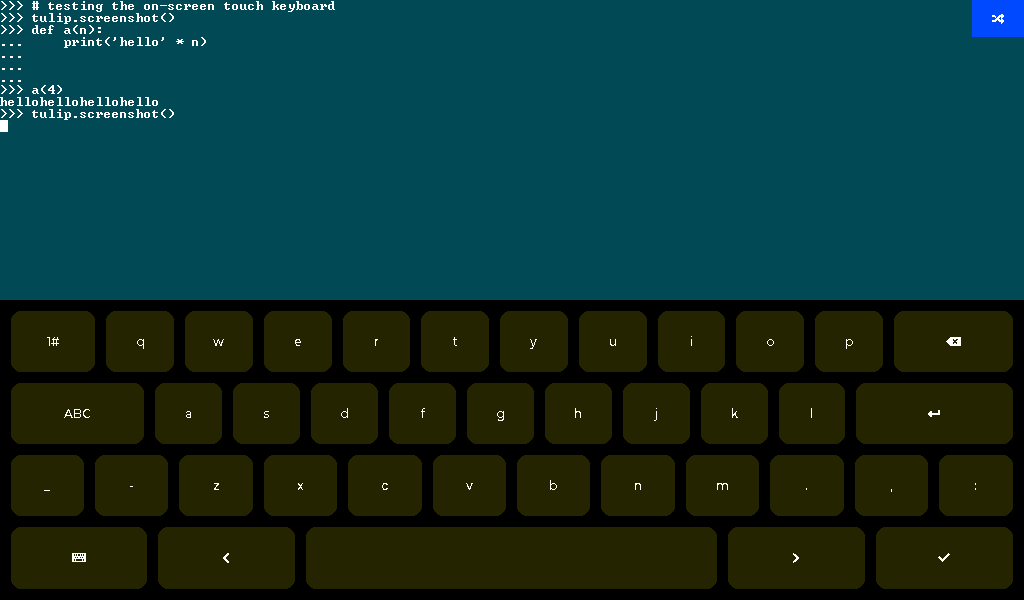
Docs/Amyboard/tulipcc-main/docs/pics/keyboard.png
