aTanguay/Enssemble.io/Docs/Amyboard/tulipcc-main/docs/pics/lines.png

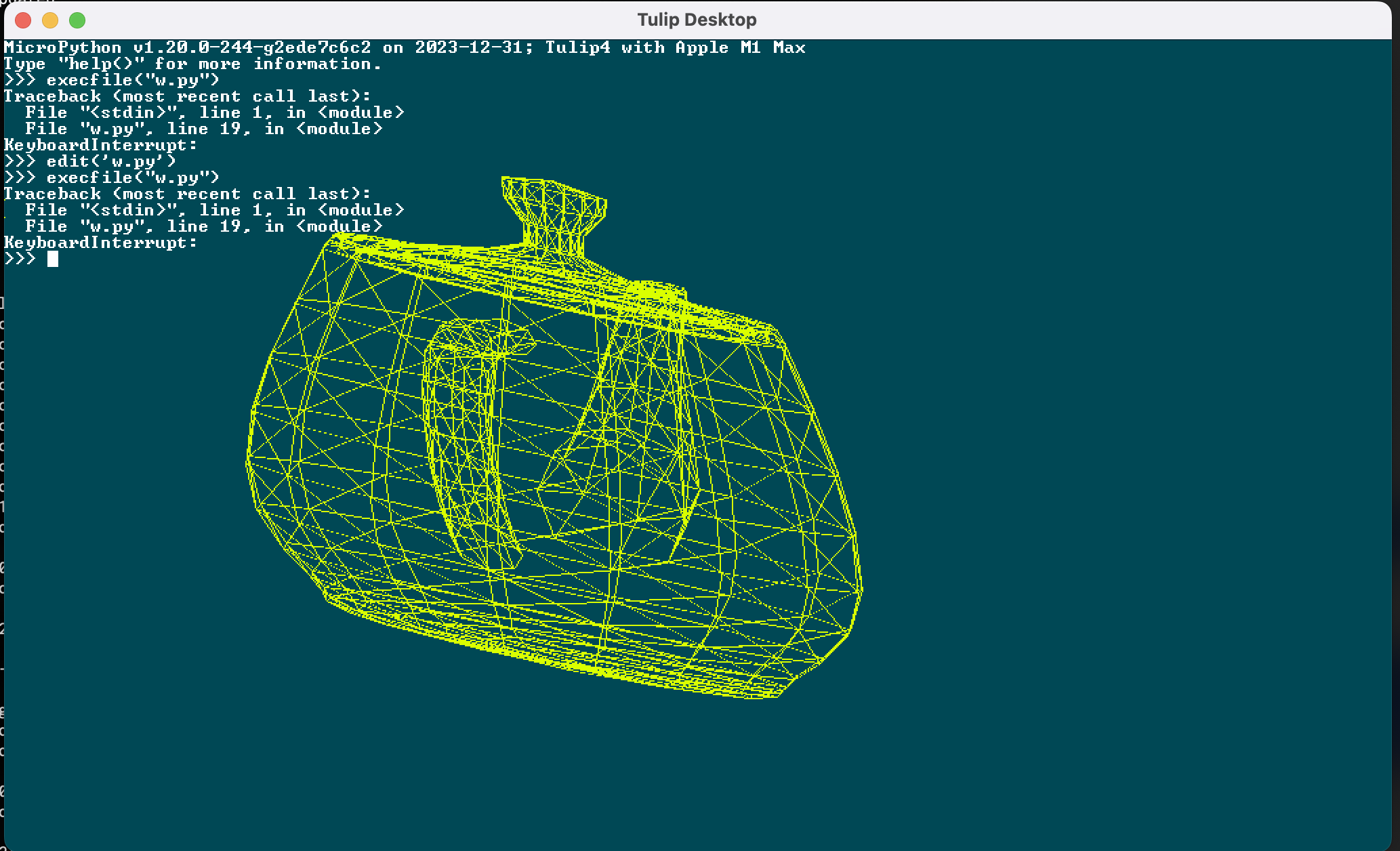
Docs/Amyboard/tulipcc-main/docs/pics/lines.png
