aTanguay/Enssemble.io/Docs/Amyboard/tulipcc-main/docs/pics/nicoboard-case.jpg

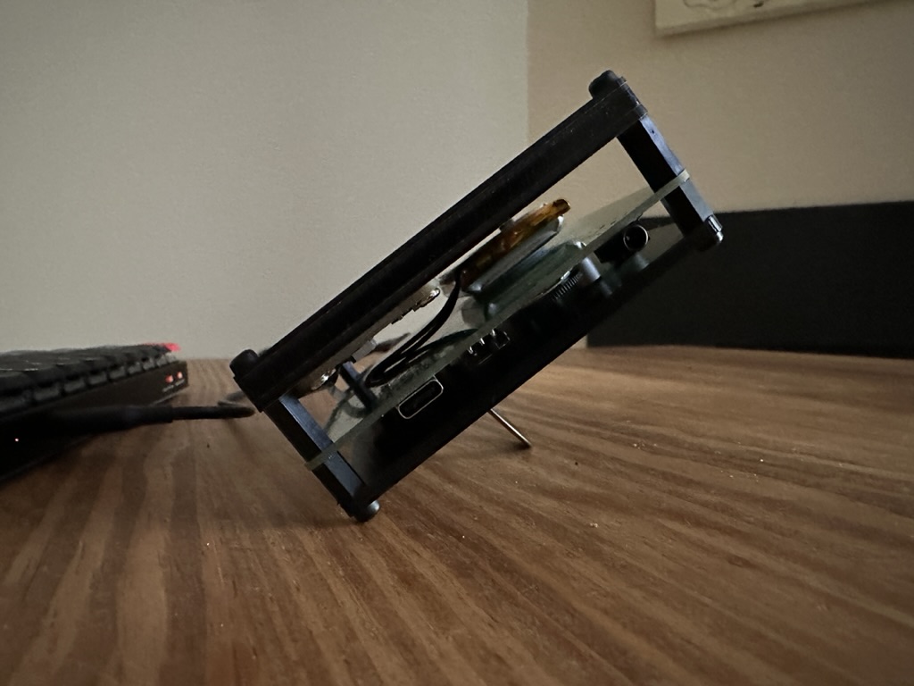
Docs/Amyboard/tulipcc-main/docs/pics/nicoboard-case.jpg
