aTanguay/Enssemble.io/Docs/Amyboard/tulipcc-main/docs/pics/nicoboard-pcb.png

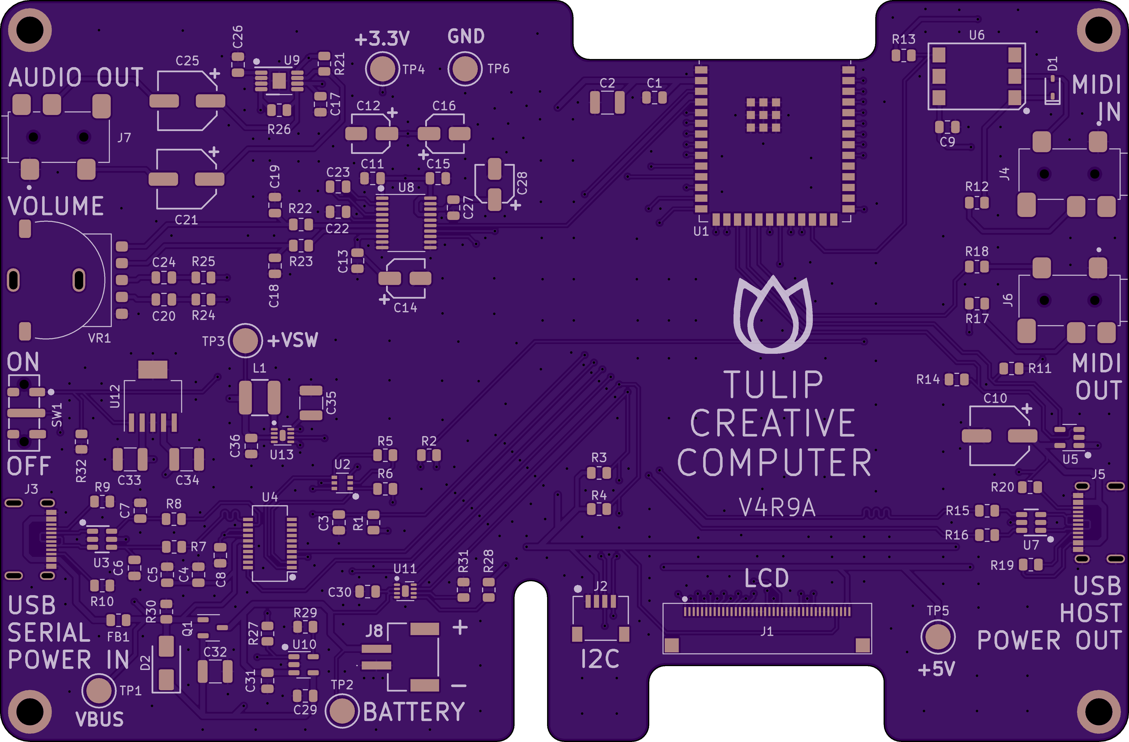
Docs/Amyboard/tulipcc-main/docs/pics/nicoboard-pcb.png
