aTanguay/Enssemble.io/Docs/Amyboard/tulipcc-main/docs/pics/nicoboard.jpg

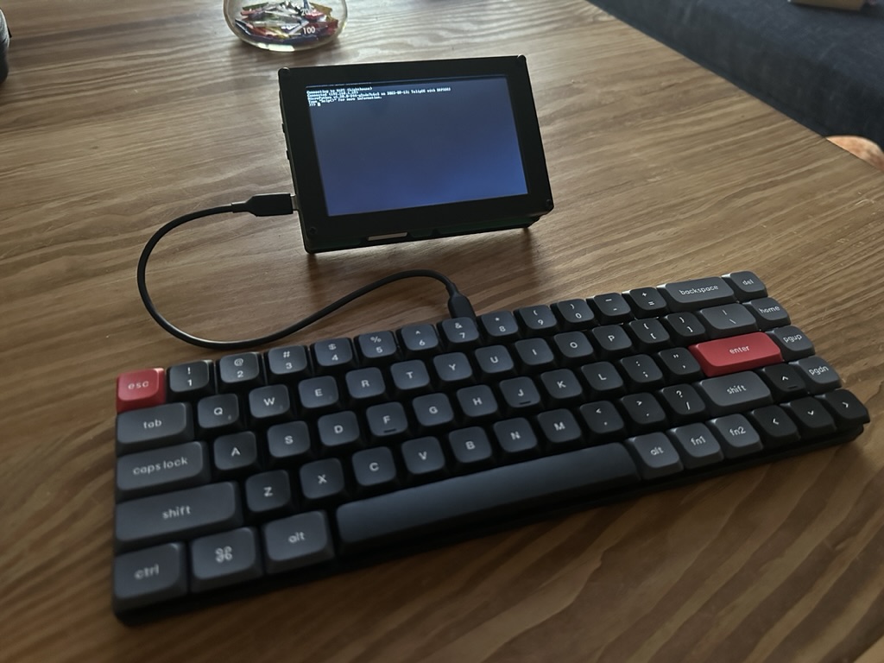
Docs/Amyboard/tulipcc-main/docs/pics/nicoboard.jpg
