aTanguay/Enssemble.io/Docs/Amyboard/tulipcc-main/docs/pics/repl.png

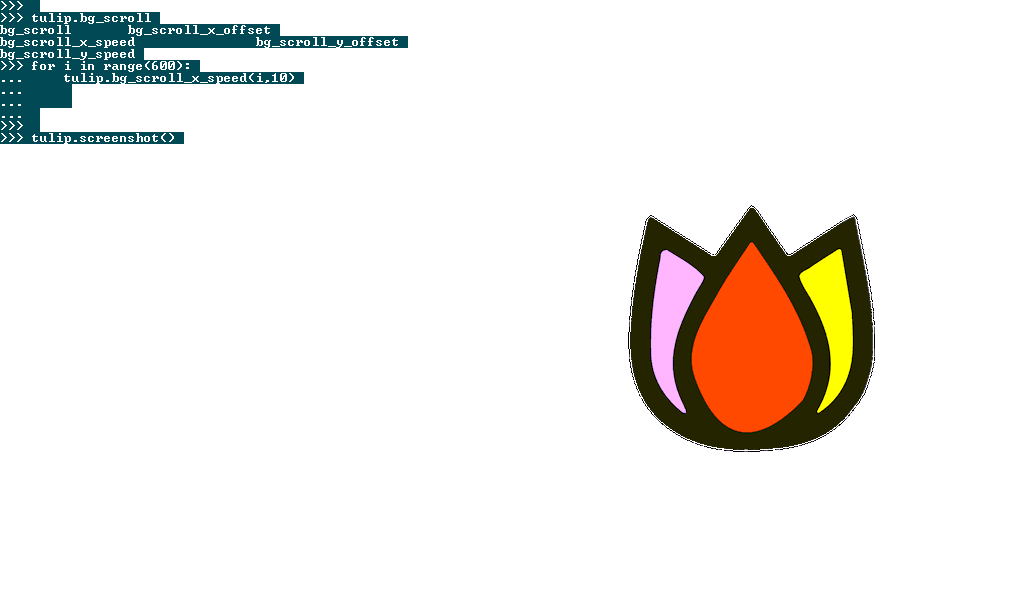
Docs/Amyboard/tulipcc-main/docs/pics/repl.png
