aTanguay/Enssemble.io/Docs/Amyboard/tulipcc-main/docs/pics/rgb332.png

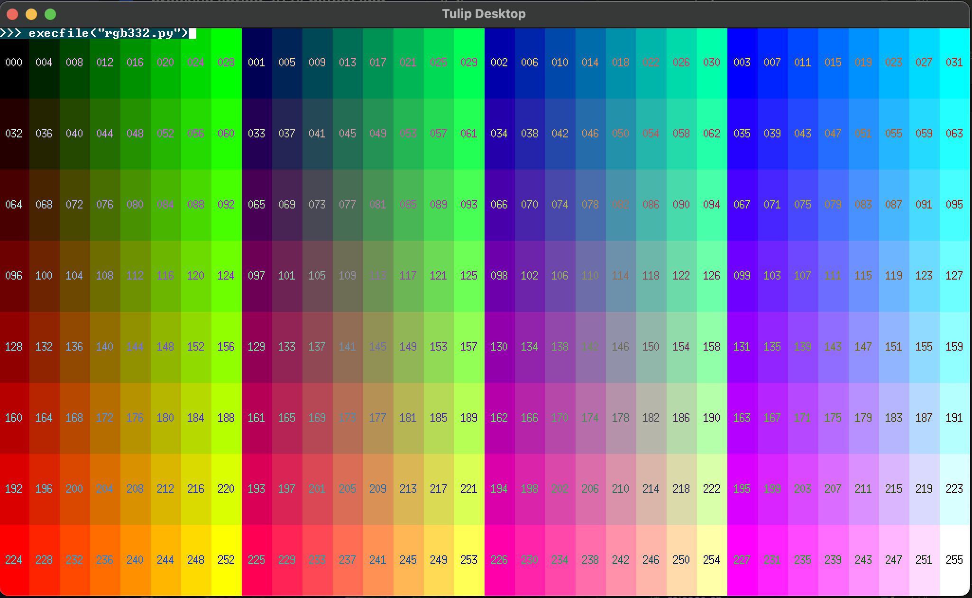
Docs/Amyboard/tulipcc-main/docs/pics/rgb332.png
