aTanguay/Enssemble.io/Docs/Amyboard/tulipcc-main/docs/pics/shorepine250.png

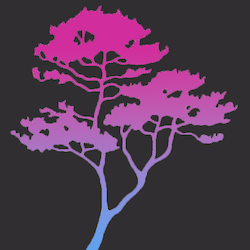
Docs/Amyboard/tulipcc-main/docs/pics/shorepine250.png
