aTanguay/Enssemble.io/Docs/Amyboard/tulipcc-main/docs/pics/sliders.png

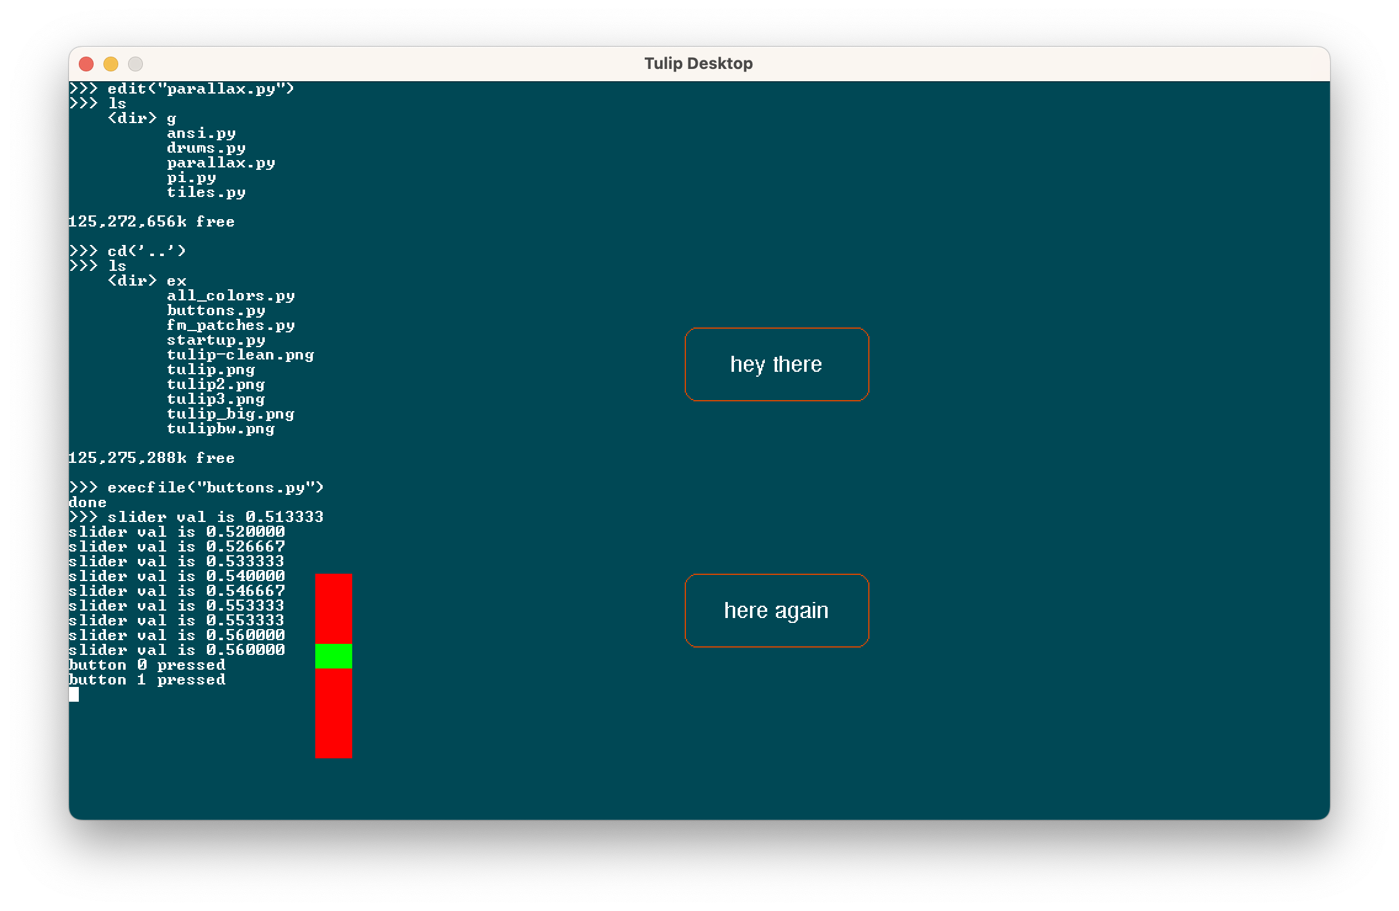
Docs/Amyboard/tulipcc-main/docs/pics/sliders.png
