aTanguay/Enssemble.io/Docs/Amyboard/tulipcc-main/docs/pics/tdeck.jpg

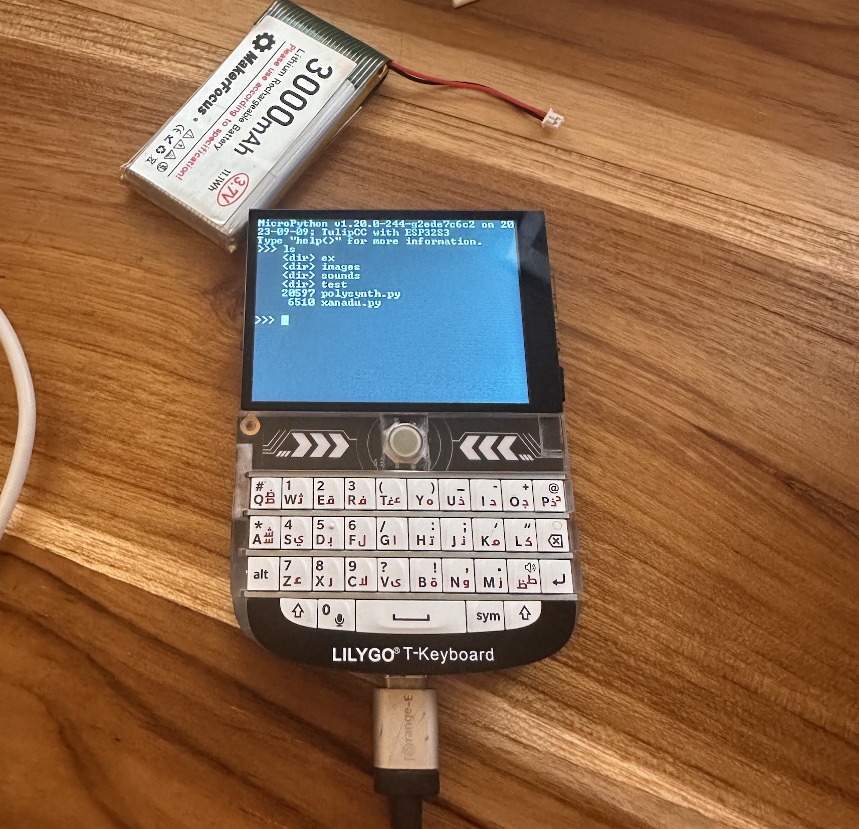
Docs/Amyboard/tulipcc-main/docs/pics/tdeck.jpg
