aTanguay/Enssemble.io/Docs/Amyboard/tulipcc-main/docs/pics/tdeck_editor.jpg

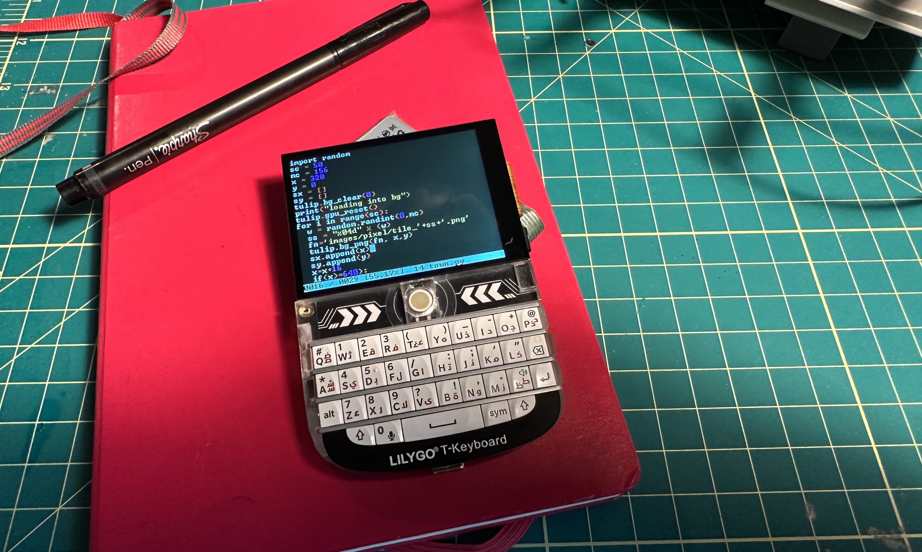
Docs/Amyboard/tulipcc-main/docs/pics/tdeck_editor.jpg
