aTanguay/Enssemble.io/Docs/Amyboard/tulipcc-main/docs/pics/tdeck_repl.jpg

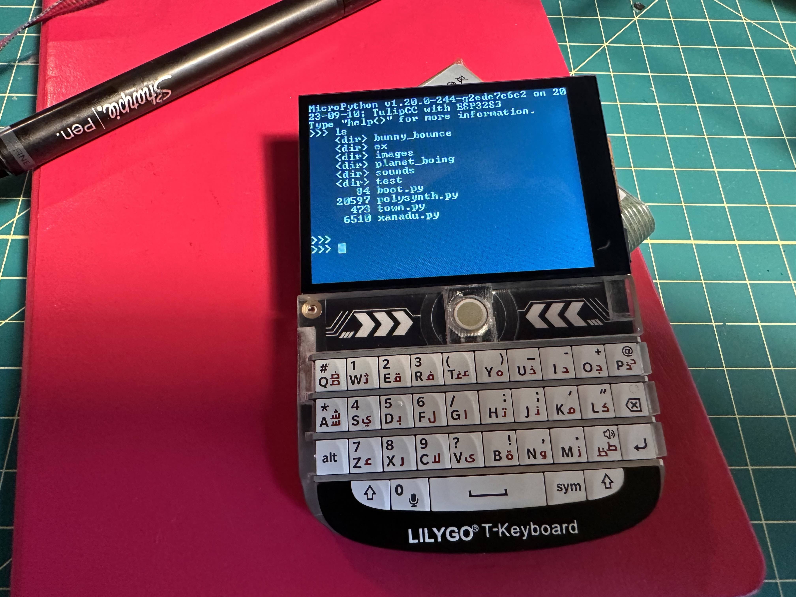
Docs/Amyboard/tulipcc-main/docs/pics/tdeck_repl.jpg
