aTanguay/Enssemble.io/Docs/Amyboard/tulipcc-main/docs/pics/tfb.png

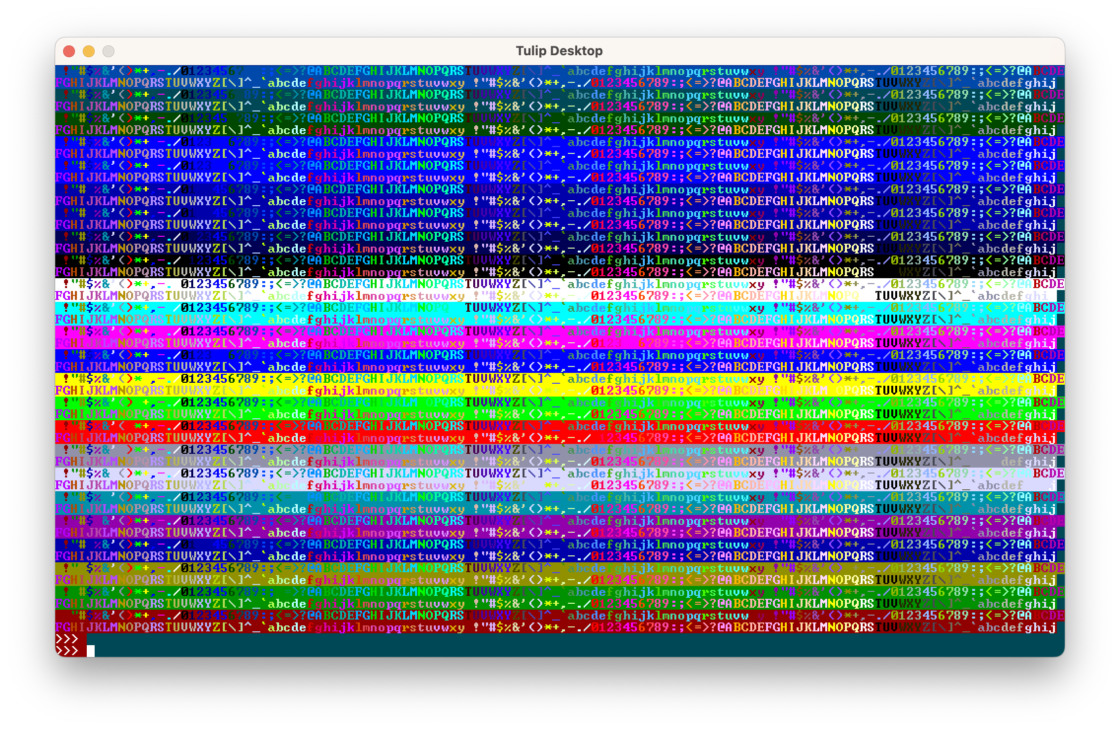
Docs/Amyboard/tulipcc-main/docs/pics/tfb.png
