aTanguay/Enssemble.io/Docs/Amyboard/tulipcc-main/docs/pics/tuilpv4r11ctp.jpg

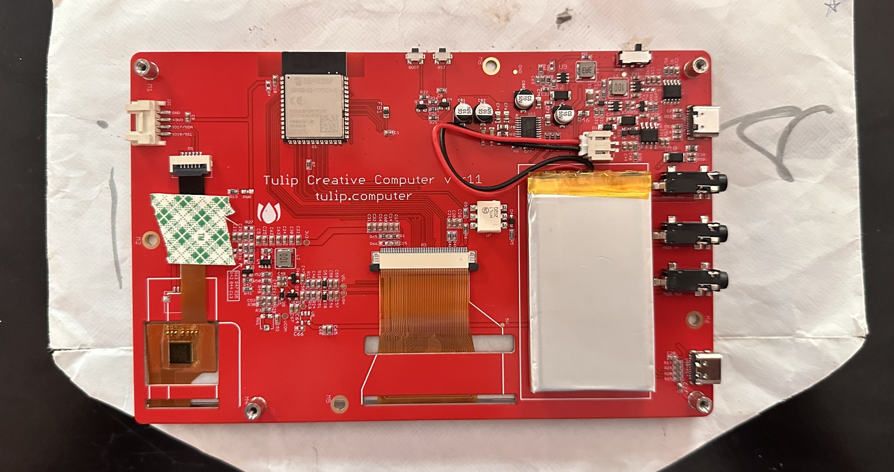
Docs/Amyboard/tulipcc-main/docs/pics/tuilpv4r11ctp.jpg
