aTanguay/Enssemble.io/Docs/Amyboard/tulipcc-main/docs/pics/tulip4r11firstboot.jpg

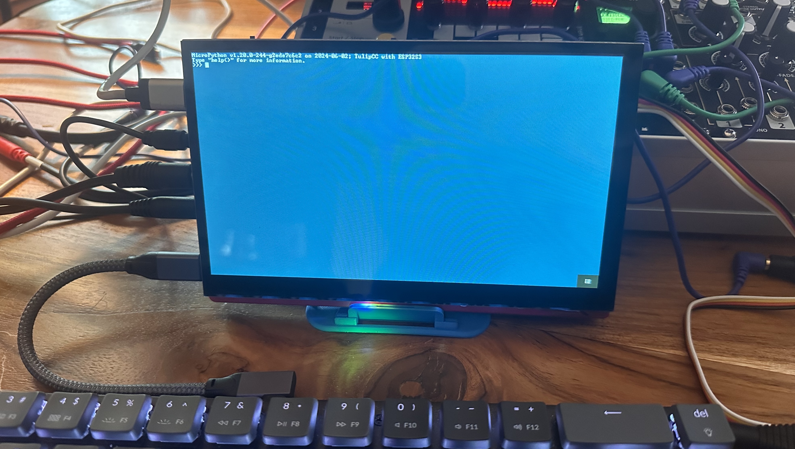
Docs/Amyboard/tulipcc-main/docs/pics/tulip4r11firstboot.jpg
