aTanguay/Enssemble.io/Docs/Amyboard/tulipcc-main/docs/pics/tulip-wide.jpg

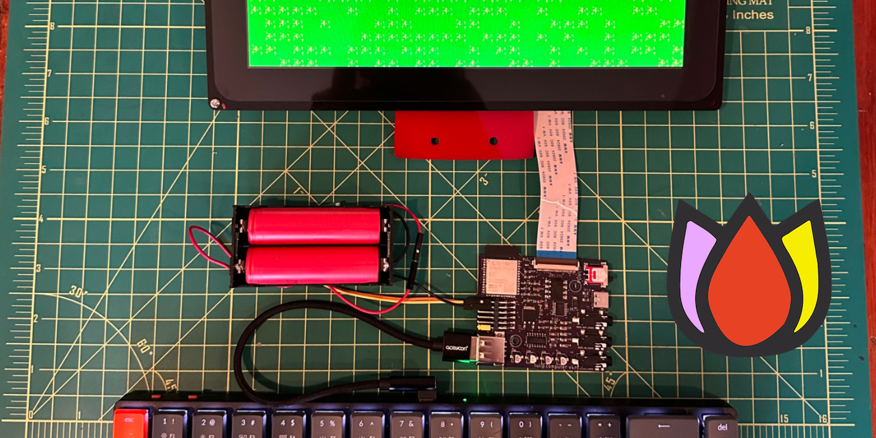
Docs/Amyboard/tulipcc-main/docs/pics/tulip-wide.jpg
