aTanguay/Enssemble.io/Docs/Amyboard/tulipcc-main/docs/pics/tulip_board_r7.jpg

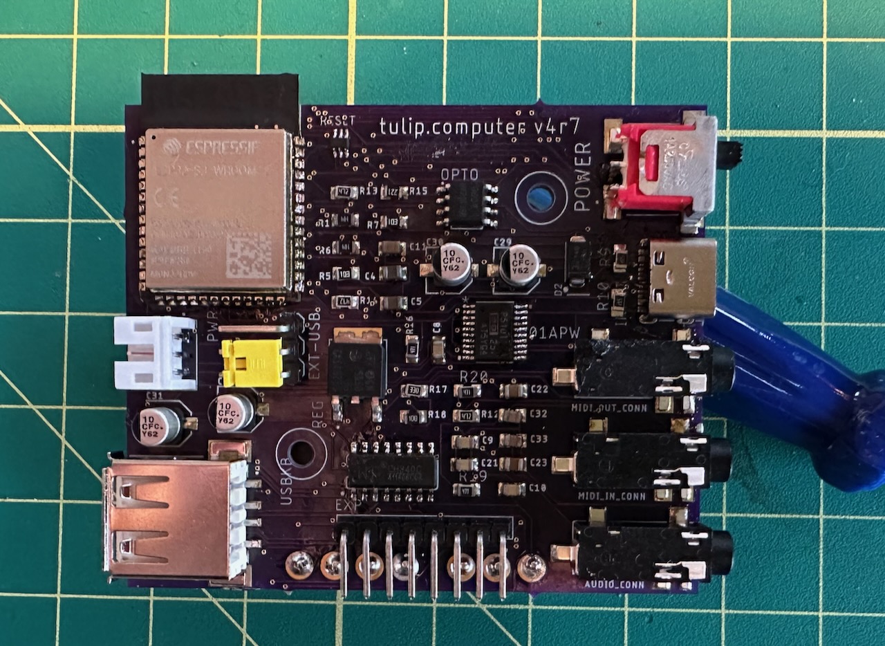
Docs/Amyboard/tulipcc-main/docs/pics/tulip_board_r7.jpg
