aTanguay/Enssemble.io/Docs/Amyboard/tulipcc-main/docs/pics/tulip_board_r7_battery.jpg

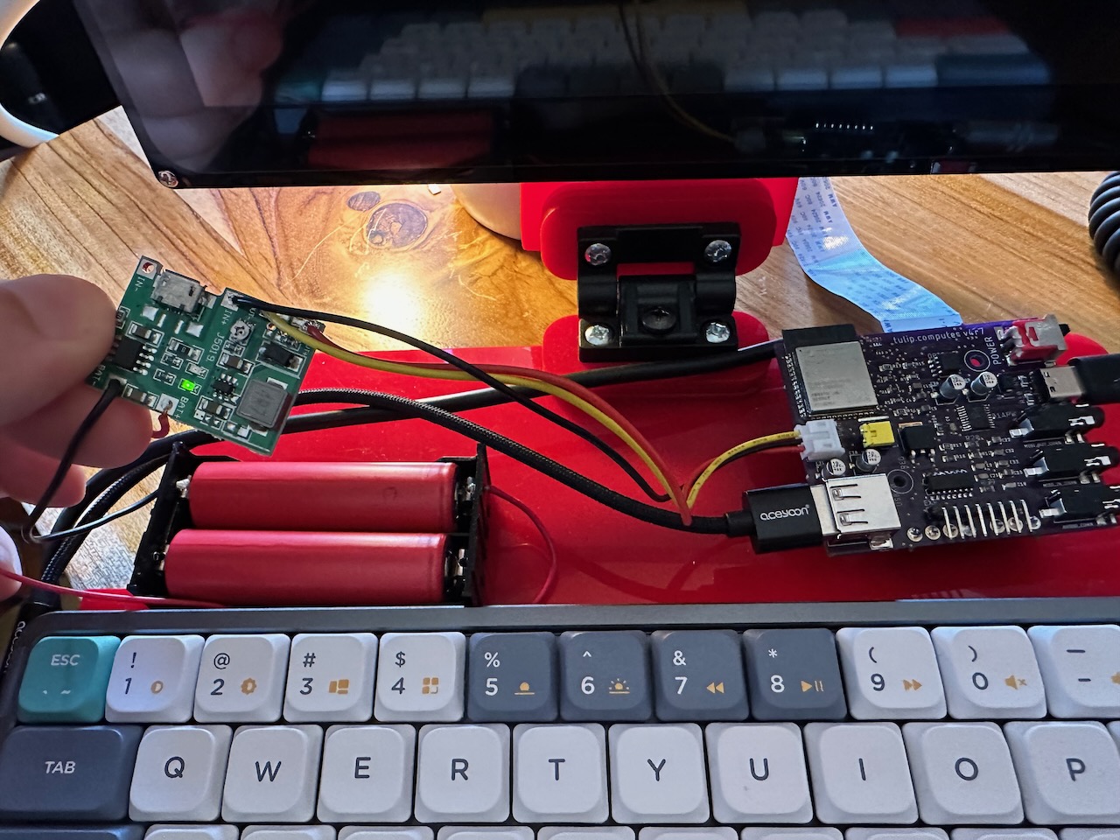
Docs/Amyboard/tulipcc-main/docs/pics/tulip_board_r7_battery.jpg
