aTanguay/Enssemble.io/Docs/Amyboard/tulipcc-main/docs/pics/tulipv4r11back.png

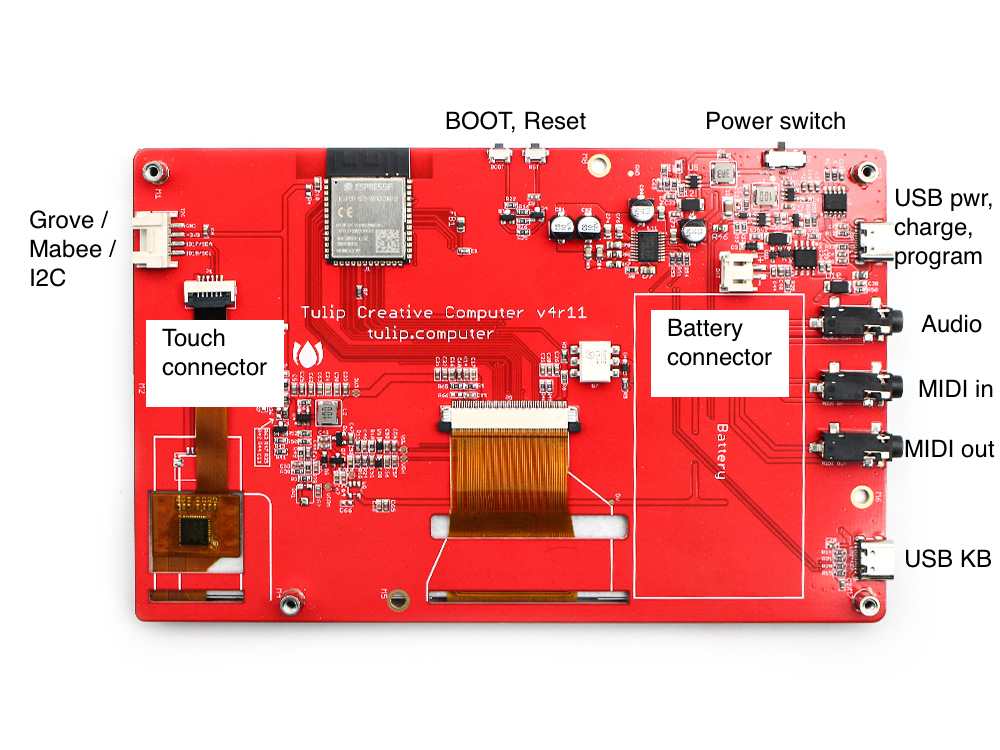
Docs/Amyboard/tulipcc-main/docs/pics/tulipv4r11back.png
