aTanguay/Enssemble.io/Docs/Amyboard/tulipcc-main/docs/pics/tulipweb.png

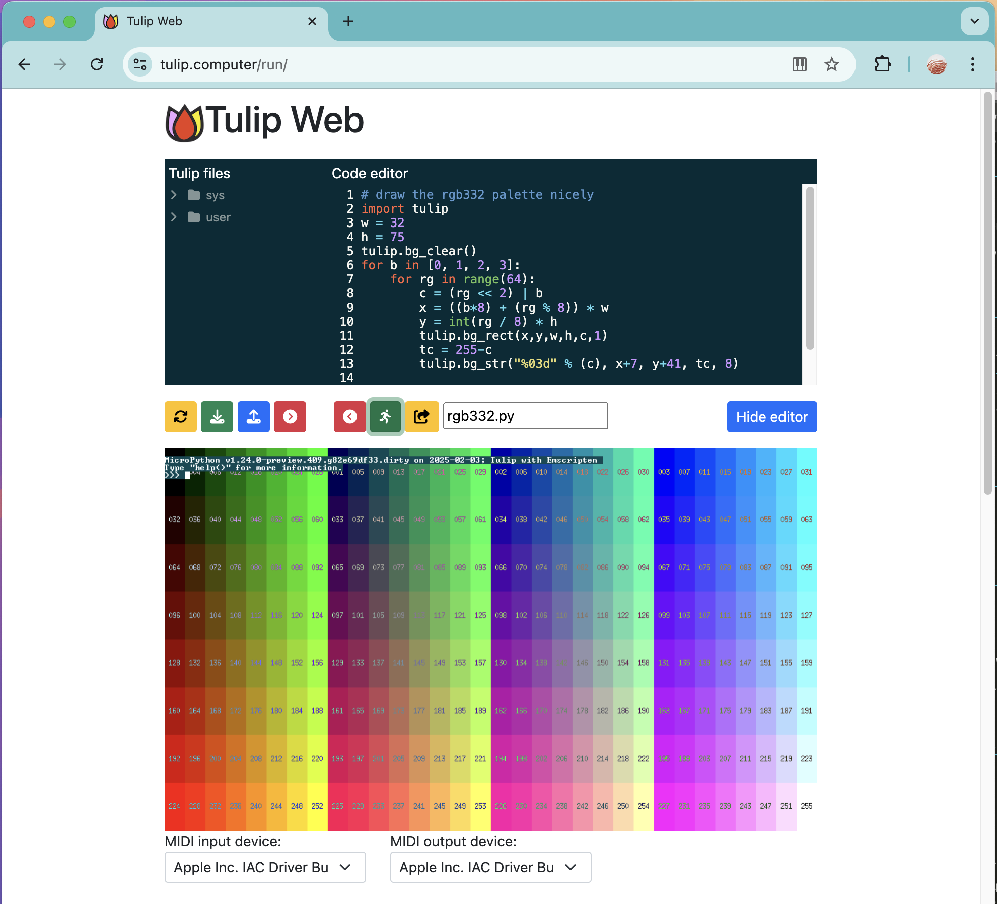
Docs/Amyboard/tulipcc-main/docs/pics/tulipweb.png
