aTanguay/Enssemble.io/Docs/Amyboard/tulipcc-main/docs/pics/voices.png

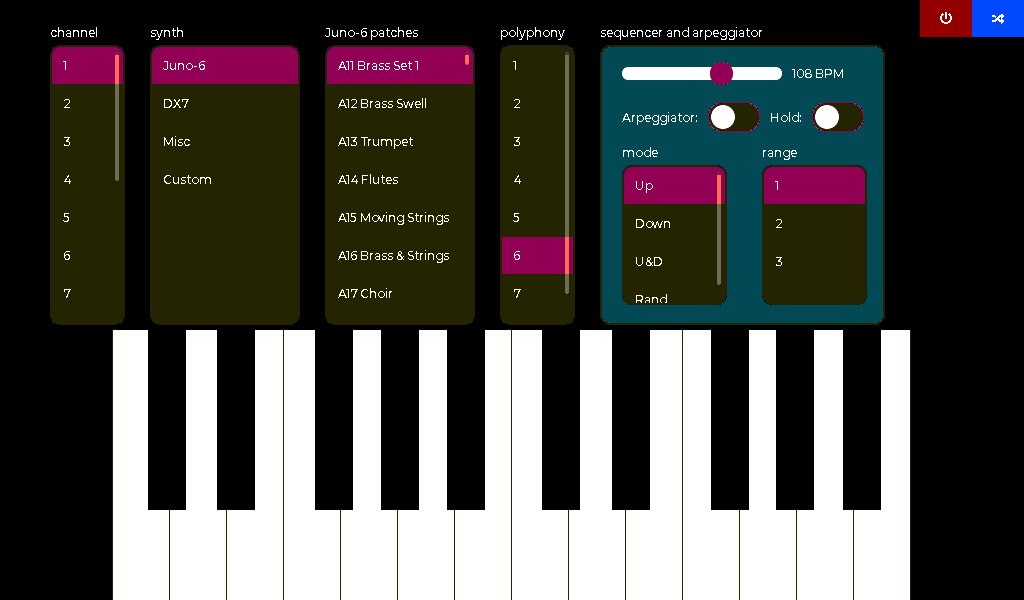
Docs/Amyboard/tulipcc-main/docs/pics/voices.png
