aTanguay/Enssemble.io/Docs/Amyboard/tulipcc-main/docs/pics/waves.png

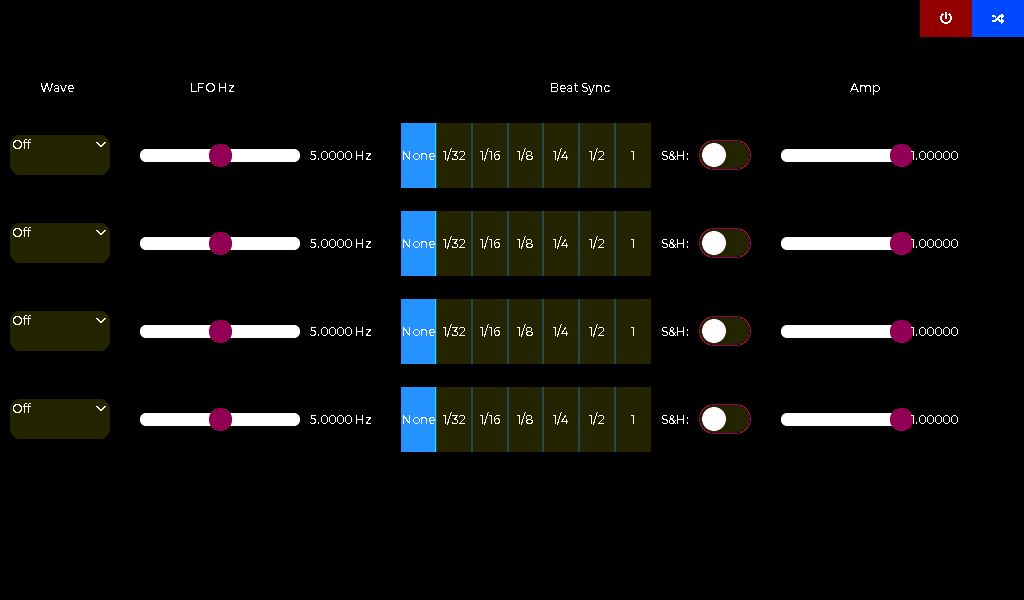
Docs/Amyboard/tulipcc-main/docs/pics/waves.png
