aTanguay/Enssemble.io/Docs/Amyboard/tulipcc-main/tulip/fs/tulip/ex/g/colorbars.png

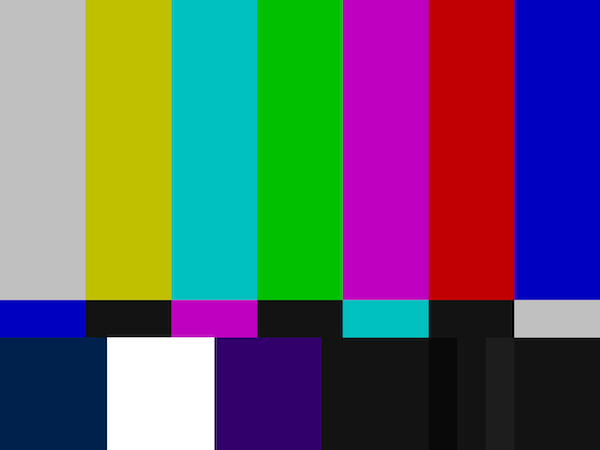
Docs/Amyboard/tulipcc-main/tulip/fs/tulip/ex/g/colorbars.png
