aTanguay/Enssemble.io/Docs/Amyboard/tulipcc-main/tulip/fs/tulip/ex/g/mountain-bg.png

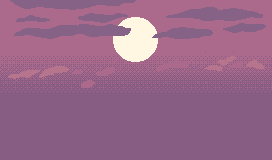
Docs/Amyboard/tulipcc-main/tulip/fs/tulip/ex/g/mountain-bg.png
