aTanguay/Enssemble.io/Docs/Amyboard/tulipcc-main/tulip/fs/tulip/ex/g/mountain-far.png

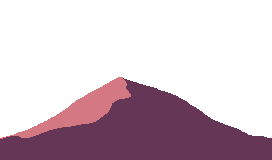
Docs/Amyboard/tulipcc-main/tulip/fs/tulip/ex/g/mountain-far.png
