aTanguay/Enssemble.io/Docs/Amyboard/tulipcc-main/tulip/fs/tulip/ex/g/trees-far.png

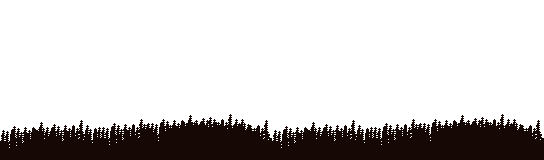
Docs/Amyboard/tulipcc-main/tulip/fs/tulip/ex/g/trees-far.png
