aTanguay/Enssemble.io/Docs/Amyboard/tulipcc-main/tulip/fs/tulip/ex/g/tulip3.png

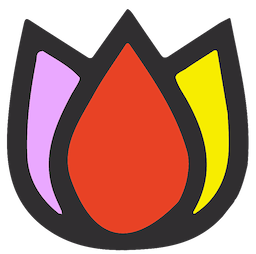
Docs/Amyboard/tulipcc-main/tulip/fs/tulip/ex/g/tulip3.png
