aTanguay/Enssemble.io/Docs/Amyboard/tulipcc-main/tulip/fs/tulip/ex/g/tulipbw.png

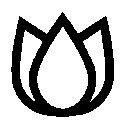
Docs/Amyboard/tulipcc-main/tulip/fs/tulip/ex/g/tulipbw.png
