aTanguay/Enssemble.io/Docs/XIAO MIDI Synthesizer/BoadShot_01.png

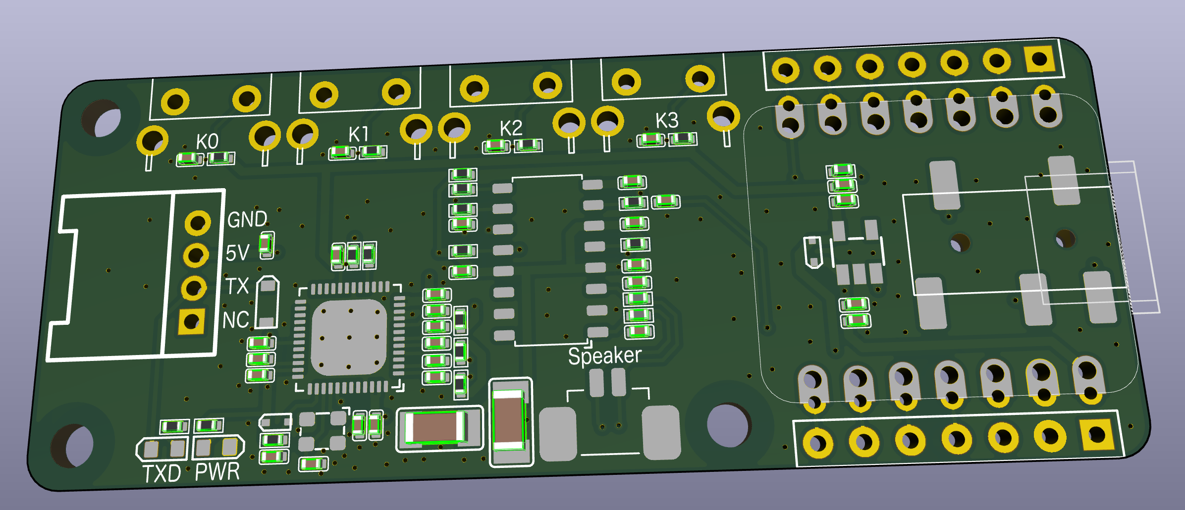
Docs/XIAO MIDI Synthesizer/BoadShot_01.png
