aTanguay/Enssemble.io/Docs/XIAO MIDI Synthesizer/BoadShot_02.png

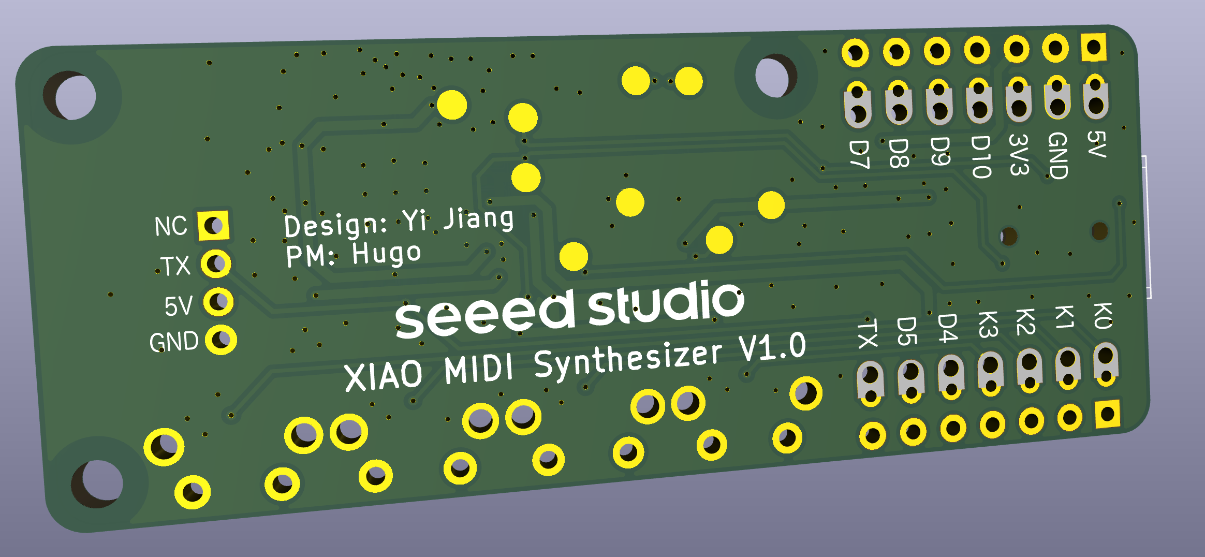
Docs/XIAO MIDI Synthesizer/BoadShot_02.png
