aTanguay/Enssemble.io/Docs/Amyboard/tulipcc-main/docs/pcbs/tulip4_board_v4r9/3dmodels/CAP_WE_865060345007.stp

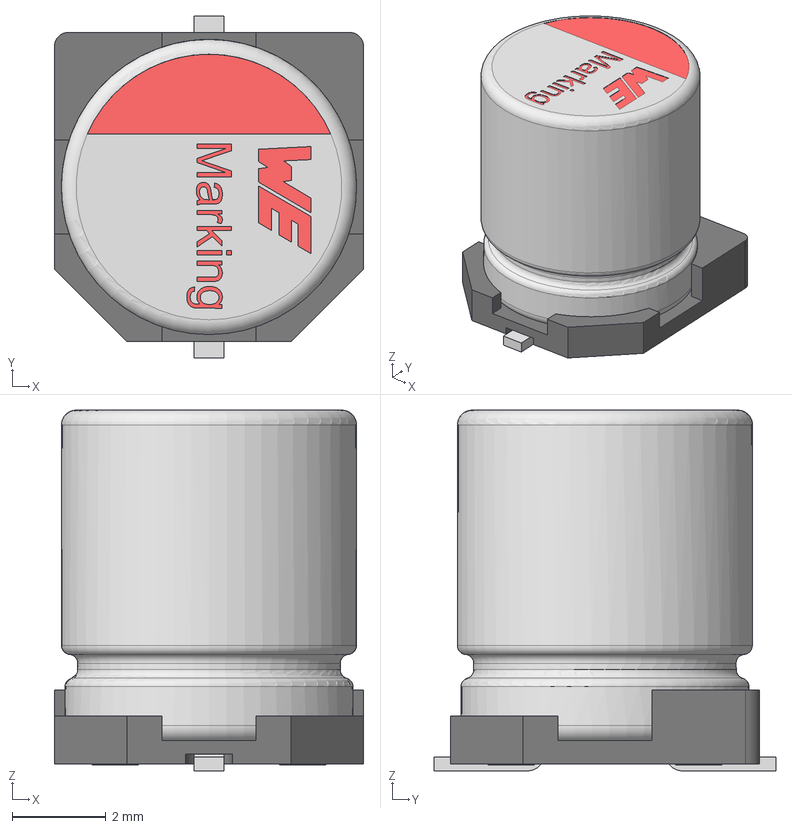
[picture p176: CAD file, 2026-07-14]
Docs/Amyboard/tulipcc-main/docs/pcbs/tulip4_board_v4r9/3dmodels/CAP_WE_865060345007.stp
6.60 x 7.30 x 7.70 mm
capicitor_6.3x7.7x2.2
Base_Φ6_3Capacitor
