aTanguay/Enssemble.io/Docs/Amyboard/tulipcc-main/docs/pcbs/tulip4_board_v4r9/3dmodels/SOT-23-3.step

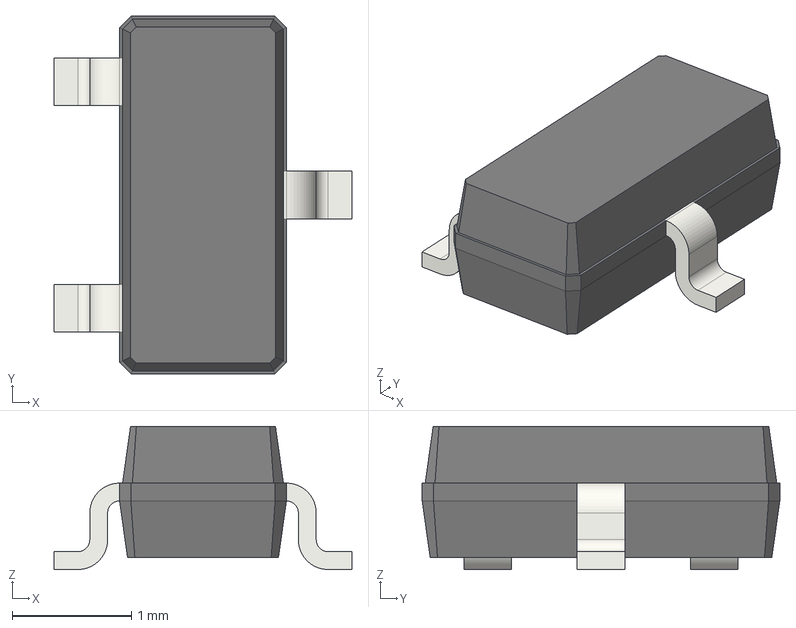
[picture p177: CAD file, 2026-07-14]
Docs/Amyboard/tulipcc-main/docs/pcbs/tulip4_board_v4r9/3dmodels/SOT-23-3.step
2.50 x 3.00 x 1.20 mm
