aTanguay/Enssemble.io/Docs/Amyboard/tulipcc-main/docs/pcbs/tulip4_board_v4r9/3dmodels/CUI_DEVICES_SJ2-35863B1-SMT-TR.step

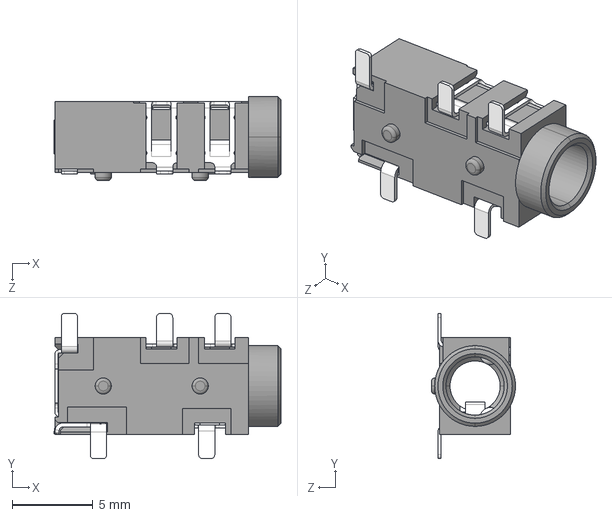
[picture p178: CAD file, 2026-07-14]
Docs/Amyboard/tulipcc-main/docs/pcbs/tulip4_board_v4r9/3dmodels/CUI_DEVICES_SJ2-35863B1-SMT-TR.step
14.0 x 9.00 x 5.20 mm
