aTanguay/Enssemble.io/Docs/Amyboard/tulipcc-main/docs/pcbs/tulip4_board_v4r9/3dmodels/RK10J1_R.step

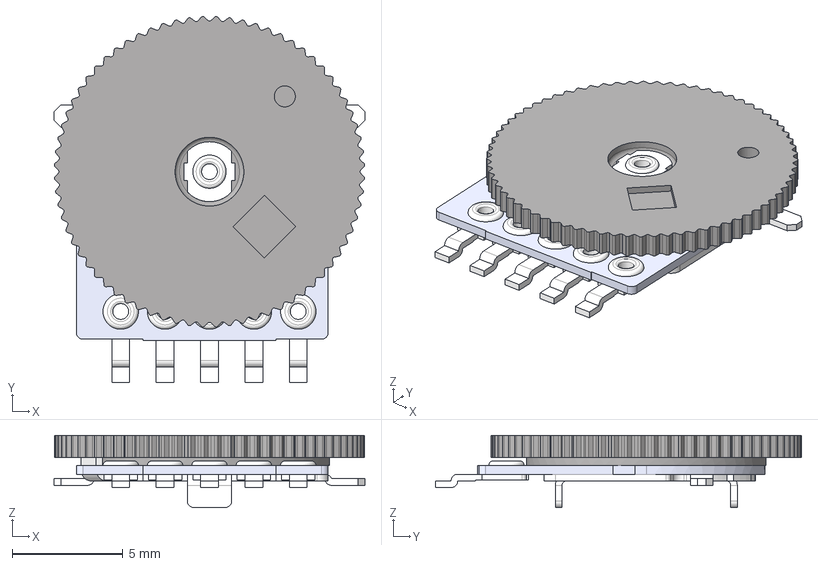
[picture p179: CAD file, 2026-07-14]
Docs/Amyboard/tulipcc-main/docs/pcbs/tulip4_board_v4r9/3dmodels/RK10J1_R.step
14.0 x 16.5 x 3.25 mm
