aTanguay/Enssemble.io/Docs/Amyboard/tulipcc-main/docs/pcbs/tulip4_board_v4r9/3dmodels/R_0805_2012.step

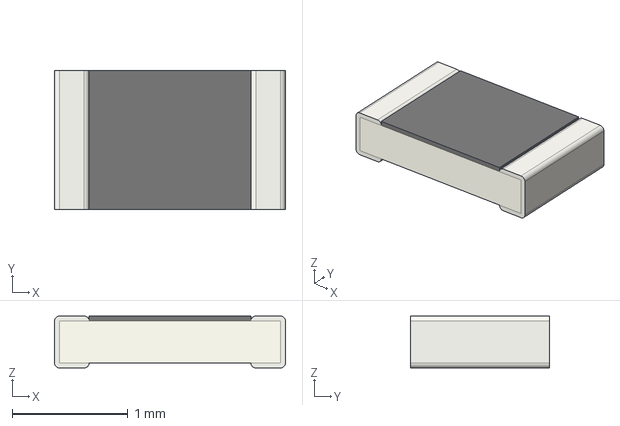
[picture p180: CAD file, 2026-07-14]
Docs/Amyboard/tulipcc-main/docs/pcbs/tulip4_board_v4r9/3dmodels/R_0805_2012.step
2.00 x 1.20 x 0.45 mm
