aTanguay/Enssemble.io/Docs/Amyboard/tulipcc-main/docs/pcbs/tulip4_board_v4r9/3dmodels/SOT-363_SC-70-6.step

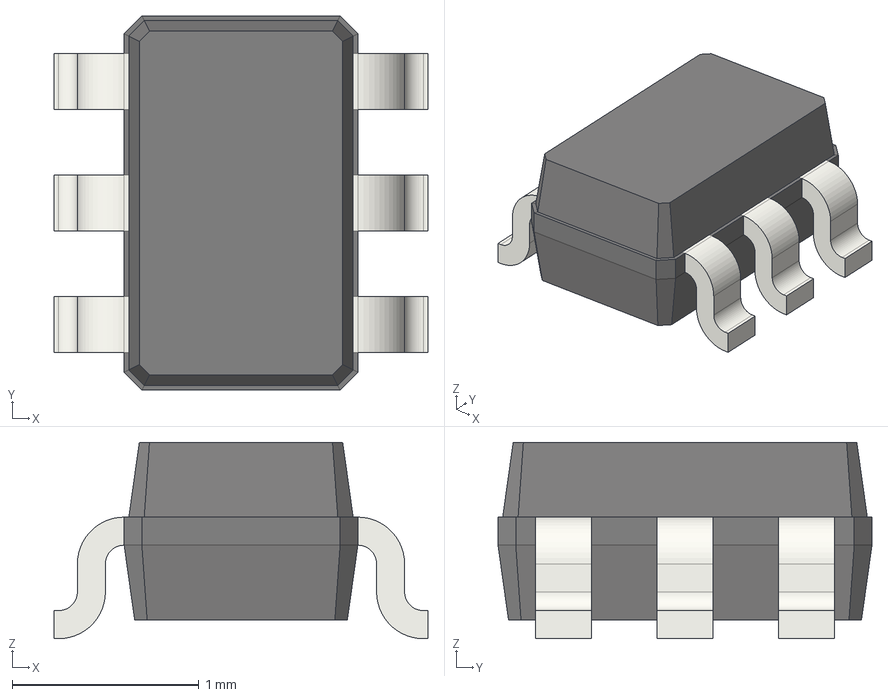
[picture p181: CAD file, 2026-07-14]
Docs/Amyboard/tulipcc-main/docs/pcbs/tulip4_board_v4r9/3dmodels/SOT-363_SC-70-6.step
2.00 x 2.00 x 1.05 mm
