aTanguay/Enssemble.io/Docs/Amyboard/tulipcc-main/docs/pcbs/tulip4_board_v4r9/3dmodels/CAP_WE_865060340001.stp

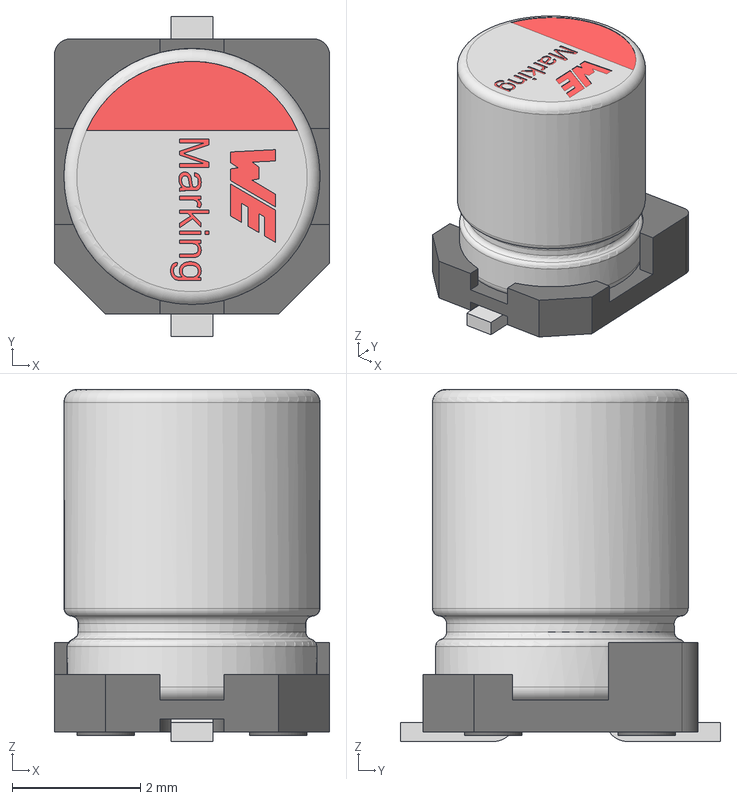
[picture p182: CAD file, 2026-07-14]
Docs/Amyboard/tulipcc-main/docs/pcbs/tulip4_board_v4r9/3dmodels/CAP_WE_865060340001.stp
4.30 x 5.00 x 5.50 mm
capicitor_4x5.5x1
Base_Φ4Capacitor
