aTanguay/Enssemble.io/Docs/Amyboard/tulipcc-main/docs/pcbs/tulip4_board_v4r9/3dmodels/C_0805_2012Metric.step

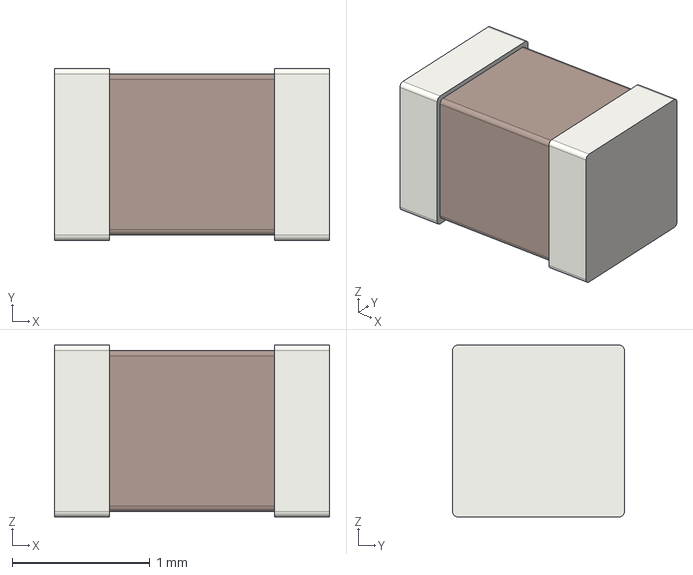
[picture p184: CAD file, 2026-07-14]
Docs/Amyboard/tulipcc-main/docs/pcbs/tulip4_board_v4r9/3dmodels/C_0805_2012Metric.step
2.00 x 1.25 x 1.25 mm
