aTanguay/Enssemble.io/Docs/Amyboard/tulipcc-main/docs/pcbs/tulip4_board_v4r9/3dmodels/SSOP-16_3.9x4.9mm_P0.635mm.step

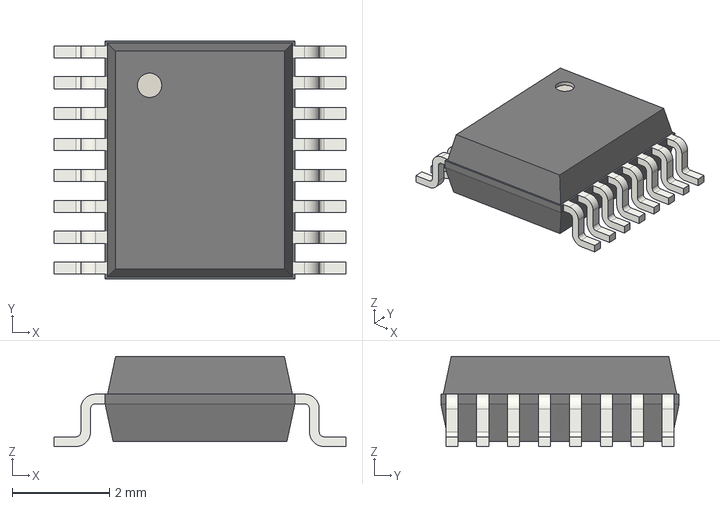
[picture p185: CAD file, 2026-07-14]
Docs/Amyboard/tulipcc-main/docs/pcbs/tulip4_board_v4r9/3dmodels/SSOP-16_3.9x4.9mm_P0.635mm.step
6.00 x 4.90 x 1.85 mm
