aTanguay/Enssemble.io/Docs/Amyboard/tulipcc-main/docs/pcbs/tulip4_board_v4r9/3dmodels/C_1210_3225Metric.step

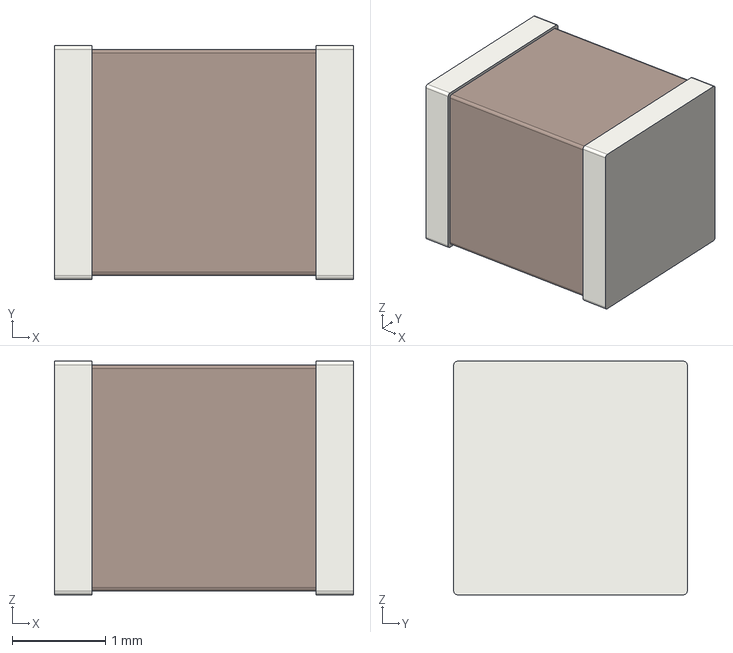
[picture p186: CAD file, 2026-07-14]
Docs/Amyboard/tulipcc-main/docs/pcbs/tulip4_board_v4r9/3dmodels/C_1210_3225Metric.step
3.20 x 2.50 x 2.50 mm
