aTanguay/Enssemble.io/Docs/Amyboard/tulipcc-main/lv_binding_micropython_tulip/examples/png_decoder_test.png

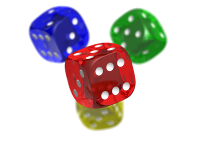
Docs/Amyboard/tulipcc-main/lv_binding_micropython_tulip/examples/png_decoder_test.png
