aTanguay/Enssemble.io/SeeedXiaoMIDI/NSMBL_Synth/main/buttons.c

#include "buttons.h"
#include "config.h"

#include "driver/gpio.h"
#include "esp_timer.h"

typedef struct {
    uint8_t  pin;
    bool     pressed;        // debounced state (true = held down)
    uint32_t press_time;
    bool     long_fired;
    int      last_raw;       // last raw level read, for debounce
    uint32_t last_change;    // when last_raw last changed
} button_state_t;

static button_state_t s_buttons[4];
static button_cb_t s_on_short;
static button_cb_t s_on_long;

static uint32_t now_ms(void)
{
    return (uint32_t)(esp_timer_get_time() / 1000);
}

void buttons_init(button_cb_t on_short, button_cb_t on_long)
{
    s_on_short = on_short;
    s_on_long  = on_long;

    const uint8_t pins[] = { BUTTON_0_PIN, BUTTON_1_PIN, BUTTON_2_PIN, BUTTON_3_PIN };

    for (int i = 0; i < 4; i++) {
        s_buttons[i].pin = pins[i];
        s_buttons[i].pressed = false;
        s_buttons[i].long_fired = false;

        // Match Arduino's pinMode(): reset the pad to a clean GPIO state first,
        // detaching any peripheral/matrix routing left on it, before configuring
        // it as a pulled-up input.
        gpio_reset_pin(pins[i]);

        gpio_config_t cfg = {
            .pin_bit_mask = (1ULL << pins[i]),
            .mode         = GPIO_MODE_INPUT,
            .pull_up_en   = GPIO_PULLUP_ENABLE,
            .pull_down_en = GPIO_PULLDOWN_DISABLE,
            .intr_type    = GPIO_INTR_DISABLE,
        };
        gpio_config(&cfg);

        s_buttons[i].last_raw    = gpio_get_level(pins[i]);
        s_buttons[i].last_change = 0;
    }
}

void buttons_poll(void)
{
    uint32_t t = now_ms();

    for (int i = 0; i < 4; i++) {
        int raw = gpio_get_level(s_buttons[i].pin);

        // Debounce: restart the settle timer whenever the raw level moves, and
        // only act on a level that has been stable for DEBOUNCE_MS.
        if (raw != s_buttons[i].last_raw) {
            s_buttons[i].last_raw    = raw;
            s_buttons[i].last_change = t;
            continue;
        }
        if (t - s_buttons[i].last_change < DEBOUNCE_MS) {
            continue;
        }

        bool down = (raw == 0);  // active LOW

        if (down && !s_buttons[i].pressed) {
            s_buttons[i].pressed    = true;
            s_buttons[i].press_time = t;
            s_buttons[i].long_fired = false;
        }
        else if (!down && s_buttons[i].pressed) {
            s_buttons[i].pressed = false;
            if (!s_buttons[i].long_fired && (t - s_buttons[i].press_time < LONG_PRESS_MS)) {
                if (s_on_short) s_on_short(i);
            }
        }
        else if (down && s_buttons[i].pressed && !s_buttons[i].long_fired) {
            if (t - s_buttons[i].press_time >= LONG_PRESS_MS) {
                s_buttons[i].long_fired = true;
                if (s_on_long) s_on_long(i);
            }
        }
    }
}
