aTanguay/Enssemble.io/AmyBoard/NSMBL_SampleKits/main/sd_card.c

#include "sd_card.h"
#include "config.h"

#include "esp_log.h"
#include "esp_vfs_fat.h"
#include "driver/sdspi_host.h"
#include "driver/spi_common.h"
#include "sdmmc_cmd.h"

static const char *TAG = "sd_card";

esp_err_t sd_card_init(void)
{
    esp_vfs_fat_sdmmc_mount_config_t mount_config = {
        .format_if_mount_failed = false,
        .max_files = 5,
        .allocation_unit_size = 16 * 1024,
    };

    sdmmc_host_t host = SDSPI_HOST_DEFAULT();

    spi_bus_config_t bus_cfg = {
        .mosi_io_num = SD_MOSI,
        .miso_io_num = SD_MISO,
        .sclk_io_num = SD_CLK,
        .quadwp_io_num = -1,
        .quadhd_io_num = -1,
        .max_transfer_sz = 4096,
    };

    esp_err_t ret = spi_bus_initialize(host.slot, &bus_cfg, SDSPI_DEFAULT_DMA);
    if (ret != ESP_OK) {
        ESP_LOGE(TAG, "Failed to initialize SPI bus: %s", esp_err_to_name(ret));
        return ret;
    }

    sdspi_device_config_t slot_config = SDSPI_DEVICE_CONFIG_DEFAULT();
    slot_config.gpio_cs = SD_CS;
    slot_config.host_id = host.slot;

    sdmmc_card_t *card;
    ret = esp_vfs_fat_sdspi_mount("/sdcard", &host, &slot_config, &mount_config, &card);
    if (ret != ESP_OK) {
        ESP_LOGE(TAG, "Failed to mount SD card: %s", esp_err_to_name(ret));
        return ret;
    }

    ESP_LOGI(TAG, "SD card mounted");
    sdmmc_card_print_info(stdout, card);

    return ESP_OK;
}
